victorstoica114/UWB_Module_ESP_IDF/reports/uwb_dynamic_static_comparison_20260812.pdf

# Dynamic and static UWB comparison

## FlexTDOA, Native DS-TWR and Passive DS-TWR

Final field campaign of August 12, 2026

Platform: | 5 ESP32-S3 + DW3000 modules, Raspberry Pi collector
Topology: | M1 tag; M2, M3, M4 and M5 anchors
Radio: | UWB channel 9; configured 40 MHz SPI
Firmware branch: | localization-raw-calibration
UWB evidence: | six complete August 12 JSONL captures; raw and position-only EKF
RTK evidence: | GPS-only reference captures from August 6

Main result. All three protocols produced complete raw dynamic and static datasets. Independent dynamic rates are approximately 25.0 Hz Flex, 25.4 Hz Native and 22.6 Hz Passive. Raw static RMS is 2.3–2.4 cm. The position-only adaptive EKF materially reduces static jitter and dynamic sample-to-sample spikes, while raw UWB remains the permanent audit stream.

Reproducible technical report

## Contents

1 Executive summary | 1
2 Scope and questions | 1
3 System and protocol background | 1
4 Test configuration and captured evidence | 1
5 Methodology | 2
6 Dynamic results | 2
7 Position-only adaptive EKF | 4
8 Static results | 4
9 GPS RTK reference from August 6 | 6
10 Accelerometer scope | 6
11 Protocol interpretation and selection | 6
12 Limitations | 8
13 Recommended next tests | 8
14 Preliminary findings | 8
15 Reproduction and audit files | 8

i

## 1 Executive summary

Evidence boundary. Stream rates, uptime gaps, sample counts, fusion acceptance and reset counts are direct August 12 diagnostics. GPS RTK quality and precision use only the August 6 reference captures. The two sessions are not time-paired, so this report does not calculate or claim August 12 absolute UWB–RTK position error.

Passive DS overlapping raw windows remain visible in the telemetry rate, while all comparative precision and trajectory metrics use independent frames. Interleaved records marked imu fused=true are excluded from raw UWB metrics. Outliers are retained.

The dynamic independent rates were 25.01 positions/s for FlexTDOA, 25.35 positions/s for Native DS-TWR, and 22.63 positions/s for Passive DS-TWR. Passive DS emitted 70.11 dashboard events/s, but those include overlapping windows.

The static raw local RMS values were 2.41 cm (FlexTDOA), 2.45 cm (Native DS-TWR) and 2.26 cm (Passive DS-TWR). These are precision around each capture median, not absolute accuracy.

The UWB and RTK evidence populations are intentionally separated: no August 6 UWB positions enter the protocol results, and no August 12 GPS samples enter the RTK section. The new filter uses positions only: this campaign intentionally does not claim acceleration-derived position improvement.

## 2 Scope and questions

The campaign asks how many independent positions each protocol delivers, where stream gaps occur, how stable the unfiltered stationary position is, and whether the position-only adaptive EKF reduces visible jitter without hiding raw UWB.

The RTK reference was acquired in a separate session. It establishes receiver fix availability and short-term precision, but it cannot be paired sample by sample with the August 12 UWB walks or used as an absolute-error ground truth.

## 3 System and protocol background

### 3.1 FlexTDOA

The tag is UWB receive-only. Anchor transmissions form directed time-difference observations and the tag solves from a recent coherent observation set. Radio airtime is largely independent of the number of passive tags.

### 3.2 Native DS-TWR

The active tag exchanges poll, response and final messages with every anchor, obtains four absolute ranges and solves a coherent frame. Airtime grows with active tag count, but frame semantics are direct.

### 3.3 Passive DS-TWR

The tag listens to anchor-to-anchor DS-TWR exchanges. Rolling windows may produce several publications from shared measurements, so dashboard events and independent frames are intentionally reported separately.

## 4 Test configuration and captured evidence

The three operator-marked dynamic walks lasted 85–114 s and the stationary blocks approximately 30 s. The selector uses the final continuous-capture segments and the final short static capture for each protocol.

Protocol | Mode | Capture ID | duration s | events | independent | indep Hz | coverage pct | complete
FlexTDOA | dynamic | flextdoa final dynamic 20260812 | 84.6 | 2117 | 2117 | 25.01 | 99.7 | yes
Native DS-TWR | dynamic | native ds final dynamic 20260812 | 113.5 | 2876 | 2876 | 25.35 | 98.7 | yes
Passive DS-TWR | dynamic | passive ds final dynamic 20260812 | 106.5 | 7463 | 2409 | 22.63 | 100.0 | yes
FlexTDOA | static | flextdoa static final 01 | 30.3 | 798 | 798 | 26.30 | 98.8 | yes
Native DS-TWR | static | native ds static final 02 rtk fixed | 30.1 | 780 | 780 | 25.89 | 99.6 | yes
Passive DS-TWR | static | passive ds static final 01 | 31.2 | 1906 | 607 | 19.45 | 96.2 | yes
Every selected block has a terminal capture end. All raw data are archived losslessly and identified by SHA-256.

## 5 Methodology

### 5.1 Population and continuity

No error-based trimming or temporal smoothing is applied. Rates use full capture wall time. Gaps are positive differences between unique ESP32 uptime values; P50/P95/P99, maximum and counts above 100 ms are retained together.

### 5.2 Static precision

Radial displacement is computed around each block’s component-wise position median. CEP50, RMS, P95, P99, maximum, 2DRMS and first-to-last-decile drift use all independent samples. They describe repeatability, not offset from truth.

### 5.3 RTK reference

Only quality-4 fixes from the August 6 reference captures enter the RTK section. WGS84 is converted through ECEF to one local ENU frame for that session. No cross-session timestamp association or UWB–RTK rigid fit is performed.

## 6 Dynamic results

### 6.1 Raw trajectories

The walks are separate physical trials, not synchronized repeats. The panels therefore show continuity and gross geometry rather than point-by-point route agreement.

Raw dynamic UWB trajectories - August 12 position captures

A2

A3

A4

A5

FlexTDOA

x [-4.56, 5.78] m | y [-0.47, 9.87] m
n=2117 independent

A2

A3

A4

A5

Native DS-TWR

x [-4.56, 5.78] m | y [-0.47, 9.87] m
n=2876 independent

A2

A3

A4

A5

Passive DS-TWR

x [-4.56, 5.78] m | y [-0.47, 9.87] m
n=2409 independent

Figure 1: August 12 raw independent UWB trajectories in each local frame. Green markers are anchors; no August 6 UWB positions are used.

### 6.2 Update rate and gaps

Protocol | duration s | events | independent | event Hz | indep Hz | gap P95 ms | gap max ms | step P95 m/s
FlexTDOA | 84.6 | 2117 | 2117 | 25.01 | 25.01 | 70 | 830 | 6.04
Native DS-TWR | 113.5 | 2876 | 2876 | 25.35 | 25.35 | 50 | 130 | 7.15
Passive DS-TWR | 106.5 | 7463 | 2409 | 70.11 | 22.63 | 30 | 250 | 4.66

Native DS-TWR delivered the highest independent rate (25.35 Hz) and the best worst-case continuity (130 ms). FlexTDOA was close in rate (25.01 Hz), but its maximum gap was 830 ms. Passive DS delivered 22.63 independent Hz despite overlapping dashboard publications, with a 250 ms maximum gap. Step speed is a sample-to-sample trajectory diagnostic, not measured walking speed.

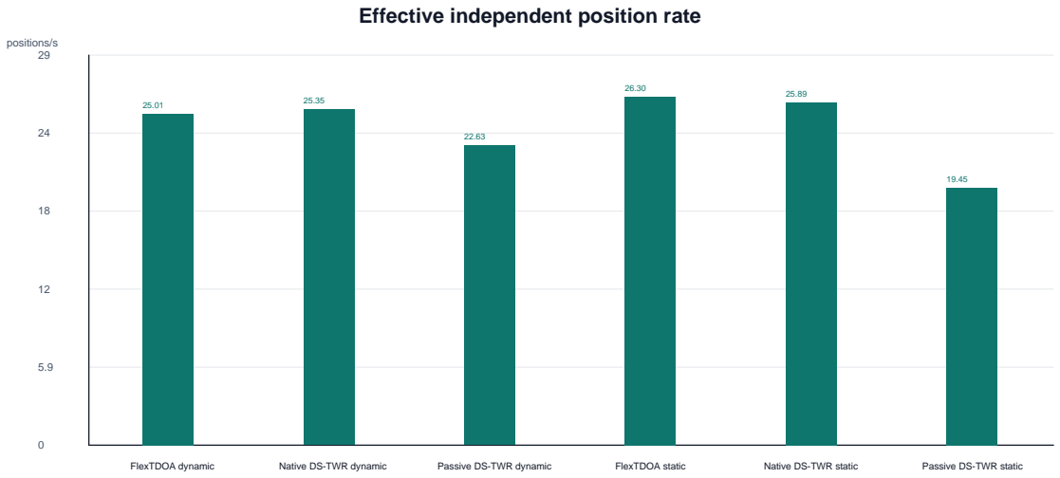
[picture p7: figure]
Effective independent position rate; FlexTDOA dynamic; Native DS-TWR dynamic; Passive DS-TWR dynamic; FlexTDOA static; Native DS-TWR static; Passive DS-TWR static; positions/s

independent Hz

Figure 2: Independent position rate in the selected dynamic and static blocks. Passive DS all-event publications are not substituted for independent frames.

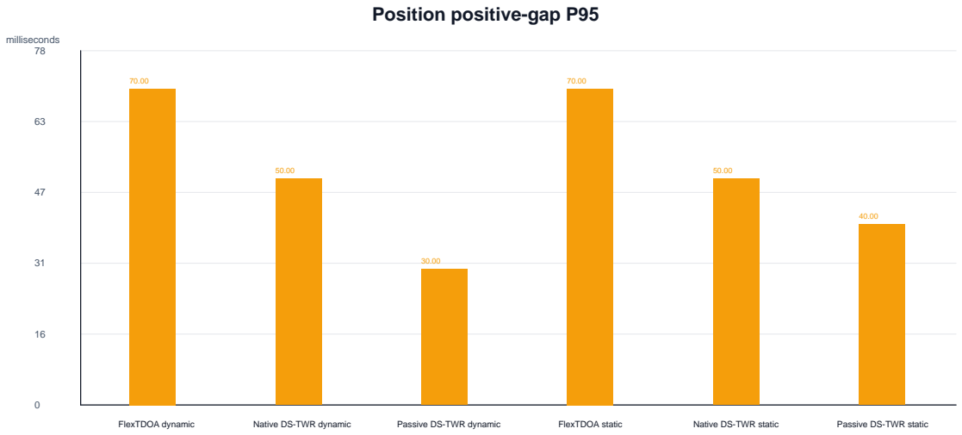
[picture p8: figure]
Position positive-gap P95; FlexTDOA dynamic; Native DS-TWR dynamic; Passive DS-TWR dynamic; FlexTDOA static; Native DS-TWR static; Passive DS-TWR static; milliseconds

gap P95

Figure 3: P95 positive gap between unique position uptimes. Maximum gaps and counts remain in the tables.

### 6.3 Complete continuity audit

Protocol | Mode | event Hz | indep Hz | P50 ms | P95 | P99 | max | ¿100 ms
FlexTDOA | dynamic | 25.01 | 25.01 | 30 | 70 | 130 | 830 | 28
Native DS-TWR | dynamic | 25.35 | 25.35 | 40 | 50 | 70 | 130 | 2
Passive DS-TWR | dynamic | 70.11 | 22.63 | 10 | 30 | 80 | 250 | 28
FlexTDOA | static | 26.30 | 26.30 | 30 | 70 | 100 | 120 | 7
Native DS-TWR | static | 25.89 | 25.89 | 40 | 50 | 60 | 80 | 0
Passive DS-TWR | static | 61.06 | 19.45 | 10 | 40 | 72 | 130 | 6

## 7 Position-only adaptive EKF

The dashboard EKF uses only the raw UWB position stream. IMU acceleration is disabled, raw measurements remain archived separately, and each EKF result in this report comes from the same position event as its raw counterpart. Sample-to-sample step-speed P95 is a jitter/continuity diagnostic; it is not physical walking speed. Static RMS is repeatability about each stream’s own median. No cross-session RTK error is attached to the filter results.

Protocol | Mode | coverage pct | raw step P95 | EKF step P95 | raw static RMS cm | EKF static RMS cm
FlexTDOA | dynamic | 100.0 | 6.04 | 4.31 | n/a | n/a
Native DS-TWR | dynamic | 100.0 | 7.15 | 3.44 | n/a | n/a
Passive DS-TWR | dynamic | 100.0 | 4.66 | 4.50 | n/a | n/a
FlexTDOA | static | 100.0 | 1.97 | 0.36 | 2.41 | 1.07
Native DS-TWR | static | 100.0 | 1.61 | 0.23 | 2.45 | 0.89
Passive DS-TWR | static | 100.0 | 1.62 | 0.00 | 2.26 | 0.00

Dynamic raw versus position-only adaptive EKF

FlexTDOA

raw n=2117; EKF n=2117

Native DS-TWR

raw n=2876; EKF n=2876

Passive DS-TWR

raw n=2409; EKF n=2409

raw independent | position-only adaptive EKF

Figure 4: Raw independent dynamic trajectory (blue) and the position-only adaptive EKF (green). The EKF reduces high-frequency corners without replacing archived raw data.

## 8 Static results

### 8.1 Raw local precision

Protocol | N | CEP50 cm | RMS cm | P95 cm | P99 cm | max cm | 2DRMS cm | drift cm
FlexTDOA | 798 | 1.91 | 2.41 | 4.30 | 5.73 | 7.38 | 4.81 | 0.82
Native DS-TWR | 780 | 1.72 | 2.45 | 3.95 | 8.81 | 12.30 | 4.84 | 0.67
Passive DS-TWR | 607 | 1.88 | 2.26 | 3.94 | 4.93 | 5.52 | 4.53 | 0.38

All raw static RMS values lie in a narrow 2.26–2.45 cm range. Passive DS is best on RMS, while Native and Passive share the best P95 near 3.94 cm. All outliers are retained. One stationary point cannot characterize GDOP or spatial bias across the anchor polygon.

Static raw versus position-only adaptive EKF

FlexTDOA

raw n=798; EKF n=798

Native DS-TWR

raw n=780; EKF n=780

Passive DS-TWR

raw n=607; EKF n=607

raw independent | position-only adaptive EKF

Figure 5: Static raw and EKF clouds, each centered on its own median and plotted at one common scale. Passive DS may collapse to a held point while stationary by design.

Static precision; independent-frame samples

0

0.0096

0.019

0.029

0.039

0.048

0.02

0.04

FlexTDOA

0.02

0.04

Native DS-TWR

0.02

0.04

Passive DS-TWR

CEP50 | P95

radial displacement [m]

Figure 6: Static precision around each block’s own median. All independent raw samples are included.

Static raw UWB position clouds - August 12 captures

FlexTDOA

x [-0.13, 0.13] m | y [-0.13, 0.13] m
n=798 independent

Native DS-TWR

x [-0.13, 0.13] m | y [-0.13, 0.13] m
n=780 independent

Passive DS-TWR

x [-0.13, 0.13] m | y [-0.13, 0.13] m
n=607 independent

Figure 7: Static raw position clouds centered on their own medians and drawn at one common scale. The cross is the median.

## 9 GPS RTK reference from August 6

This section contains GPS data only. It characterizes RTK availability and short-term scatter for the unchanged receiver path; it does not reuse the old UWB trajectories and it is not synchronized with the August 12 walks.

Protocol | Mode | tag total | tag fixed | tag fixed pct | all modules fixed pct | fix-age P95 ms | fixed anchors | tag cloud RMS cm | tag cloud P95 cm
FlexTDOA | dynamic | 24 | 24 | 100.0 | 93.0 | 96 | 4 | 284.65 | 482.34
Native DS-TWR | dynamic | 30 | 28 | 93.3 | 55.9 | 96 | 3 | 334.51 | 487.56
Passive DS-TWR | dynamic | 26 | 25 | 96.2 | 72.2 | 106 | 4 | 367.91 | 625.14
FlexTDOA | static | 119 | 119 | 100.0 | 91.4 | 100 | 4 | 0.52 | 0.85
Native DS-TWR | static | 119 | 119 | 100.0 | 86.3 | 100 | 4 | 0.74 | 1.15
Passive DS-TWR | static | 119 | 102 | 85.7 | 93.0 | 130 | 4 | 1.40 | 2.02
The trajectory panels below are GPS-only and remain in the August 6 ENU frame. They are shown as a qualitative RTK reference, not overlaid on the August 12 UWB paths.

## 10 Accelerometer scope

Acceleration-assisted positioning was disabled for this final campaign because the preceding experiment did not improve raw UWB accuracy. The adaptive EKF assessed above is position-only. Orientation/IMU telemetry is outside the protocol ranking, and raw UWB remains the permanent audit stream.

## 11 Protocol interpretation and selection

### 11.1 FlexTDOA

Near-25 Hz independent dynamic rate with a receive-only scalable tag. Static raw RMS was 2.41 cm. The 830 ms maximum gap is the principal caveat.

### 11.2 Native DS-TWR

Clearest coherent-frame semantics, highest measured independent rate and best maximum gap. Static raw RMS was 2.45 cm. It remains the preferred deterministic baseline for a small number of active tags.

### 11.3 Passive DS-TWR

Successfully follows motion without tag transmissions. Independent-frame accounting yields 22.63 Hz despite overlapping publications; static raw RMS was the best at 2.26 cm and the maximum dynamic gap was 250 ms.

GPS RTK Fixed tag clouds and cross-capture centers - August 6 RTK reference

Top: each block centered on its own median. Bottom: the same fixes in one common ENU frame.

FlexTDOA

E/N +/-4.2 cm; n=119 fixed

Native DS-TWR

E/N +/-4.2 cm; n=119 fixed

Passive DS-TWR

E/N +/-4.2 cm; n=102 fixed

FlexTDOA
center E=0.004, N=0.682 m
Native DS-TWR
center E=-0.002, N=0.681 m
Passive DS-TWR
center E=-0.066, N=2.262 m

Common ENU frame; equal East/North scale

East [-0.92, 0.87] m | North [0.57, 2.36] m

Figure 8: August 6 GPS RTK Fixed tag solutions only. Top: each reference block centered on its own median. Bottom: the same fixes in the August 6 common ENU frame. GPS RTK Fixed dynamic reference trajectories - August 6 RTK reference

FlexTDOA

x [-3.75, 5.86] m | y [-6.22, 3.39] m
n=24 RTK Fixed tag fixes

Native DS-TWR

x [-3.62, 6.95] m | y [-5.09, 5.48] m
n=28 RTK Fixed tag fixes

Passive DS-TWR

x [-5.34, 5.07] m | y [-8.61, 1.80] m
n=25 RTK Fixed tag fixes

Figure 9: August 6 GPS RTK Fixed dynamic reference trajectories. No UWB positions from that session are plotted.

Criterion | FlexTDOA | Native DS-TWR | Passive DS-TWR
Tag radio role | receive-only | active exchanges | receive-only
Dynamic | independent
rate | 25.01 Hz | best: 25.35 Hz | 22.63 Hz
Dynamic worst gap | 830 ms | best: 130 ms | 250 ms
Static raw precision | 2.41 cm RMS | 2.45 cm RMS | best: 2.26 cm RMS
Scaling with tag count | strongest | airtime grows | strong
Recommendation | primary scalable mode | coherent baseline | passive scalable alternative

## 12 Limitations

- RTK is a separate August 6 reference session, not synchronized August 12 truth.
- Cross-session UWB–RTK RMSE/P95 is intentionally not computed.
- GNSS and UWB antenna phase centers have unknown lever arms.
- Dynamic routes are not repeated surveyed paths; static/dynamic blocks are single trials.
- One static point does not cover edge geometry, NLOS, orientation or spatial bias.
- Collector rate is end-to-end telemetry, not direct DW3000 PHY throughput.

## 13 Recommended next tests

1. Repeat every protocol on one marked route with identical orientation and synchronized markers.
2. Interleave static blocks at the center, edges and outside the polygon.
3. Repeat the final UWB campaign with one simultaneous continuous RTK session.
4. Add hardware-correlated timestamps for latency claims.
5. Keep acceleration disabled until body-to-map yaw is independently validated.
6. Capture focused FlexTDOA diagnostics around gaps above 250 ms.

## 14 Preliminary findings

- FlexTDOA remains a strong receive-only scalable mode, with one long-gap caveat.
- Native DS-TWR is the best coherent-frame rate and continuity baseline.
- Passive DS-TWR is a viable receive-only alternative when independent frames are counted correctly.
- The cross-session RTK reference cannot support an August 12 absolute-accuracy ranking; local UWB precision is ranked.
- The position-only EKF improves display stability; acceleration-assisted accuracy is not claimed.

## 15 Reproduction and audit files

The directory contains analysis summary.json, capture/replay/alignment CSV files, SVG/PDF plots and this TeX source. The machine-readable summary records whether optional lossless RAW archive generation was enabled; when it is skipped, immutable source JSONL paths remain recorded for reproduction.

python tools/uwb_dynamic_static_report.py ‘
--input-dir reports/uwb_final_report_input_20260812 ‘
--output-dir reports/uwb_dynamic_static_comparison_20260812 ‘ --rtk-reference-report-dir reports/uwb_dynamic_static_comparison_20260806

No raw capture is modified during report generation.
