victorstoica114/UWB_Module_ESP_IDF/reports/passive_ds_known_geometry_20260727.pdf

## Passive DS-TWR Known-Geometry Calibration

Static receive-only tag validation

UWB Module project

27 July 2026

Abstract

This report validates the project-specic Passive DS-TWR protocol after restoring a surveyed four-anchor geometry. Hardware-bias calibration reduces the live position-bias magnitude from 3.51 cm to 0.96 cm. The embedded solver improves from 4.12 cm to 3.33 cm 2-D RMSE. Re-solving the same calibrated observations with the surveyed geometry reaches 1.89 cm RMSE and 3.11 cm P95 at 49.17 complete frames/s. The nal static position therefore improves. A direct before/after comparison also shows that the range calibration works very well, while the directed-observation calibration still interacts with the range correction and requires a joint ret.

## 1 Experimental setup

Four anchors formed a surveyed 3.000 m square and tag 1 was placed at its center:

Node | Coordinate [m] | Node | Coordinate [m]
A2 | (0.000, 0.000) | A3 | (0.000, 3.000)
A4 | (3.000, 0.000) | A5 | (3.000, 3.000)
Tag 1 | (1.500, 1.500) | Placement tolerance | approximately ±2 mm

Both independent captures lasted 120 s and used Robust Rotating scheduling, 5 ms slots, a 1 ms frame gap, 1000 us RESP and FINAL delays, and UWB channel 5. The rst capture used raw observations and raw piggybacked DS ranges. The second capture used the calibration derived from the rst capture.

2 | Position results
Processing path | Positions | Rate [Hz] | Bias X/Y [cm] | RMSE [cm] | P95 [cm]
Uncalibrated, autonomous geometry | 3,362 | 28.00 | +3.24/ − 1.35 | 4.12 | 6.09
Calibrated, autonomous geometry | 3,512 | 29.26 | −0.66/ − 0.70 | 3.33 | 5.66
Calibrated, surveyed geometry | 5,901 | 49.17 | −0.30/ − 0.27 | 1.89 | 3.11

Calibration improves the live embedded RMSE by 19.2% and reduces the systematic position-bias magnitude by 72.7%. The HTTP snapshot collector keeps only the newest embedded position, so its 2829 samples/s is a capture limit. Oine reconstruction of one solution per complete three-slot star shows the actual 49.2 frames/s position cadence.

Calibration eect | Before [cm] | After [cm] | Change
Live position RMSE | 4.12 | 3.33 | 19.2% better
Position-bias magnitude | 3.51 | 0.96 | 72.7% better
Mean absolute eective-range bias | 5.63 | 0.17 | 96.9% better
Mean absolute directed-path bias | 4.65 | 5.33 | 14.7% worse

The current calibration therefore helps the nal position and nearly removes pair-range bias, but it does not yet independently calibrate every directed observation.

1.55

1.60

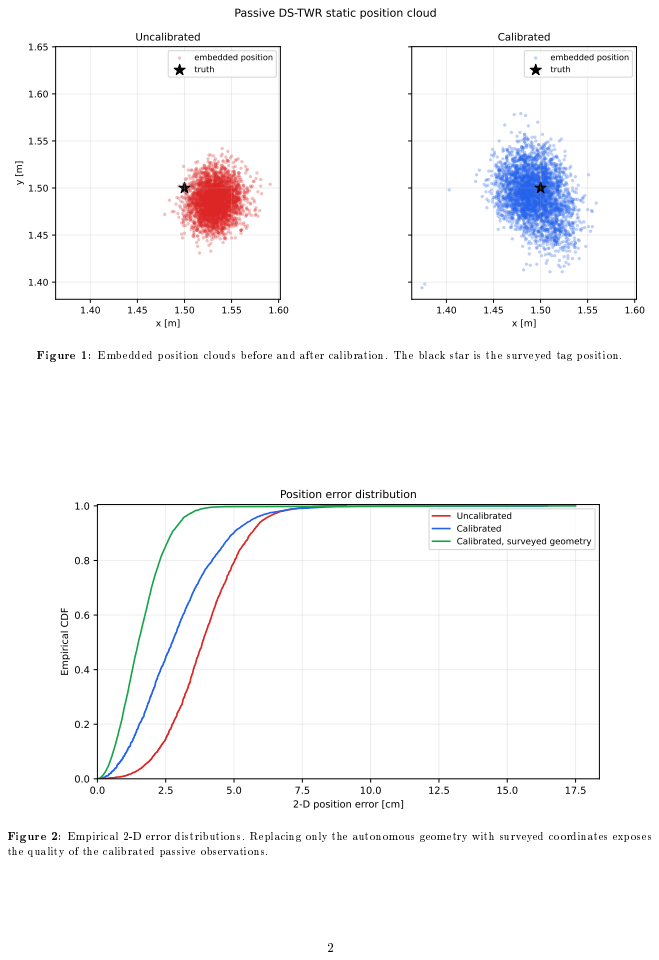
[picture p32: page 2]
Uncalibrated; embedded position truth; Calibrated; Empirical CDF

Passive DS-TWR static position cloud

Figure 1: Embedded position clouds before and after calibration. The black star is the surveyed tag position.

Position error distribution

Uncalibrated
Calibrated
Calibrated, surveyed geometry

2-D position error [cm]

Figure 2: Empirical 2-D error distributions. Replacing only the autonomous geometry with surveyed coordinates exposes
the quality of the calibrated passive observations.

## 3 Calibration model

The scalable directed-observation model is
eI→R = bR − bI ,

where bI and bR are per-anchor biases. A2 xes the arbitrary common oset. The rst half of the uncalibrated observation capture produced:

Anchor | Observation bias | Anchor | Observation bias
A2 | | 0 mm | A3 | | +34 mm
A4 | | −16 mm | A5 | | −55 mm

This uses only N − 1 independent values for N anchors and ts the antisymmetric component of all 12 directed paths. The piggybacked DS ranges use one additional correction per unordered anchor pair:

Pair | Bias | Pair | Bias | Pair | Bias
A2A3 | +71 mm | A2A4 | +56 mm | A2A5 | −49 mm
A3A4 | +67 mm | A3A5 | +66 mm | A4A5 | −29 mm

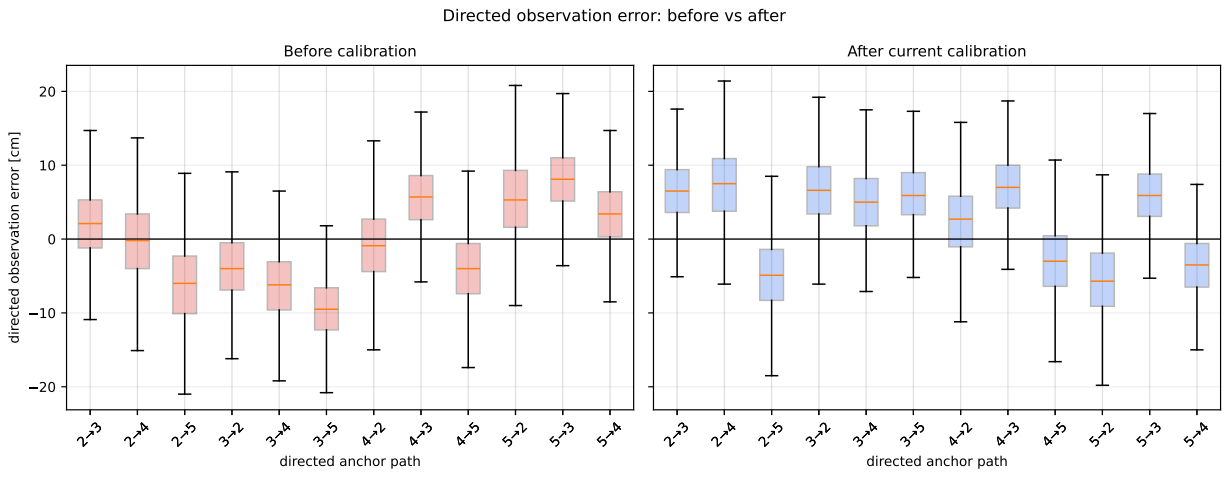
[picture p33: figure]
directed anchor path; directed observation error [cm]; Before calibration; After current calibration

Directed observation error: before vs after

Figure 3: Direct before/after comparison on the same scale. The current combined calibration does not move every directed-path median toward zero.

## 4 Protocol health and interpretation

During the calibrated capture, anchor radio success ranged from 97.37% to 98.49%. The embedded calibrated distribution contains ve estimates above 10 cm (0.142%), including two above 15 cm. They are short transients and remain included in every reported statistic and plot.

The uncorrected pair distances still t a planar geometry with 1.99 cm range-residual RMS, but the resulting anchor coordinates are displaced by several centimeters. The direct comparison supports the following conclusions:

| CFO correction of the responder reply interval is working;
| piggybacked DS ranges clearly benet from per-pair corrections;
| nal static position RMSE and bias improve;
| the independent per-anchor observation t is incomplete once the range correction is active;
| autonomous geometry and the observation/range interaction remain accuracy penalties.

The next implementation step is a joint observation t performed after range correction, with an antisymmetric per-anchor term and, if needed, a symmetric per-pair observation term. Pair ranges should then be robustly ltered before they update geometry: a rolling median or Huber estimate, a physical-change gate, and a slower geometry-update cadence. Validation should cover several static tag locations and a dynamic trajectory. A single center position identies the current bias, but cannot establish workspace-wide accuracy.

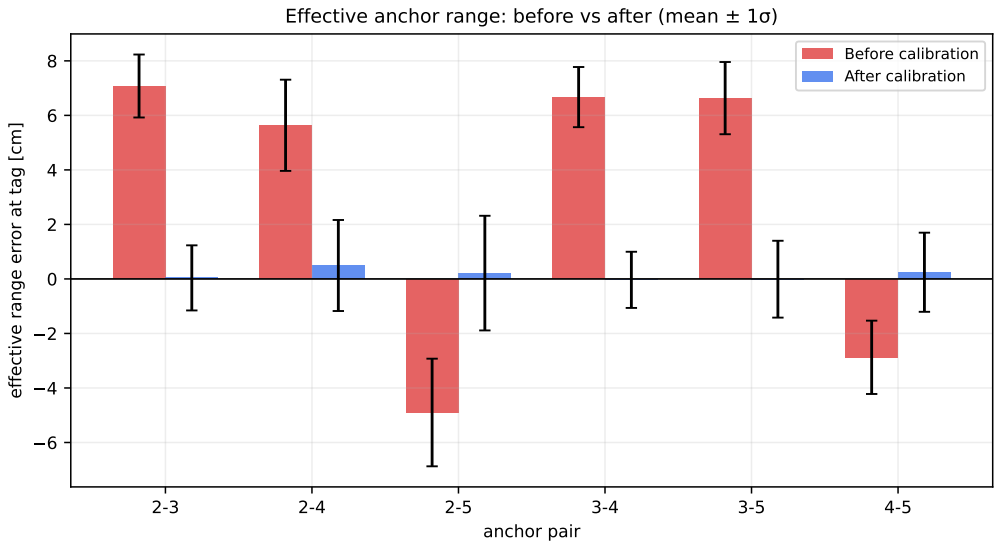
[picture p34: figure]
anchor pair; effective range error at tag [cm]; Before; calibration; After calibration

Effective anchor range: before vs after (mean ± 1 )

Figure 4: The eective anchor range used by the tag before and after calibration. Pair-range bias is almost completely removed.

## 5 Reproducibility

The repository preserves both compressed JSONL captures, metadata, wireless logs, SHA-256 manifests, CSV metrics, gures, and the deterministic analyzer:

python3 tools/uwb_passive_ds_known_geometry_analyze.py

The complete machine-readable result is in analysis_summary.json; detailed methodology is in README.md.

Branch: experiment/passive-ds-twr Calibration rmware: 8db125e
