victorstoica114/UWB_Module_ESP_IDF/reports/uwb_dynamic_static_comparison_20260813.pdf

# Dynamic and static UWB comparison

## FlexTDOA, Native DS-TWR and Passive DS-TWR

Field campaign of August 13, 2026

Platform: | 5 ESP32-S3 + DW3000 modules, Raspberry Pi collector
Topology: | M1 tag; M2, M3, M4 and M5 anchors
Radio: | UWB channel 9
Position streams: | raw independent UWB and position-only adaptive EKF
Reference: | embedded GPS RTK telemetry, quality audited per capture

Main result. All six protocol/motion cells are populated. Dynamic continuity is directly measur-able, and static local precision is consistently at centimetre scale. RTK anchor registration passes for some, but not all, captures, so no complete three-protocol absolute-accuracy ranking is claimed; raw UWB remains the audit stream.

Reproducible technical report

## Contents

1 Executive summary | 1
2 Scope and protocol background | 1
3 Captured evidence | 1
4 Dynamic results | 1
5 Position-only adaptive EKF | 3
6 Static results | 3
7 RTK association audit | 6
8 Interpretation | 8
9 Limitations | 8
10 Reproduction and audit files | 8

i

## 1 Executive summary

Evidence boundary. Rates, gaps, sample counts, local static precision and raw-versus-EKF comparisons are direct capture diagnostics. RTK is an in-system reference, not independently surveyed truth. Every RTK residual must be read with its per-row anchor-fit grade; a failed fit invalidates that row and prevents
a complete cross-protocol absolute-accuracy ranking.

The dynamic independent rates were 17.68 positions/s for FlexTDOA, 21.32 positions/s for Native DS-TWR and 23.83 positions/s for Passive DS-TWR. Maximum observed gaps were 1740, 600 and 700 ms respectively.

Static raw local RMS was 2.33 cm for FlexTDOA, 2.45 cm for Native DS-TWR and 2.45 cm for Passive DS-TWR. These values measure repeatability around each capture median, not absolute position error.

## 2 Scope and protocol background

The campaign compares the published position streams of three independent UWB protocols. FlexTDOA and Passive DS-TWR keep the tag radio receive-only. Native DS-TWR performs active tag-to-anchor exchanges and provides the coherent-frame baseline. Passive rolling windows may publish multiple events from shared radio measurements, so all-event and independent-frame rates are reported separately.

## 3 Captured evidence

Protocol | Mode | Capture ID | duration s | events | independent | indep Hz | coverage pct | epochs
FlexTDOA | dynamic | flextdoa final dynamic 20260813 | 466.7 | 8252 | 8252 | 17.68 | 99.7 | 1
Native DS-TWR | dynamic | native ds final dynamic 20260813 | 74.0 | 1578 | 1578 | 21.32 | 99.9 | 1
Passive DS-TWR | dynamic | passive ds final dynamic 20260813 | 148.7 | 10821 | 3542 | 23.83 | 100.0 | 1
FlexTDOA | static | static flextdoa 20260813 | 31.6 | 454 | 454 | 14.39 | 77.7 | 1
Native DS-TWR | static | native ds static final 02 rtk fixed | 30.1 | 780 | 780 | 25.89 | 99.6 | 1
Passive DS-TWR | static | static passive ds 20260813 | 7.6 | 568 | 182 | 23.99 | 98.1 | 1

### 3.1 Capture-quality notices

These notices do not invalidate the retained samples, but they limit how far the affected block can be generalized.

Protocol | Mode | envelope s | active span s | notice
FlexTDOA | static | 31.56 | 24.52 | position coverage below 80%; first position at +6.52 s
Passive DS-TWR | static | 7.59 | 7.44 | short capture; interpret static precision as indicative

All selected blocks have terminal capture envelopes. Derived blocks are lossless time slices of source JSONL captures. The raw records are not smoothed, trimmed by error or rewritten by the report generator.

## 4 Dynamic results

### 4.1 Raw trajectories

The routes are separate physical trials. Their panels support continuity and gross-shape inspection; they are not synchronized point-by-point repeats.

### 4.2 Update rate and gaps

Protocol | duration s | events | independent | event Hz | indep Hz | gap P95 ms | gap max ms | step P95 m/s
FlexTDOA | 466.7 | 8252 | 8252 | 17.68 | 17.68 | 100 | 1740 | 1.72
Native DS-TWR | 74.0 | 1578 | 1578 | 21.32 | 21.32 | 80 | 600 | 5.70
Passive DS-TWR | 148.7 | 10821 | 3542 | 72.79 | 23.83 | 30 | 700 | 3.64

### 4.3 Complete continuity audit

Uptime epochs are separated at multi-second backsteps, so a protocol restart is never turned into a synthetic gap or step-speed measurement.

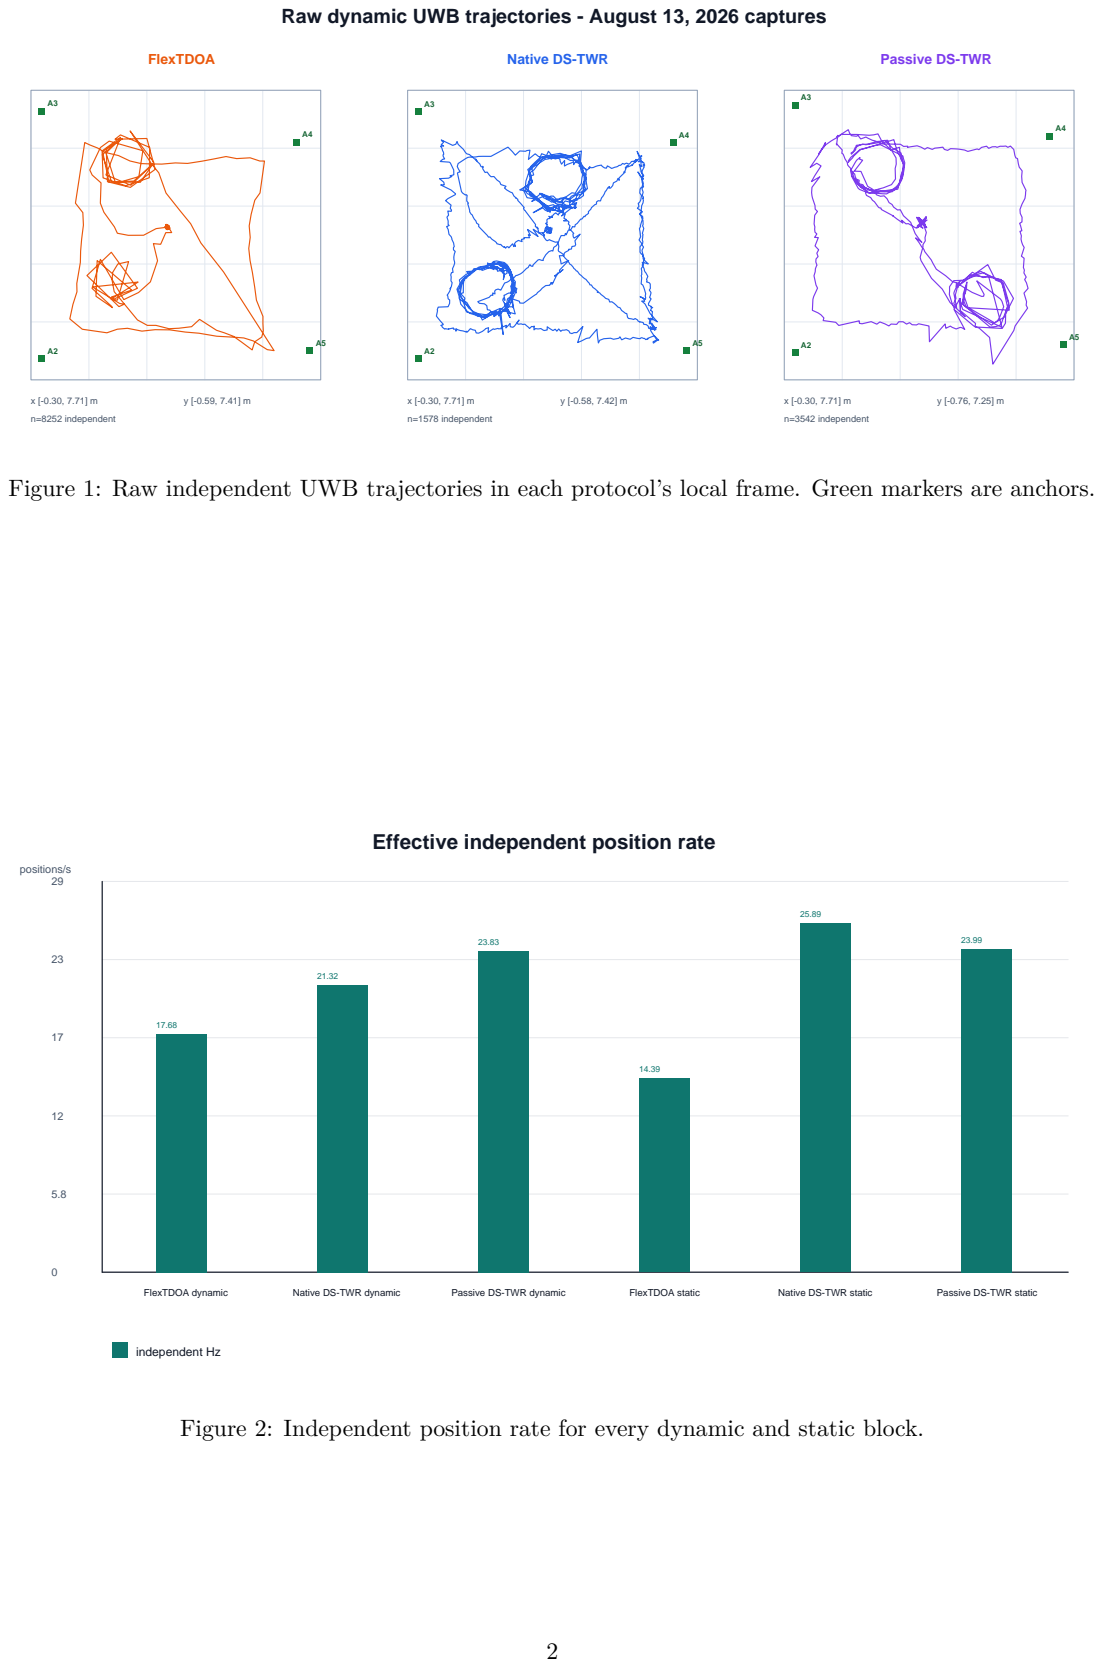
[picture p47: page 4]
FlexTDOA; n=8252 independent; n=1578 independent; n=3542 independent; FlexTDOA dynamic; FlexTDOA static; independent Hz; positions/s

Raw dynamic UWB trajectories - August 13, 2026 captures

Native DS-TWR

Passive DS-TWR

Figure 1: Raw independent UWB trajectories in each protocol’s local frame. Green markers are anchors.

Effective independent position rate

Native DS-TWR dynamic

Passive DS-TWR dynamic

Native DS-TWR static

Passive DS-TWR static

Figure 2: Independent position rate for every dynamic and static block.

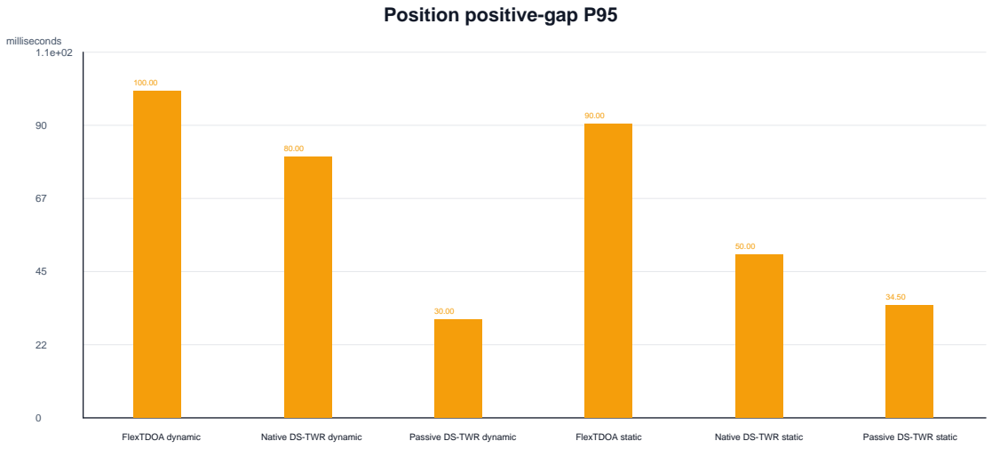
[picture p48: figure]
Position positive-gap P95; FlexTDOA dynamic; Native DS-TWR dynamic; Passive DS-TWR dynamic; FlexTDOA static; Native DS-TWR static; Passive DS-TWR static; milliseconds

gap P95

Figure 3: P95 positive position gap. Maximum gaps and counts remain in the tables.

Protocol | Mode | event Hz | indep Hz | P50 ms | P95 | P99 | max | gaps over 100 ms
FlexTDOA | dynamic | 17.68 | 17.68 | 50 | 100 | 150 | 1740 | 205
Native DS-TWR | dynamic | 21.32 | 21.32 | 40 | 80 | 130 | 600 | 25
Passive DS-TWR | dynamic | 72.79 | 23.83 | 10 | 30 | 90 | 700 | 78
FlexTDOA | static | 14.39 | 14.39 | 50 | 90 | 110 | 150 | 9
Native DS-TWR | static | 25.89 | 25.89 | 40 | 50 | 60 | 80 | 0
Passive DS-TWR | static | 74.86 | 23.99 | 10 | 34 | 87 | 150 | 3

## 5 Position-only adaptive EKF

The dashboard EKF consumes UWB positions only; acceleration is disabled. Raw measurements remain archived, and each valid EKF point is tied to its raw event. Step-speed P95 is a jitter diagnostic rather than physical walking speed.

Protocol | Mode | coverage pct | raw step P95 | EKF step P95 | raw static RMS cm | EKF static RMS cm
FlexTDOA | dynamic | 100.0 | 1.72 | 1.26 | n/a | n/a
Native DS-TWR | dynamic | 100.0 | 5.70 | 4.34 | n/a | n/a
Passive DS-TWR | dynamic | 100.0 | 3.64 | 3.47 | n/a | n/a
FlexTDOA | static | 100.0 | 1.10 | 0.15 | | 2.33 | 1.05
Native DS-TWR | static | 100.0 | 1.61 | 0.23 | | 2.45 | 0.89
Passive DS-TWR | static | 100.0 | 1.64 | 1.23 | | 2.45 | 1.96

## 6 Static results

Static precision is radial displacement around each block’s own component-wise median. All independent samples and outliers are retained.

Protocol | N | CEP50 cm | RMS cm | P95 cm | P99 cm | max cm | drift cm
FlexTDOA | 454 | 1.92 | 2.33 | 4.12 | 5.14 | 5.70 | 1.20
Native DS-TWR | 780 | 1.72 | 2.45 | 3.95 | 8.81 | 12.30 | 0.67
Passive DS-TWR | 182 | 1.79 | 2.45 | 4.41 | 6.76 | 10.40 | 0.43

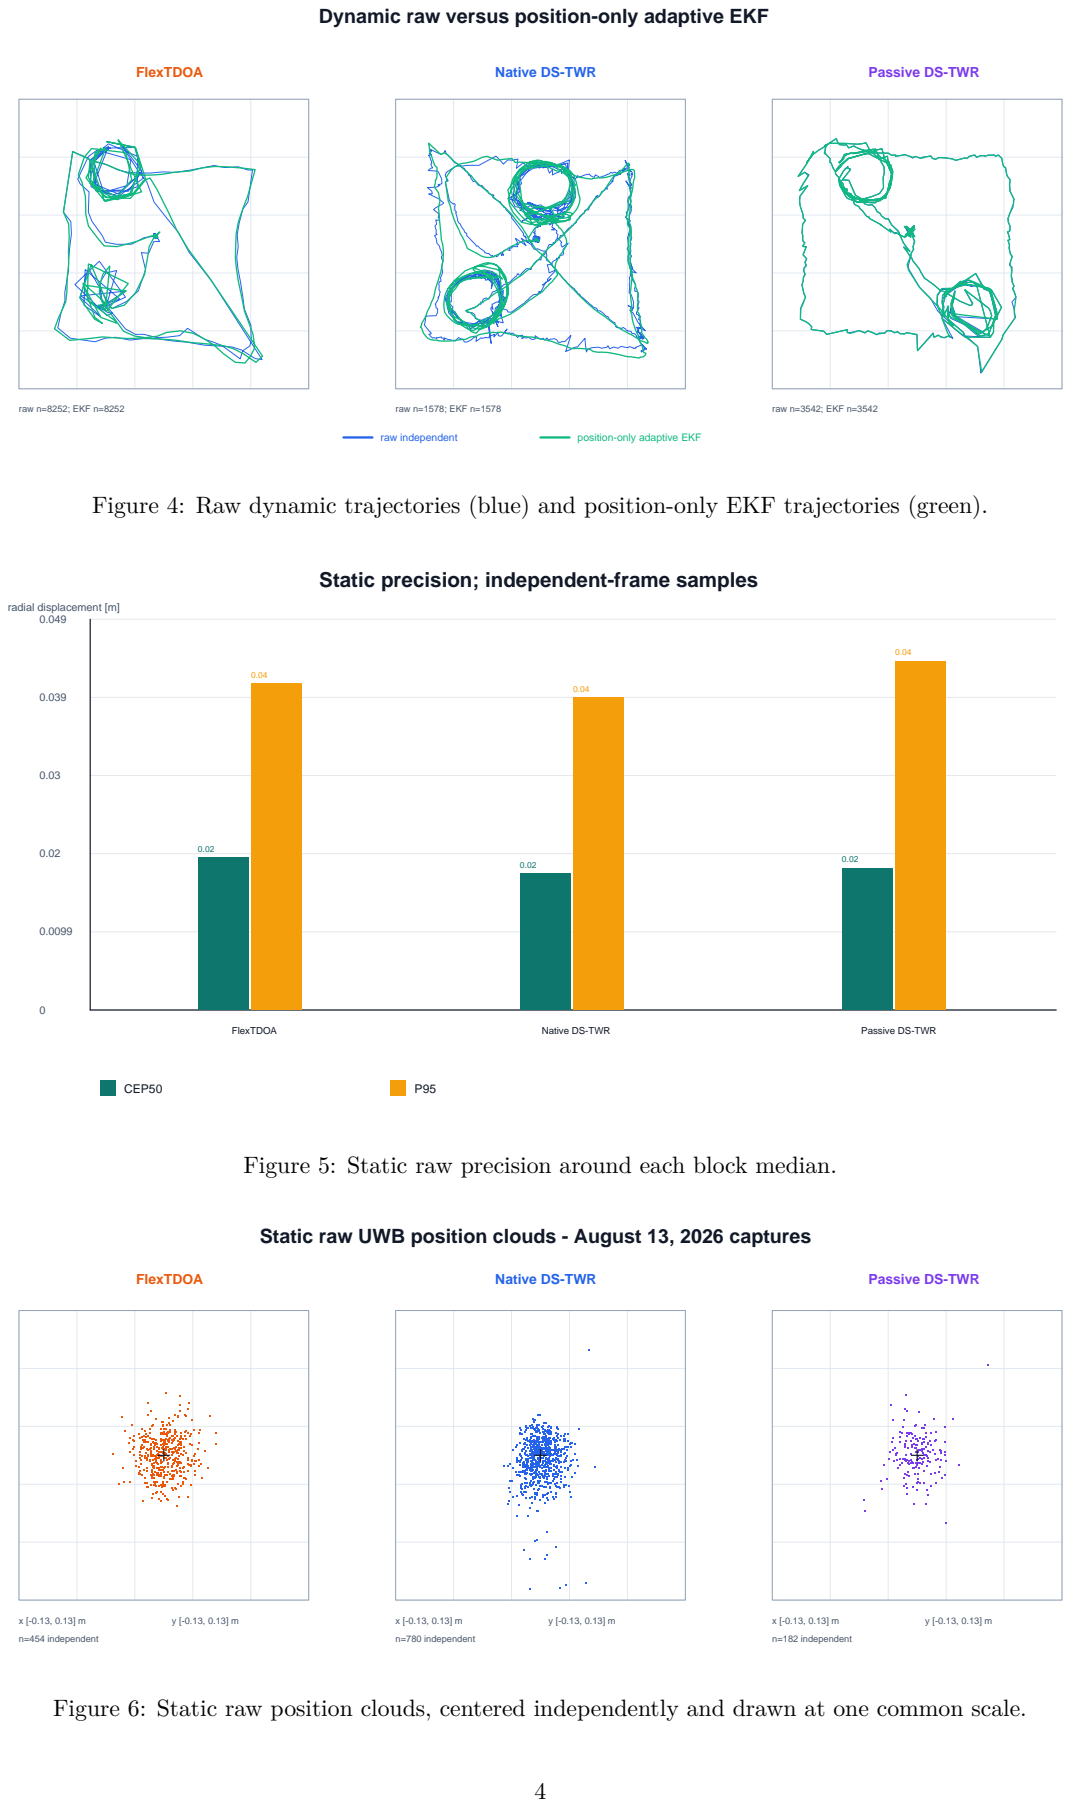
[picture p49: page 6]
FlexTDOA; raw n=8252; EKF n=8252; raw n=1578; EKF n=1578; raw n=3542; EKF n=3542; raw independent; position-only adaptive EKF; CEP50; radial displacement [m]; n=454 independent; n=780 independent; n=182 independent

Dynamic raw versus position-only adaptive EKF

Native DS-TWR

Passive DS-TWR

Figure 4: Raw dynamic trajectories (blue) and position-only EKF trajectories (green).

Static precision; independent-frame samples

Figure 5: Static raw precision around each block median.

Static raw UWB position clouds - August 13, 2026 captures

Figure 6: Static raw position clouds, centered independently and drawn at one common scale.

Static raw versus position-only adaptive EKF

FlexTDOA

raw n=454; EKF n=454

Native DS-TWR

raw n=780; EKF n=780

Passive DS-TWR

raw n=182; EKF n=182

raw independent | position-only adaptive EKF

Figure 7: Static raw and position-only EKF clouds, each centered on its own median.

## 7 RTK association audit

Each quality-4 tag solution contributes at most one pair. The nearest independent UWB position must lie within 100 ms. The UWB frame is registered to robust RTK anchor centers using the better ID-keyed direct or reflected rigid transform. Scale is fixed at one and is never fitted. The reported anchor-fit value is the P95, across captured geometry snapshots, of the four-anchor RMSE. A row is graded usable only when the worst snapshot RMSE is at most 0.5 m, anchor RTK spread is at most 0.5 m and reflection choice is consistent.

The stationary-tag cross-capture separation is 2.384 m, against a 0.250 m consistency gate. The gate fails. Absolute static ranking is therefore invalid.

Protocol | Mode | pairs | time P95 ms | RMSE m | P95 m | debiased RMSE m | fit RMSE P95 m | grade
FlexTDOA | dynamic | 3635 | 38.8 | 0.218 | 0.263 | 0.087 | 0.411 | usable with limits
Native DS-TWR | dynamic | 549 | 34.6 | 0.473 | 0.731 | 0.306 | 1.056 | poor; no accuracy claim
Passive DS-TWR | dynamic | 1171 | 52.4 | 0.224 | 0.346 | 0.163 | 0.410 | usable with limits
FlexTDOA | static | 97 | 30.8 | 0.237 | 0.260 | 0.022 | 0.390 | usable with limits
Native DS-TWR | static | 0 | n/a | n/a | n/a | n/a | n/a | unavailable
Passive DS-TWR | static | 59 | 64.8 | 0.219 | 0.256 | 0.031 | 0.391 | usable with limits

### Dynamic paired residual CDF (see anchor-fit grade)

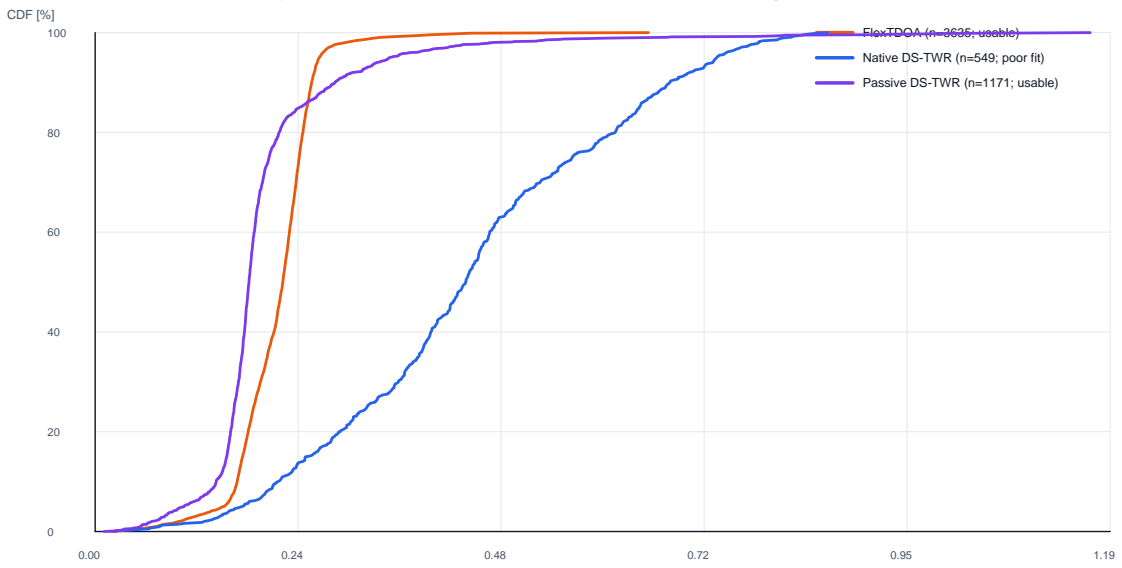
[picture p50: figure]
FlexTDOA (n=3635; usable); Native DS-TWR (n=549; poor fit); Passive DS-TWR (n=1171; usable); CDF [%]

aligned UWB - RTK disagreement [m]

Figure 8: Dynamic UWB–RTK residual CDF. Each legend entry includes its anchor-fit grade; RTK is not surveyed truth.

Anchor-registration RMSE (P95 across snapshots)

0

0.24

0.47

0.71

0.95

1.2

0.41

0.22

FlexTDOA dynamic

1.06

0.47

Native DS-TWR dynamic

0.41

0.22

Passive DS-TWR dynamic

0.39

0.24

FlexTDOA static

0.39

0.22

Passive DS-TWR static

anchor-fit RMSE P95 | paired tag RMSE

metres

Figure 9: Best direct/reflected fixed-scale anchor-registration residual. The per-row grade controls interpretation.

GPS RTK Fixed tag clouds and cross-capture centers

Top: each block centered on its own median. Bottom: the same fixes in one common ENU frame.

FlexTDOA

E/N +/-1.0 cm; n=98 fixed

Native DS-TWR

E/N +/-1.0 cm; n=240 fixed

Passive DS-TWR

E/N +/-1.0 cm; n=59 fixed

FlexTDOA
center E=-0.008, N=-0.013 m
Native DS-TWR
center E=1.340, N=-1.979 m
Passive DS-TWR
center E=-0.007, N=-0.011 m

Common ENU frame; equal East/North scale

East [-0.42, 1.75] m | North [-2.08, 0.09] m

Figure 10: RTK Fixed stationary tag clouds and cross-capture centers.

## 8 Interpretation

- Passive DS-TWR has the highest independent dynamic rate in this dataset; its all-event rate is higher because rolling windows overlap.
- Native DS-TWR provides the best maximum dynamic gap among the three selected walks and remains the coherent active-ranging baseline.
- FlexTDOA preserves a receive-only tag but shows the longest gaps in this campaign.
- Static local precision is similar across all protocols. The EKF reduces visible stationary jitter but is not a replacement for raw UWB.
- FlexTDOA and Passive DS-TWR pass the configured dynamic anchor-fit gate; Native DS-TWR does not, so a complete absolute RTK ranking is not made.

## 9 Limitations

- RTK is an in-system comparison reference, not independently surveyed truth.
- GPS and UWB measurement times are associated in software, not by one hardware clock.
- GNSS and UWB antenna phase centers have unknown lever arms.
- Routes are single trials rather than randomized synchronized repeats.
- One static position does not characterize edge GDOP, NLOS or spatial bias.
- Collector rate measures the complete telemetry path, not DW3000 PHY throughput.

## 10 Reproduction and audit files

The directory contains machine-readable JSON/CSV results, SVG/PDF figures, losslessly compressed raw captures, SHA-256 checksums and this TeX source.

$reportArgs = @(
"--input-dir", "reports/uwb_final_report_input_20260813" "--output-dir", "reports/uwb_dynamic_static_comparison_20260813" "--replay-dynamic-dir", "reports/uwb_final_report_input_20260813" "--replay-static-dir", "reports/uwb_final_report_input_20260813" )
python tools/uwb_dynamic_static_report.py @reportArgs

No raw capture is modified during report generation.
