victorstoica114/UWB_Module_ESP_IDF/reports/bundles/passive_ds_speed_limit_20260727/analysis/metrics.csv

anchor_fail | anchor_ok | anchor_range_count | anchor_range_rate_hz | anchor_success_pct | block | configured_frame_ms | duration_sec | effective_frame_ms | filtered_bias_2d_cm | filtered_bias_x_cm | filtered_bias_y_cm | filtered_max_error_cm | filtered_mean_x_m | filtered_mean_y_m | filtered_n | filtered_p95_error_cm | filtered_rmse_2d_cm | filtered_std_x_cm | filtered_std_y_cm | filtered_two_drms_cm | final_delay_us | gap_ms | independent_frame_accept | internal_rms_mean_cm | internal_rms_p95_cm | label | late_slot_delta | nominal_position_rate_hz | nominal_rate_achieved_pct | observation_accept | observation_count | observation_rate_hz | observation_reject | observed_slot_period_ms | observed_slot_rate_hz | position_count | position_rate_hz | range_accept | range_reject | raw_bias_2d_cm | raw_bias_x_cm | raw_bias_y_cm | raw_max_error_cm | raw_mean_x_m | raw_mean_y_m | raw_n | raw_p95_error_cm | raw_rmse_2d_cm | raw_std_x_cm | raw_std_y_cm | raw_two_drms_cm | relocation_count_last | resp_delay_us | rolling_accept | schedule | schedule_id | slot_ms | solver_accept | solver_accept_pct
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
