victorstoica114/UWB_Module_ESP_IDF/reports/bundles/ds_twr_speed_limit_20260726/figures/01_rate_completeness.png

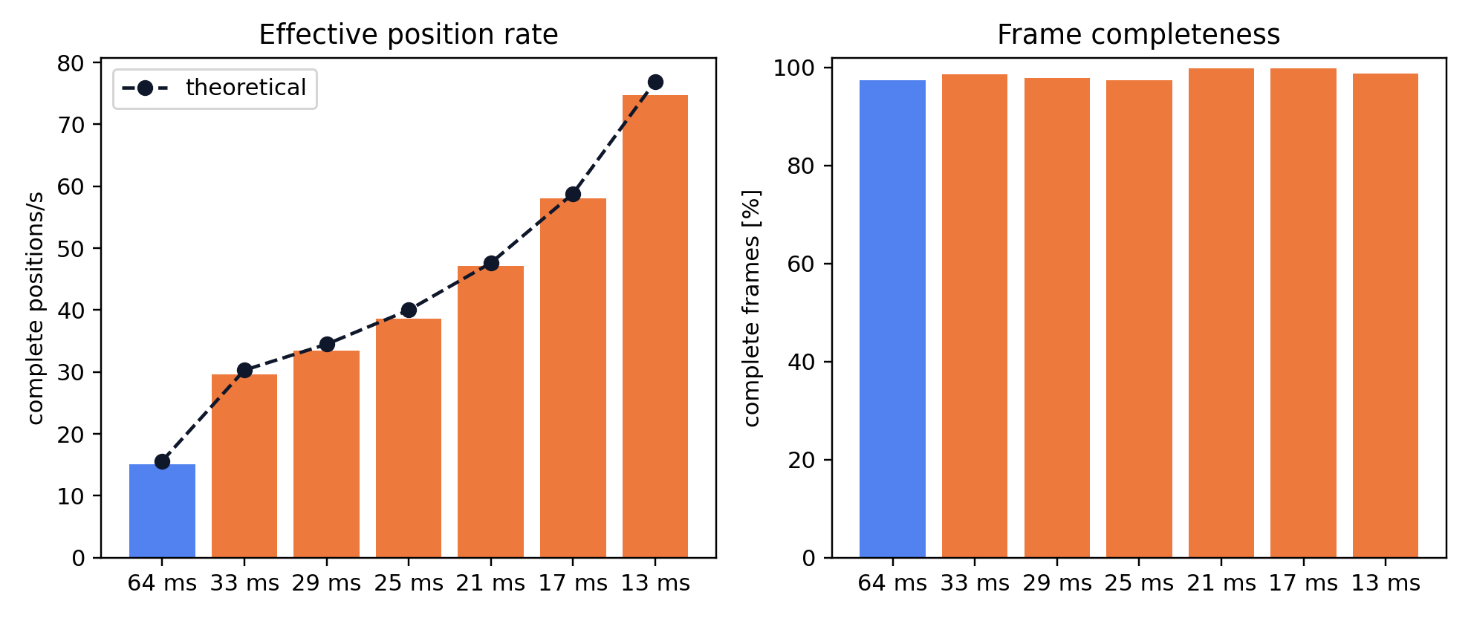
reports/bundles/ds_twr_speed_limit_20260726/figures/01_rate_completeness.png
