victorstoica114/UWB_Module_ESP_IDF/reports/bundles/ds_twr_speed_limit_20260726/figures/02_accuracy.png

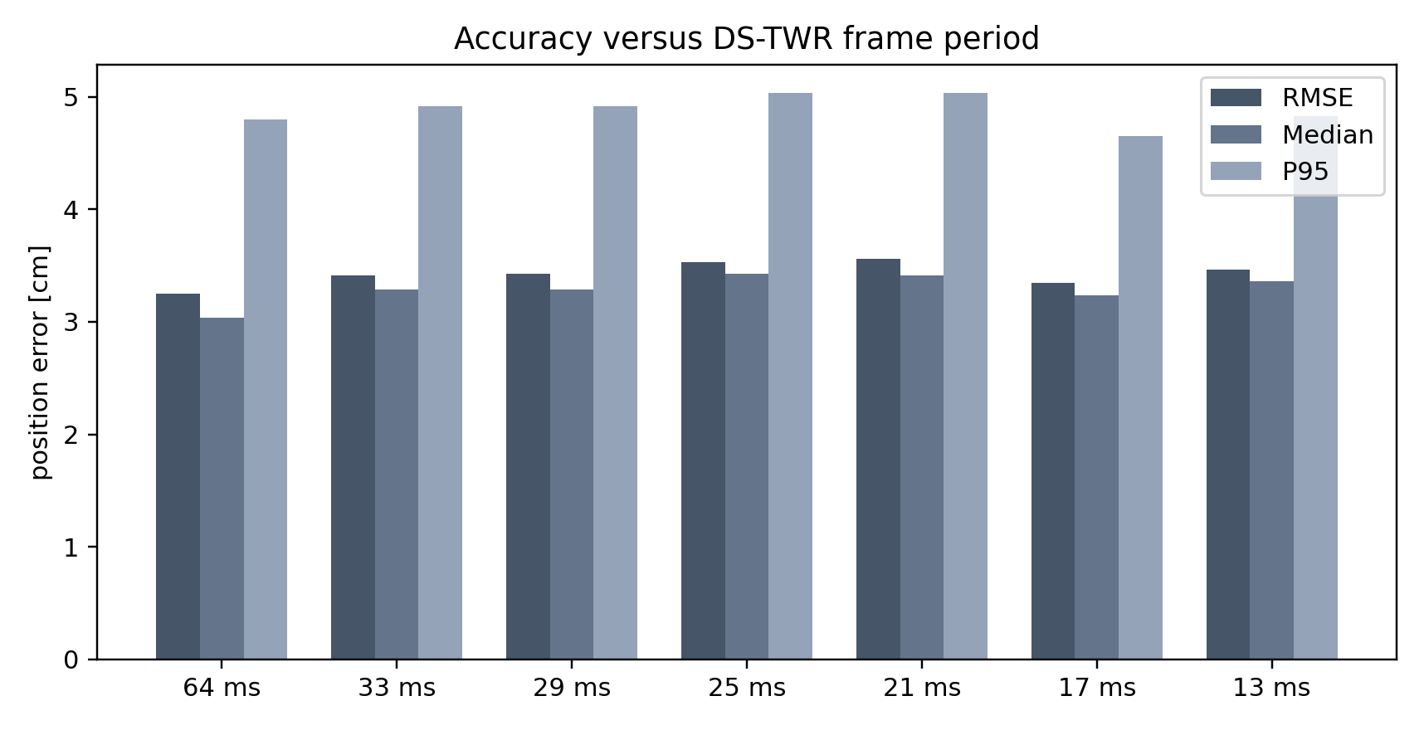
reports/bundles/ds_twr_speed_limit_20260726/figures/02_accuracy.png
