victorstoica114/UWB_Module_ESP_IDF/reports/bundles/native_ds_round_boundary_20260731/figures/01_valid_throughput.png

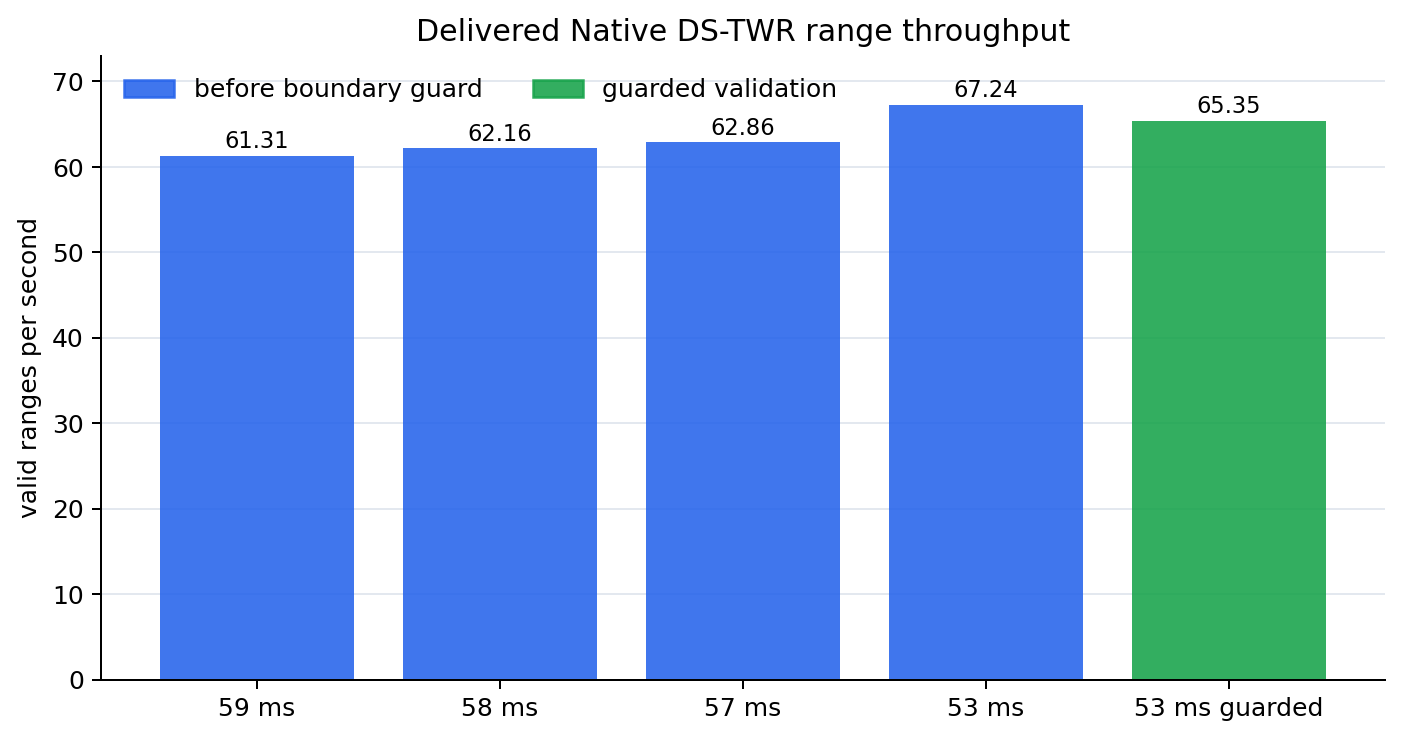
reports/bundles/native_ds_round_boundary_20260731/figures/01_valid_throughput.png
