victorstoica114/UWB_Module_ESP_IDF/reports/bundles/native_ds_round_boundary_20260731/figures/06_schedule_guard.png

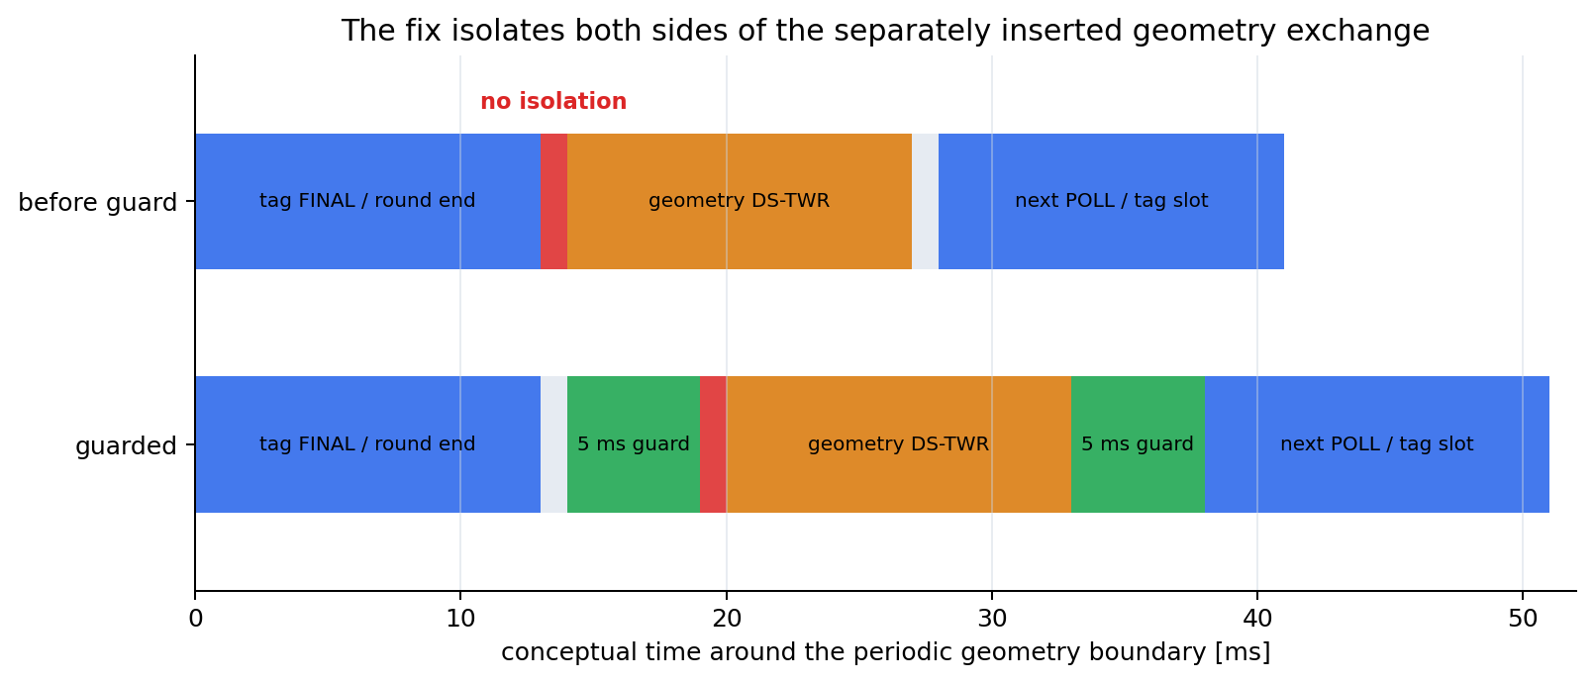
reports/bundles/native_ds_round_boundary_20260731/figures/06_schedule_guard.png
