victorstoica114/UWB_Module_ESP_IDF/reports/bundles/passive_ds_known_geometry_20260727/figures/position_error_cdf.png

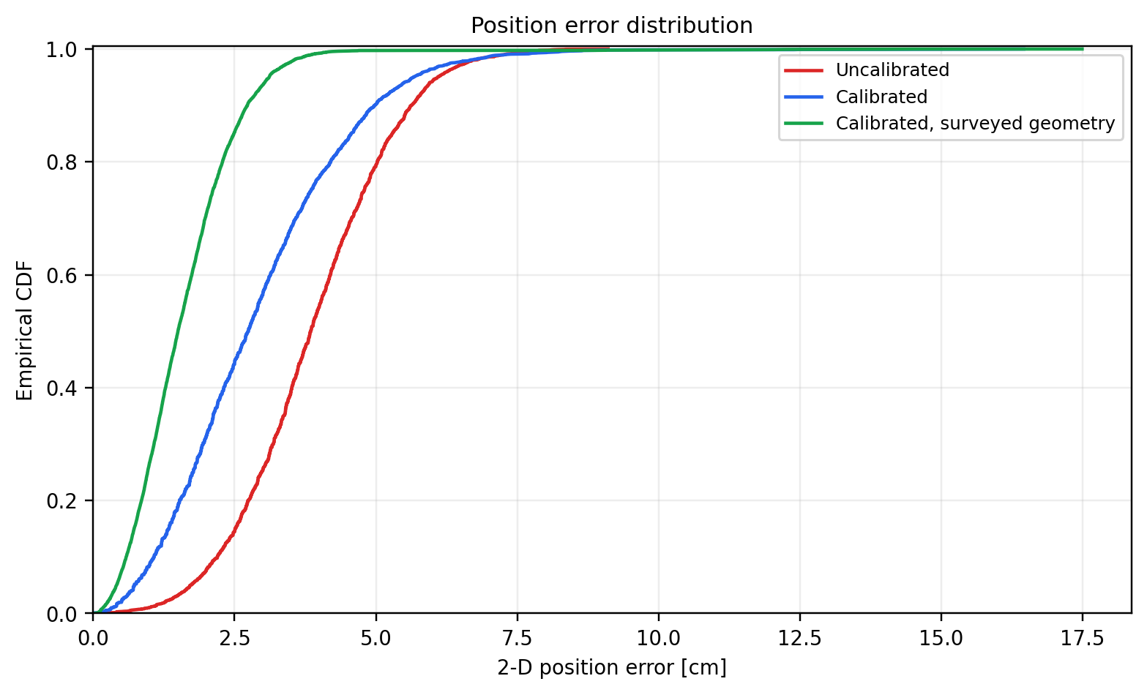
reports/bundles/passive_ds_known_geometry_20260727/figures/position_error_cdf.png
