victorstoica114/UWB_Module_ESP_IDF/reports/bundles/uwb_gps_rtk_comparison_20260803/figures/02_position_clouds.png

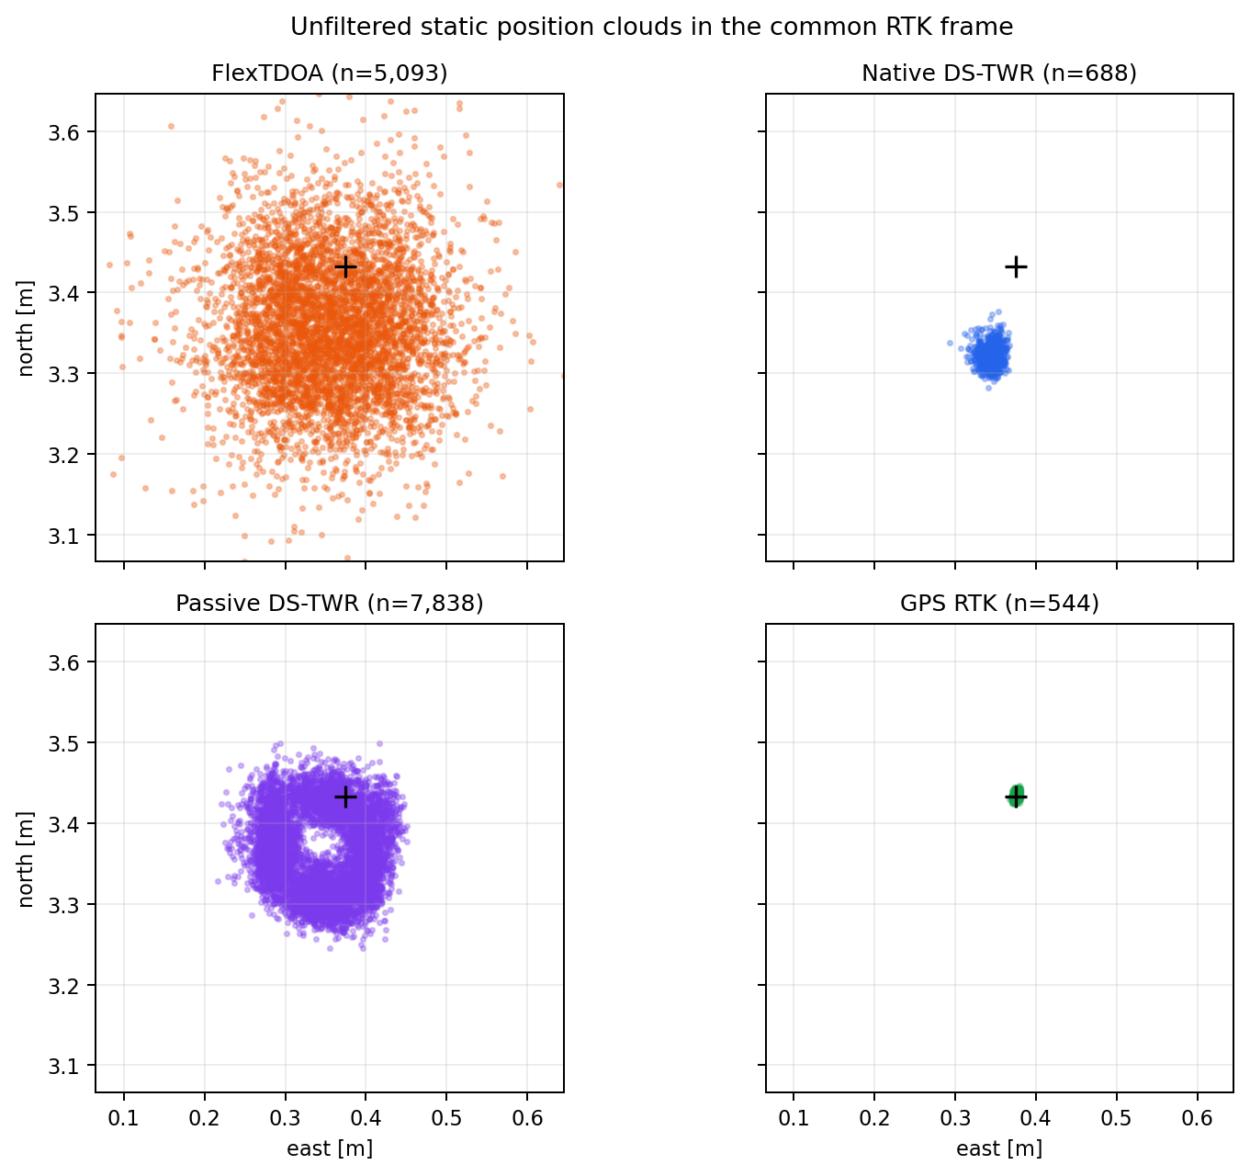
reports/bundles/uwb_gps_rtk_comparison_20260803/figures/02_position_clouds.png
