victorstoica114/UWB_Module_ESP_IDF/reports/bundles/uwb_protocol_comparison_20260726/figures/01_geometry.png

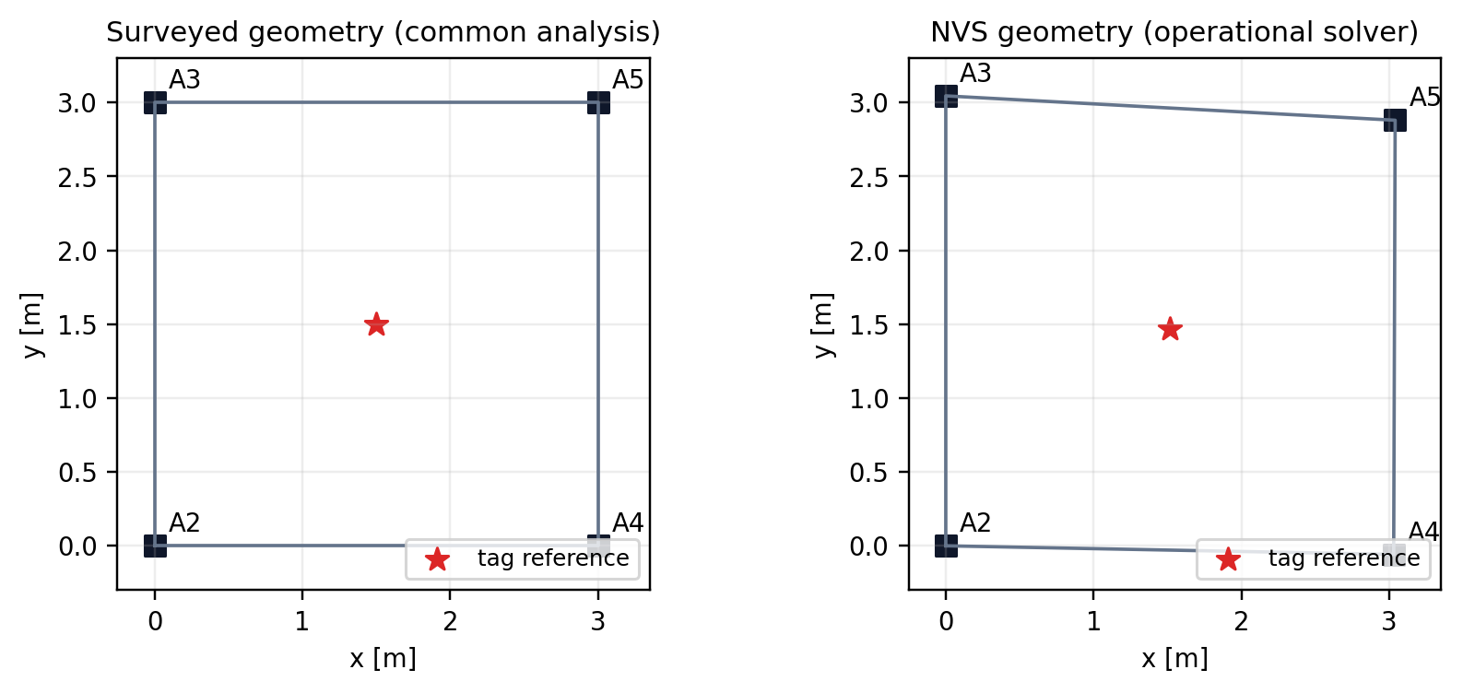
reports/bundles/uwb_protocol_comparison_20260726/figures/01_geometry.png
