victorstoica114/UWB_Module_ESP_IDF/reports/bundles/uwb_protocol_comparison_20260726/figures/08_block_repeatability.png

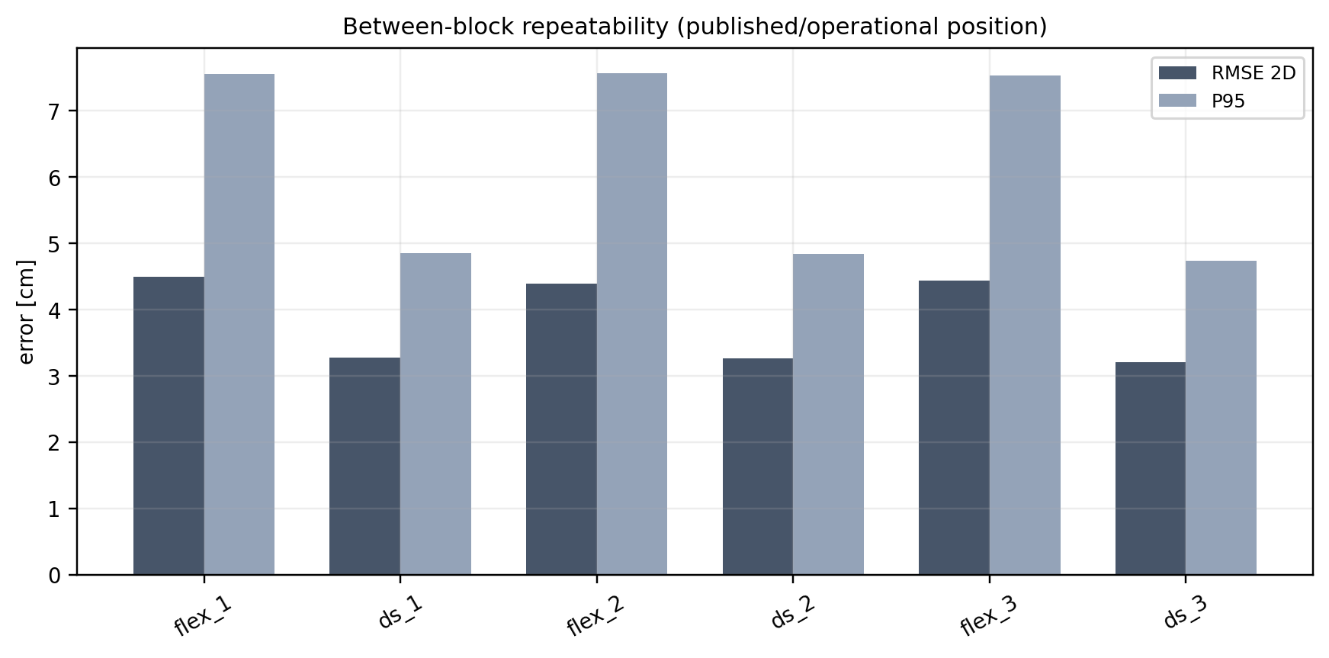
reports/bundles/uwb_protocol_comparison_20260726/figures/08_block_repeatability.png
