victorstoica114/UWB_Module_ESP_IDF/reports/bundles/uwb_protocol_comparison_20260726/figures/09_protocol_timing.png

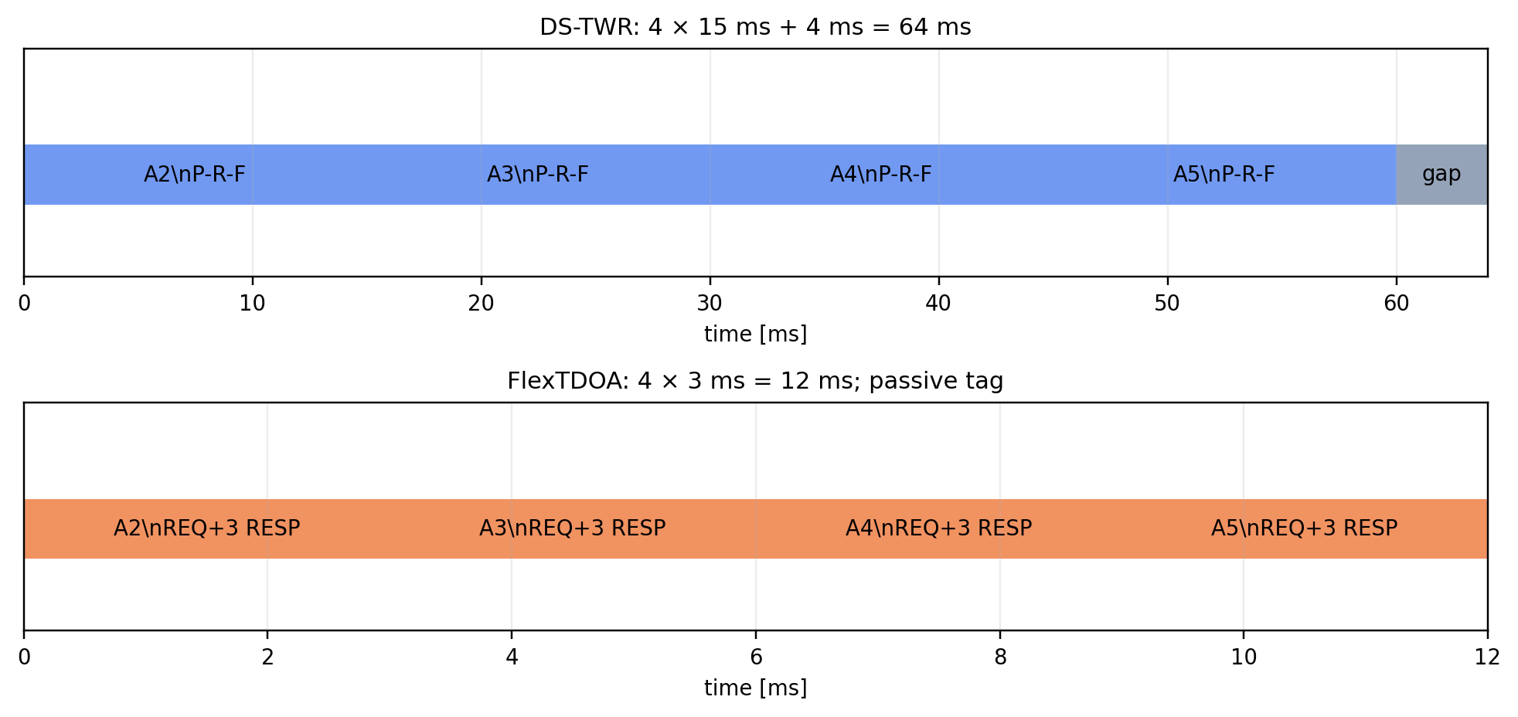
reports/bundles/uwb_protocol_comparison_20260726/figures/09_protocol_timing.png
