victorstoica114/UWB_Module_ESP_IDF/reports/bundles/imu_fusion_validation_20260811/analysis/replay_metrics.csv

summary_path | protocol | motion | input_files | position_samples | position_accepted | position_outliers | position_accept_pct | position_outlier_pct | position_corrections | ordering_rejects | reset_count | velocity_clamps | yaw_alignment_valid | yaw_alignment_updates | imu_samples | imu_invalid_samples | position_rate_hz | position_gap_p95_ms | position_gap_max_ms | position_gap_gt_threshold_count | imu_rate_hz | imu_gap_p95_ms | imu_gap_max_ms | imu_gap_gt_threshold_count | rtk_fixed_fixes | rtk_matches | anchor_fit_rms_m | anchor_count | all_anchor_geometry_rtk_fixed | maximum_anchor_time_delta_ms | rtk_interpretation_grade | raw_vs_rtk_count | raw_vs_rtk_rmse_m | raw_vs_rtk_p95_m | raw_vs_rtk_max_m | fused_vs_rtk_count | fused_vs_rtk_rmse_m | fused_vs_rtk_p95_m | fused_vs_rtk_max_m | fused_minus_raw_rmse_m | limitations
D:\Documente\UWB_ESP_IDF\.cache\imu_validation_inputs_20260811\replay_dynamic\flextdoa.summary.json | flextdoa | dynamic | ['D:\\Documente\\UWB_ESP_IDF\\reports\\imu_fusion_dynamic_20260810\\flextdoa_walk_imu_clean.flextdoa.jsonl'] | 4149 | 4141 | 14 | 99.80718245360328 | 0.3374307061942637 | 4134 | 0 | 0 | 0 | True | 4 | 14979 | 0 | 27.64043446391684 | 70.0 | 2030.0 | 57 | 99.81939407388559 | 11.953300000009767 | 30.398999999975786 | 0 | 100 | 98 | 0.008949049220098131 | 4 | True | 80.9971 | indicative_in_system_reference | 1425 | 0.43505772904096984 | 0.8816823500153933 | 2.0971705637129534 | 1425 | 0.43469582873023854 | 0.8816823500153933 | 2.0971705637129534 | -0.00036190031073130013 | ['RTK association compares dashboard telemetry receive time with GPS measurement time estimated from the reported fix age.', 'RTK-to-UWB alignment uses anchor geometry, never the tag trajectory.', 'Only RTK-fixed quality 4 fixes enter accuracy metrics.', 'RMSE/P95/P99 compare raw and fused states at identical UWB correction timestamps; fused_stream timing separately measures IMU dead-zone coverage.', 'RTK course initializes IMU-to-UWB yaw while moving; UWB straight-line motion can refine it and assumes body +X follows travel.']
D:\Documente\UWB_ESP_IDF\.cache\imu_validation_inputs_20260811\replay_dynamic\native_ds.summary.json | native_ds | dynamic | ['D:\\Documente\\UWB_ESP_IDF\\reports\\imu_fusion_dynamic_20260810\\native_ds_walk_imu_clean_take2.native_ds.jsonl'] | 3359 | 3237 | 165 | 96.36796665674308 | 4.912176242929443 | 3193 | 0 | 0 | 0 | True | 1 | 14937 | 0 | 22.389651953593813 | 60.0 | 410.0 | 2 | 99.58072687036771 | 11.805000000051223 | 26.79800000000978 | 0 | 92 | 92 | 0.0203359225166938 | 4 | True | 235.3696 | indicative_in_system_reference | 1024 | 0.47844595331882733 | 1.2038730063144507 | 2.1487993251671287 | 1024 | 0.4783776370092452 | 1.2038730063144507 | 2.1487993251671287 | -6.83163095821504e-05 | ['RTK association compares dashboard telemetry receive time with GPS measurement time estimated from the reported fix age.', 'RTK-to-UWB alignment uses anchor geometry, never the tag trajectory.', 'Only RTK-fixed quality 4 fixes enter accuracy metrics.', 'RMSE/P95/P99 compare raw and fused states at identical UWB correction timestamps; fused_stream timing separately measures IMU dead-zone coverage.', 'RTK course initializes IMU-to-UWB yaw while moving; UWB straight-line motion can refine it and assumes body +X follows travel.']
D:\Documente\UWB_ESP_IDF\.cache\imu_validation_inputs_20260811\replay_dynamic\passive_ds.summary.json | passive_ds | dynamic | ['D:\\Documente\\UWB_ESP_IDF\\reports\\imu_fusion_dynamic_20260810\\passive_ds_walk_imu_clean.passive_ds.jsonl'] | 3576 | 3494 | 129 | 97.7069351230425 | 3.6073825503355703 | 3446 | 0 | 0 | 0 | True | 3 | 14993 | 0 | 23.844460748349228 | 120.0 | 610.0 | 206 | 99.94759951092877 | 11.986000000004424 | 30.62000000000262 | 0 | 95 | 92 | 0.0017489316195153043 | 4 | True | 449.8713 | indicative_in_system_reference | 1142 | 0.4399504979055489 | 1.0515114570103958 | 2.598522650908144 | 1142 | 0.43965975341336216 | 1.0515114570103958 | 2.598522650908144 | -0.00029074449218674525 | ['RTK association compares dashboard telemetry receive time with GPS measurement time estimated from the reported fix age.', 'RTK-to-UWB alignment uses anchor geometry, never the tag trajectory.', 'Only RTK-fixed quality 4 fixes enter accuracy metrics.', 'RMSE/P95/P99 compare raw and fused states at identical UWB correction timestamps; fused_stream timing separately measures IMU dead-zone coverage.', 'RTK course initializes IMU-to-UWB yaw while moving; UWB straight-line motion can refine it and assumes body +X follows travel.']
D:\Documente\UWB_ESP_IDF\.cache\imu_validation_inputs_20260811\replay_static\flextdoa.summary.json | flextdoa | static | ['D:\\Documente\\UWB_ESP_IDF\\reports\\imu_fusion_static_20260811\\flextdoa_static_final.flextdoa.jsonl'] | 929 | 929 | 0 | 100.0 | 0.0 | 928 | 0 | 0 | 0 | False | 0 | 13198 | 0 | 30.820325473264695 | 60.0 | 140.0 | 1 | 448.6611559458737 | 6.861999999999523 | 24.550999999999476 | 0 | 164 | 0 |  | 0 | False |  | audit_only_invalid_for_cross_protocol_ranking | 0 |  |  |  | 0 |  |  |  |  | ['RTK association compares dashboard telemetry receive time with GPS measurement time estimated from the reported fix age.', 'RTK-to-UWB alignment uses anchor geometry, never the tag trajectory.', 'Only RTK-fixed quality 4 fixes enter accuracy metrics.', 'RMSE/P95/P99 compare raw and fused states at identical UWB correction timestamps; fused_stream timing separately measures IMU dead-zone coverage.', 'RTK course initializes IMU-to-UWB yaw while moving; UWB straight-line motion can refine it and assumes body +X follows travel.']
D:\Documente\UWB_ESP_IDF\.cache\imu_validation_inputs_20260811\replay_static\native_ds.summary.json | native_ds | static | ['D:\\Documente\\UWB_ESP_IDF\\reports\\imu_fusion_static_20260811\\native_ds_static_final.native_ds.jsonl'] | 686 | 684 | 2 | 99.70845481049562 | 0.2915451895043732 | 683 | 0 | 0 | 0 | False | 0 | 13476 | 0 | 22.562582345191043 | 50.0 | 70.0 | 0 | 452.03717808704914 | 5.942000000002736 | 25.133999999998196 | 0 | 129 | 129 | 1.0641885425260198 | 3 | True | 406.32906 | audit_only_invalid_for_cross_protocol_ranking | 369 | 2.9715567632579907 | 2.997700180977475 | 3.019792709170403 | 369 | 2.9740979253985227 | 2.985215110843289 | 3.0029863328854858 | 0.002541162140532016 | ['RTK association compares dashboard telemetry receive time with GPS measurement time estimated from the reported fix age.', 'RTK-to-UWB alignment uses anchor geometry, never the tag trajectory.', 'Only RTK-fixed quality 4 fixes enter accuracy metrics.', 'RMSE/P95/P99 compare raw and fused states at identical UWB correction timestamps; fused_stream timing separately measures IMU dead-zone coverage.', 'RTK course initializes IMU-to-UWB yaw while moving; UWB straight-line motion can refine it and assumes body +X follows travel.']
D:\Documente\UWB_ESP_IDF\.cache\imu_validation_inputs_20260811\replay_static\passive_ds.summary.json | passive_ds | static | ['D:\\Documente\\UWB_ESP_IDF\\reports\\imu_fusion_static_20260811\\passive_ds_static_final.passive_ds.jsonl'] | 772 | 772 | 0 | 100.0 | 0.0 | 771 | 2 | 0 | 0 | False | 0 | 13533 | 0 | 25.00810898475511 | 105.0 | 200.0 | 39 | 452.7281336443272 | 5.596799999964423 | 46.462999999988824 | 0 | 246 | 244 | 0.7153984694160029 | 3 | True | 84.5874 | audit_only_invalid_for_cross_protocol_ranking | 768 | 2.3691034140065863 | 2.395282772810467 | 2.429876155234365 | 768 | 2.3691034140065863 | 2.395282772810467 | 2.429876155234365 | 0.0 | ['RTK association compares dashboard telemetry receive time with GPS measurement time estimated from the reported fix age.', 'RTK-to-UWB alignment uses anchor geometry, never the tag trajectory.', 'Only RTK-fixed quality 4 fixes enter accuracy metrics.', 'RMSE/P95/P99 compare raw and fused states at identical UWB correction timestamps; fused_stream timing separately measures IMU dead-zone coverage.', 'RTK course initializes IMU-to-UWB yaw while moving; UWB straight-line motion can refine it and assumes body +X follows travel.']
