victorstoica114/UWB_Module_ESP_IDF/reports/bundles/imu_fusion_validation_20260811/analysis/rtk_alignment_metrics.csv

capture_id | protocol | motion | alignment_available | alignment_transformed_positions | alignment_transform_coverage_pct | alignment_exact_geometry_version_pct | alignment_geometry_match_age_p95_s | alignment_geometry_match_age_max_s | rtk_tag_total | rtk_tag_valid | rtk_tag_fixed | rtk_tag_fixed_pct | rtk_tag_fix_age_p95_ms | rtk_all_modules_fixed_pct | rtk_fixed_anchor_count | rtk_anchor_spread_p95_m_max | rtk_tag_center_east_m | rtk_tag_center_north_m | rtk_tag_center_up_m | error_pairs | error_fixed_tag_solutions | error_pair_coverage_pct | static_rtk_reference_consistent | static_rtk_max_cross_capture_center_distance_m | error_interpretation_grade | alignment_snapshot_count | alignment_dynamic_snapshot_count | alignment_rtk_derived_dynamic_geometry | alignment_anchor_count_min | alignment_fit_rmse_m_median | alignment_fit_rmse_m_p95 | alignment_fit_rmse_m_max | alignment_fit_residual_m_max | alignment_yaw_deg_median | alignment_yaw_deg_span | alignment_anchor_spread_p95_m_max | alignment_quality_flag | error_association_abs_p50_ms | error_association_abs_p95_ms | error_association_abs_max_ms | error_bias_east_mean_m | error_bias_north_mean_m | error_bias_east_median_m | error_bias_north_median_m | error_error_median_m | error_error_rmse_m | error_error_p95_m | error_error_max_m | error_error_gt_0_5m | error_error_gt_1m | error_error_gt_2m | error_debiased_error_rmse_m | error_debiased_error_p95_m | error_debiased_error_max_m
flextdoa_static_final | flextdoa | static | False | 0 | 0.0 |  |  |  | 242 | 242 | 164 | 67.76859504132231 |  | 31.117021276595743 | 2 | 0.011469567549409096 | 0.24117278193556002 | -0.21935120768730368 | 1.0799999911832667 | 0 | 164 | 0.0 | False | 2.0324787288378476 | audit_only_invalid_for_cross_protocol_ranking
flextdoa_walk_imu_clean | flextdoa | dynamic | True | 4149 | 100.0 | 6.049650518197156 | 0.29666810035705554 | 0.84765625 | 100 | 100 | 100 | 100.0 | 100.0 | 100.0 | 4 | 0.012269802740247998 | -0.7757563297931991 | 0.0433369023732785 | -0.050000048127168184 | 98 | 100 | 98.0 |  |  |  | 253 | 252 | True | 4 | 0.009404653677116206 | 0.01283057336260731 | 0.017109111220276904 | 0.024993643199216337 | 0.11211851478123336 | 0.14832025026015108 | 0.012269802740247998 | usable_with_limitations | 9.724617004394531 | 36.09894514083864 | 87.75711059570312 | 0.03101204833771322 | 0.06619403438453764 | 0.11196327479869761 | 0.1457024581739731 | 0.23479362581676236 | 0.4365680672133572 | 0.8299267462339225 | 1.5862319774307174 | 21 | 2 | 0 | 0.445110065600883 | 0.8569042910191328 | 1.5392214060585503
native_ds_static_final | native_ds | static | True | 686 | 100.0 | 100.0 | 0.6689092516899109 | 0.7488119602203369 | 244 | 244 | 129 | 52.868852459016395 |  | 50.205086136177194 | 3 | 0.04200416297916751 | -0.7444935354206262 | 1.5581278200392705 | 4.311999763004749 | 129 | 129 | 100.0 | False | 2.0324787288378476 | audit_only_invalid_for_cross_protocol_ranking | 23 | 0 | False | 3 | 1.0733018427114682 | 1.0733018427114682 | 1.0733018427114682 | 1.325510118906103 | 3.664472996016604 | 0.0 | 0.04200416297916751 | poor_alignment_do_not_claim_accuracy | 7.836818695068359 | 23.04120063781738 | 38.546085357666016 | 0.6380421861259048 | -2.9096357285111365 | 0.6364061446513715 | -2.9136174694510157 | 2.9824509784009043 | 2.9788735172971452 | 3.0015971443834237 | 3.0220173809490007 | 129 | 129 | 129 | 0.02506110616131944 | 0.05225638491004643 | 0.0855920005946951
native_ds_walk_imu_clean_take2 | native_ds | dynamic | True | 3359 | 100.0 | 8.96100029770765 | 0.2586191654205322 | 0.38896894454956055 | 100 | 100 | 92 | 92.0 | 100.0 | 98.40319361277444 | 4 | 0.015767504312999062 | -0.7853266782070796 | -0.004444760482977067 | -0.07500004873741768 | 91 | 92 | 98.91304347826087 |  |  |  | 277 | 276 | True | 4 | 0.010162818615737512 | 0.015055635292829992 | 0.024316435798290816 | 0.038904091434435066 | 0.04785657902368603 | 0.20416845882384566 | 0.015767504312999062 | usable_with_limitations | 11.458396911621094 | 28.42104434967041 | 34.081220626831055 | 0.08471578514756567 | -0.012855861808243033 | 0.11644572953447074 | -0.02913428579379685 | 0.12845362910750732 | 0.47068845669880405 | 1.1802623176044258 | 1.5896266480328127 | 17 | 9 | 0 | 0.4641953923637656 | 1.1365968675558331 | 1.651817706338804
passive_ds_static_final | passive_ds | static | True | 772 | 100.0 | 100.0 | 29.46137387752533 | 30.85590672492981 | 248 | 248 | 246 | 99.19354838709677 |  | 50.88566827697262 | 3 | 0.01525142033528854 | -0.5039585519412342 | 0.3672521691006713 | 1.0254999677765442 | 244 | 246 | 99.1869918699187 | False | 2.0324787288378476 | audit_only_invalid_for_cross_protocol_ranking | 1 | 0 | False | 3 | 0.7405768799447429 | 0.7405768799447429 | 0.7405768799447429 | 0.94923777292422 | 5.674012569276456 | 0.0 | 0.01525142033528854 | poor_alignment_do_not_claim_accuracy | 3.849625587463379 | 42.93302297592163 | 85.68930625915527 | 1.2301871725650544 | -1.459765509955376 | 1.2292434028552879 | -1.4573876319461172 | 1.9093253402468813 | 1.9091028764114384 | 1.9326328618751376 | 1.9715508134547213 | 244 | 244 | 0 | 0.02011253660376842 | 0.03359989827670736 | 0.06862484467152541
passive_ds_walk_imu_clean | passive_ds | dynamic | True | 3576 | 100.0 | 17.729306487695748 | 0.28890514373779297 | 0.6377954483032227 | 101 | 99 | 95 | 94.05940594059406 | 120.0 | 89.38775510204081 | 4 | 0.011766361059716197 | -0.7853266806060174 | 0.026669197231125978 | -0.060000047584451766 | 90 | 95 | 94.73684210526316 |  |  |  | 257 | 256 | True | 4 | 0.009160252814101606 | 0.013373086208988912 | 0.016838215907459094 | 0.02349661558263597 | 0.08484784900195312 | 0.1502654922823942 | 0.011766361059716197 | usable_with_limitations | 11.851668357849121 | 47.68184423446654 | 95.41535377502441 | 0.04181927406105343 | 0.08047337277989175 | 0.034179434996679636 | 0.06624250241265783 | 0.1572644651714493 | 0.46366251611413895 | 0.9915247882489907 | 2.0058510154862907 | 16 | 4 | 1 | 0.45499340462480087 | 0.9649165059413619 | 2.0454190770169767
