victorstoica114/UWB_Module_ESP_IDF/reports/bundles/imu_fusion_validation_20260811/analysis/capture_metrics.csv

capture_id | protocol | motion | duration_s | imu_fused_position_records_excluded | position_events | position_event_rate_hz | position_active_event_rate_hz | position_unique_uptime_events | position_unique_uptime_rate_hz | position_active_unique_uptime_rate_hz | position_uptime_span_s | position_wall_span_s | position_wall_coverage_pct | position_first_event_after_capture_start_s | position_last_event_before_capture_end_s | position_duplicate_uptime_pct | position_gap_p50_ms | position_gap_p95_ms | position_gap_p99_ms | position_gap_max_ms | position_gaps_gt_30ms | position_gaps_gt_50ms | position_gaps_gt_100ms | position_independent_events | position_independent_rate_hz | position_independent_pct | position_sigma_median_m | position_sigma_p95_m | position_rms_median_m | position_rms_p95_m | position_batch_age_p95_ms | imu_events | imu_event_rate_hz | imu_active_event_rate_hz | imu_unique_uptime_events | imu_unique_uptime_rate_hz | imu_active_unique_uptime_rate_hz | imu_uptime_span_s | imu_wall_span_s | imu_wall_coverage_pct | imu_first_event_after_capture_start_s | imu_last_event_before_capture_end_s | imu_duplicate_uptime_pct | imu_gap_p50_ms | imu_gap_p95_ms | imu_gap_p99_ms |
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
