victorstoica114/UWB_Module_ESP_IDF/reports/bundles/imu_fusion_validation_20260811/analysis/raw_data_manifest.csv

capture_id | protocol | motion | source_file | source_bytes | source_sha256 | archive_file | archive_bytes | archive_sha256 | compression | roundtrip_sha256_matches
flextdoa_walk_imu_clean | flextdoa | dynamic | .cache/imu_validation_inputs_20260811/flextdoa_walk_imu_clean.flextdoa.jsonl | 106865199 | e51ff16c30082f5acb937f259880117c947b283b5cb66db03e485282389b711c | data/flextdoa_walk_imu_clean.flextdoa.jsonl.xz | 5049412 | fa81c8e42580de9be7c8ef558c8bcf400c7eb7745946ef874c114c64acf7dd2d | XZ/LZMA2 preset 3 (lossless) | True
native_ds_walk_imu_clean_take2 | native_ds | dynamic | .cache/imu_validation_inputs_20260811/native_ds_walk_imu_clean_take2.native_ds.jsonl | 94719741 | 24d0265973cb76905daaf64fa970f6dd18c93ceefef1e6c17079e7f596a06d4f | data/native_ds_walk_imu_clean_take2.native_ds.jsonl.xz | 3839300 | 1487dde576598767f944d47cba45b082748ec1d3e5a9331abfbd511709545815 | XZ/LZMA2 preset 3 (lossless) | True
passive_ds_walk_imu_clean | passive_ds | dynamic | .cache/imu_validation_inputs_20260811/passive_ds_walk_imu_clean.passive_ds.jsonl | 130840197 | 46d1a98449dbc967d210584cb544369f24ffca7f93169cb7344da4df373010d9 | data/passive_ds_walk_imu_clean.passive_ds.jsonl.xz | 5647604 | de6b50ac8663682756e254ae2e16f6f9cd7aca5774b004b9472d69aad20449dd | XZ/LZMA2 preset 3 (lossless) | True
flextdoa_static_final | flextdoa | static | .cache/imu_validation_inputs_20260811/flextdoa_static_final.flextdoa.jsonl | 113112326 | 7e814842dffac507f9777541fd547ab440ad899efbe820cdeed1ceca9ee914c9 | data/flextdoa_static_final.flextdoa.jsonl.xz | 3932000 | f70fa6edb8b646e3deb9ca57a5e56c70a31936803c249fa81c29c1bff900542c | XZ/LZMA2 preset 3 (lossless) | True
native_ds_static_final | native_ds | static | .cache/imu_validation_inputs_20260811/native_ds_static_final.native_ds.jsonl | 112312663 | 968d87a3cae8c59ba20977b49928fd2613db4d1e0f083e1544666dae50f92871 | data/native_ds_static_final.native_ds.jsonl.xz | 3526696 | 180ded147bc64f3c8a33eb690e1dee116d05015b65b4b4e5242799ce9f227866 | XZ/LZMA2 preset 3 (lossless) | True
passive_ds_static_final | passive_ds | static | .cache/imu_validation_inputs_20260811/passive_ds_static_final.passive_ds.jsonl | 122477187 | 709db38970fddd078cc0980e8cb2300378431d82e443de938c766655a52c7f2a | data/passive_ds_static_final.passive_ds.jsonl.xz | 3952532 | bc95077aa777431e9368c75f2210cfffedb4538f540b251b64cff1c0b995892f | XZ/LZMA2 preset 3 (lossless) | True
