victorstoica114/UWB_Module_ESP_IDF/reports/bundles/native_ds_speed_revalidation_20260731/README.md

# `native_ds_speed_revalidation_20260731` bundle

Final report: [`../../native_ds_speed_revalidation_20260731.pdf`](../../native_ds_speed_revalidation_20260731.pdf)

- `source/`: report sources and decision notes;
- `analysis/`: profile/candidate results, metrics and historical metadata;
- `figures/`: retained PNG figures;
- `raw/`: decisive retained validation captures and metadata.

RAW integrity is covered by [`../RAW_SHA256SUMS`](../RAW_SHA256SUMS).
