victorstoica114/UWB_Module_ESP_IDF/reports/bundles/native_ds_speed_revalidation_20260731/analysis/candidate_58ms_validation/range_metrics.csv

anchor_id | samples | rate_hz | mean_m | median_m | std_cm | robust_sigma_cm | min_m | max_m | peak_to_peak_cm | reference_distance_m | reference_bias_cm | reference_rmse_cm | reference_p95_abs_cm
2 | 2785 | 15.46992694094947 | 2.224940754039497 | 2.23 | 21.12997894332066 | 1.0378200000000175 | -5.875 | 2.267 | 814.1999999999999 | 2.145821360808024 | 7.9119393231473225 | 22.559132949927534 | 10.3178639191976
3 | 2883 | 16.01391943452448 | 2.206976066597295 | 2.208 | 1.0255570896779982 | 1.0378200000000175 | 2.17 | 2.24 | 7.000000000000028 | 2.2036431908319463 | 0.33328757653482516 | 1.078185112067699 | 2.0356809168053935
4 | 2883 | 16.01412129063755 | 2.203392646548734 | 2.203 | 1.4536268314043346 | 1.4826000000000343 | 2.155 | 2.243 | 8.800000000000008 | 2.118321933158414 | 8.507071339031999 | 8.63032796621991 | 10.867806684158587
5 | 2882 | 16.01381176651259 | 2.2154854267869535 | 2.215 | 1.674808643221492 | 1.630860000000018 | 2.161 | 2.291 | 12.99999999999999 | 2.2206722658915705 | -0.5186839104616985 | 1.753009901139519 | 3.4672265891570575
