victorstoica114/UWB_Module_ESP_IDF/reports/bundles/native_ds_speed_revalidation_20260731/analysis/candidate_59ms_validation/range_metrics.csv

anchor_id | samples | rate_hz | mean_m | median_m | std_cm | robust_sigma_cm | min_m | max_m | peak_to_peak_cm | reference_distance_m | reference_bias_cm | reference_rmse_cm | reference_p95_abs_cm
2 | 2795 | 15.52645191834347 | 2.2272805008944543 | 2.23 | 14.285541655255244 | 1.0378200000000175 | -5.301 | 2.276 | 757.7 | 2.145821360808024 | 8.145914008643032 | 16.44261537896581 | 10.217863919197612
3 | 2836 | 15.76133059607453 | 2.2075909732016927 | 2.207 | 1.2110914938180606 | 1.186080000000001 | 2.173 | 2.247 | 7.399999999999984 | 2.2036431908319463 | 0.3947782369746285 | 1.2736071904989004 | 2.435680916805394
4 | 2837 | 15.759669961062482 | 2.195998237574903 | 2.196 | 1.215927721045265 | 1.186080000000001 | 2.159 | 2.241 | 8.20000000000003 | 2.118321933158414 | 7.767630441648908 | 7.86219064629618 | 9.76780668415862
5 | 2836 | 15.754108027988284 | 2.2187066290550073 | 2.219 | 1.7609660601962764 | 1.630859999999952 | 2.136 | 2.288 | 15.199999999999969 | 2.2206722658915705 | -0.1965636836563442 | 1.7715940011504505 | 3.5672265891570465
