victorstoica114/UWB_Module_ESP_IDF/reports/bundles/native_ds_speed_revalidation_20260731/analysis/candidate_60ms_validation/range_metrics.csv

anchor_id | samples | rate_hz | mean_m | median_m | std_cm | robust_sigma_cm | min_m | max_m | peak_to_peak_cm | reference_distance_m | reference_bias_cm | reference_rmse_cm | reference_p95_abs_cm
2 | 2777 | 15.422624630574804 | 2.227094346416997 | 2.227 | 1.1895033249562361 | 1.186080000000001 | 2.162 | 2.28 | 11.799999999999988 | 2.145821360808024 | 8.127298560897268 | 8.213853574592346 | 10.117863919197578
3 | 2794 | 15.517650199429179 | 2.2038593414459555 | 2.204 | 1.1240363198601286 | 1.186080000000001 | 2.166 | 2.235 | 6.899999999999995 | 2.2036431908319463 | 0.02161506140093738 | 1.1240429953348456 | 2.1643190831946324
4 | 2794 | 15.517464141211464 | 2.1956338582677164 | 2.196 | 1.2269535844882775 | 1.186080000000001 | 2.155 | 2.236 | 8.10000000000004 | 2.118321933158414 | 7.7311925109302555 | 7.827912489081988 | 9.667806684158586
5 | 2793 | 15.512111213173446 | 2.215784819190834 | 2.215 | 1.7852865664661064 | 1.7791200000000014 | 2.152 | 2.28 | 12.799999999999967 | 2.2206722658915705 | -0.48874467007362626 | 1.850669695309962 | 3.5672265891570465
