victorstoica114/UWB_Module_ESP_IDF/reports/bundles/native_ds_speed_revalidation_20260731/analysis/profile_29ms_validation/range_metrics.csv

anchor_id | samples | rate_hz | mean_m | median_m | std_cm | robust_sigma_cm | min_m | max_m | peak_to_peak_cm | reference_distance_m | reference_bias_cm | reference_rmse_cm | reference_p95_abs_cm
2 | 4852 | 26.949086665801193 | 2.2008021434460017 | 2.228 | 65.68375584900643 | 1.3343399999999845 | -22.831 | 2.28 | 2511.1 | 2.145821360808024 | 5.498078263797757 | 65.9067178352119 | 10.917863919197579
3 | 5296 | 29.425471994419752 | 2.211384063444109 | 2.21 | 1.1002539109085945 | 1.0378200000000175 | 2.176 | 2.253 | 7.699999999999996 | 2.2036431908319463 | 0.7740872612162527 | 1.3451918735399553 | 2.735680916805361
4 | 5626 | 31.250426919730227 | 2.2010636331318874 | 2.2 | 1.3146133994203846 | 1.3343399999999845 | 2.161 | 2.249 | 8.800000000000008 | 2.118321933158414 | 8.27416999734737 | 8.377934730737767 | 10.467806684158587
5 | 5674 | 31.514758943476913 | 2.2196986253084243 | 2.219 | 1.7815735509455917 | 1.7791200000000014 | 2.152 | 2.277 | 12.5 | 2.2206722658915705 | -0.0973640583146095 | 1.784075301884339 | 3.3672265891570685
