victorstoica114/UWB_Module_ESP_IDF/reports/bundles/imu_fusion_validation_20260811/analysis/alignment_snapshots.csv

capture_id | protocol | motion | alignment_index | geometry_time | snapshot_time | geometry_version | dynamic | all_rtk_fixed | source_geometry_fit_rms_m | anchor_ids | yaw_deg | translation_east_m | translation_north_m | fit_rmse_m | fit_p95_m | fit_max_m
flextdoa_walk_imu_clean | flextdoa | dynamic | 0 | 1786384960.3145268 | 1786384960.3145268 | 99 | False | False |  | 2,3,4,5 | 0.09666214828079452 | -1.660340639407516 | -4.587846636217322 | 0.017109111220276904 | 0.02420178544504748 | 0.024993643199216337
flextdoa_walk_imu_clean | flextdoa | dynamic | 1 | 1786384960.4984183 | 1786384960.5740058 | 2147498187 | True | True | 0.023 | 2,3,4,5 | 0.11211851478123336 | -1.655079646572862 | -4.582536937651067 | 0.0068015710622510925 | 0.009824130367102172 | 0.010419094227280688
flextdoa_walk_imu_clean | flextdoa | dynamic | 2 | 1786384961.0366905 | 1786384961.1097999 | 2147498255 | True | True | 0.023 | 2,3,4,5 | 0.1274692319096952 | -1.6498118911705573 | -4.585473387692267 | 0.009495596247416242 | 0.010457950433687966 | 0.01048386171709977
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
