victorstoica114/UWB_Module_ESP_IDF/reports/bundles/imu_fusion_validation_20260811/analysis/rtk_pairs.csv

capture_id | protocol | motion | gps_time | uwb_time | delta_ms | uwb_east_m | uwb_north_m | rtk_east_m | rtk_north_m | error_east_m | error_north_m | error_m | gps_fix_age_ms | gps_speed_mps | position_sigma_m | position_rms_m | geometry_version | alignment_version | alignment_exact_version | alignment_age_s | debiased_error_m
flextdoa_walk_imu_clean | flextdoa | dynamic | 1786384960.552998 | 1786384960.549349 | -3.648996353149414 | -1.2623675598362516 | 0.16424062369841952 | -1.3172784150378392 | 0.09111865173874316 | 0.05491085520158756 | 0.07312197195967636 | 0.09144410753154854 | 20.0 | 0.05 | 0.137 | 0.137 | 2147498195 | 2147498187 | False | 0.05093073844909668 | 0.09231958384323678
flextdoa_walk_imu_clean | flextdoa | dynamic | 1786384961.6425967 | 1786384961.6280859 | -14.510869979858398 | -1.2922932052756388 | 0.1264403031929362 | -1.3116957157299107 | 0.08889624857885838 | 0.019402510454271882 | 0.037544054614077824 | 0.04226125233346721 | 20.0 | 0.0 | 0.202 | 0.202 | 2147498331 | 2147498327 | False | 0.02813243865966797 | 0.1423577723787833
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
