victorstoica114/UWB_Module_ESP_IDF/reports/bundles/native_ds_speed_revalidation_20260731/figures/01_rate_delivery.png

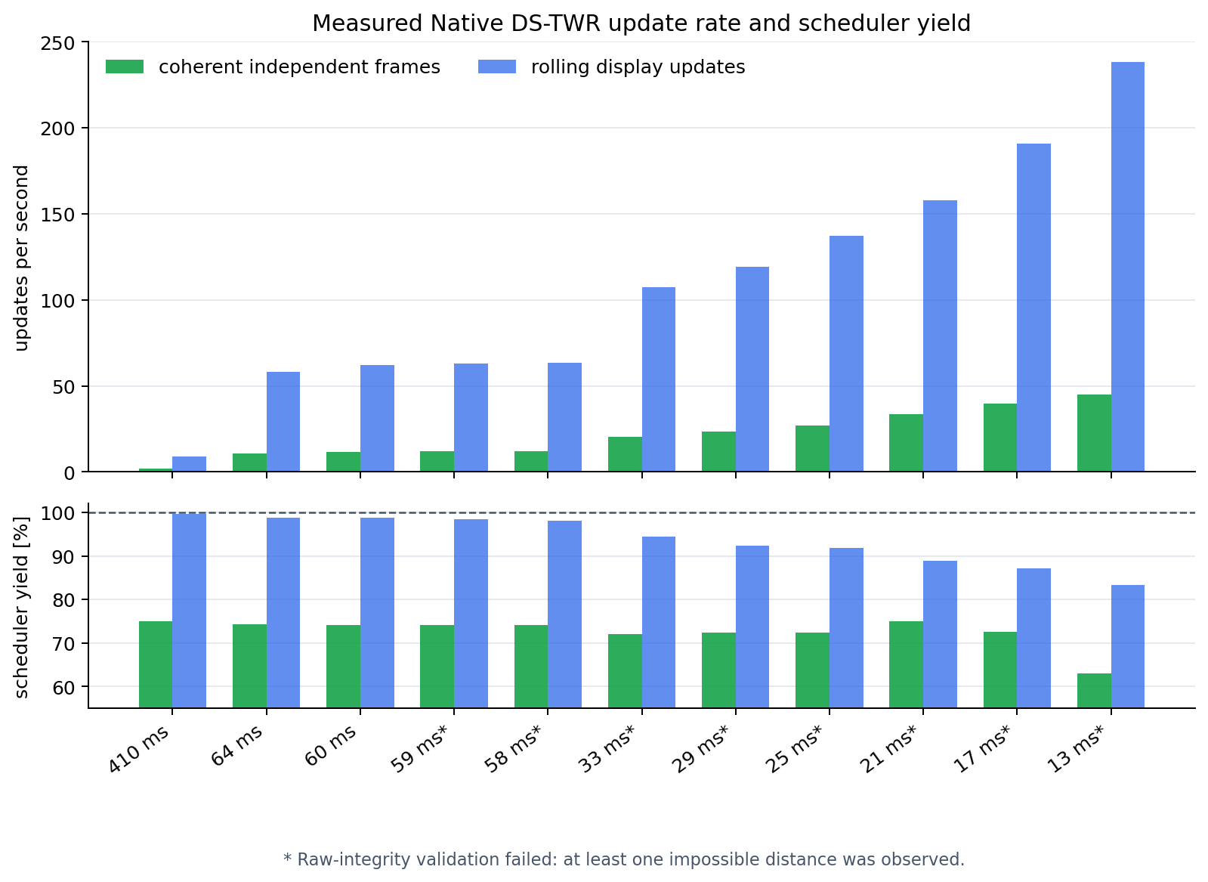
reports/bundles/native_ds_speed_revalidation_20260731/figures/01_rate_delivery.png
