victorstoica114/UWB_Module_ESP_IDF/reports/bundles/native_ds_speed_revalidation_20260731/figures/02_central_precision.png

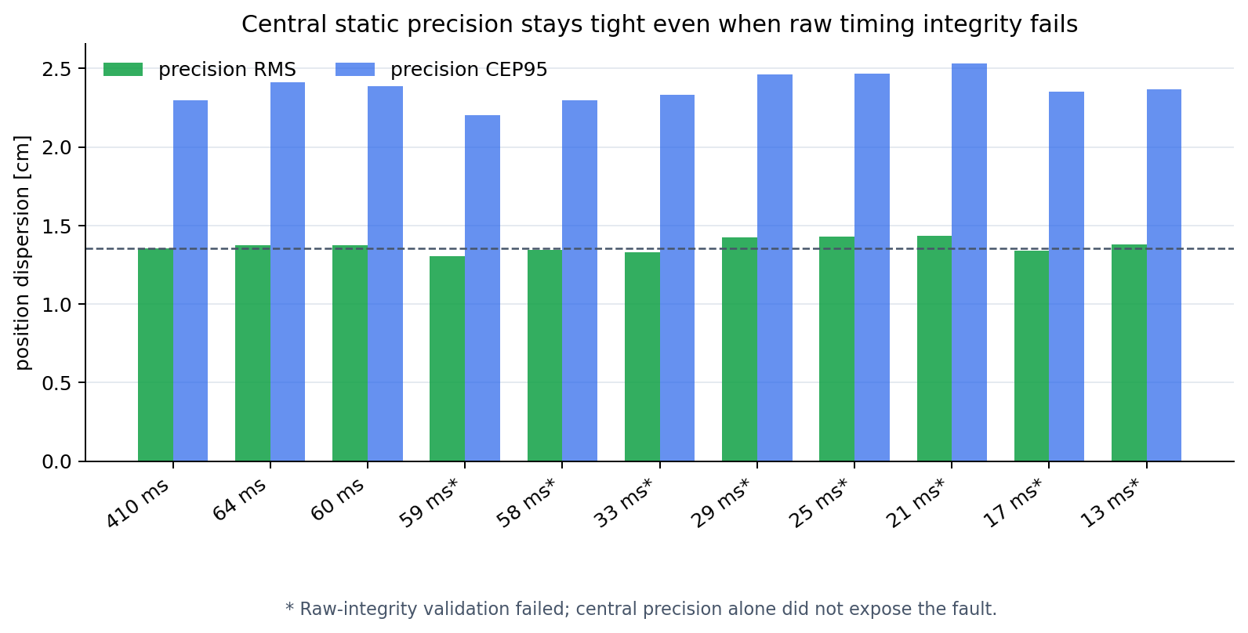
reports/bundles/native_ds_speed_revalidation_20260731/figures/02_central_precision.png
