victorstoica114/UWB_Module_ESP_IDF/reports/bundles/native_ds_speed_revalidation_20260731/figures/05_precision_cdf.png

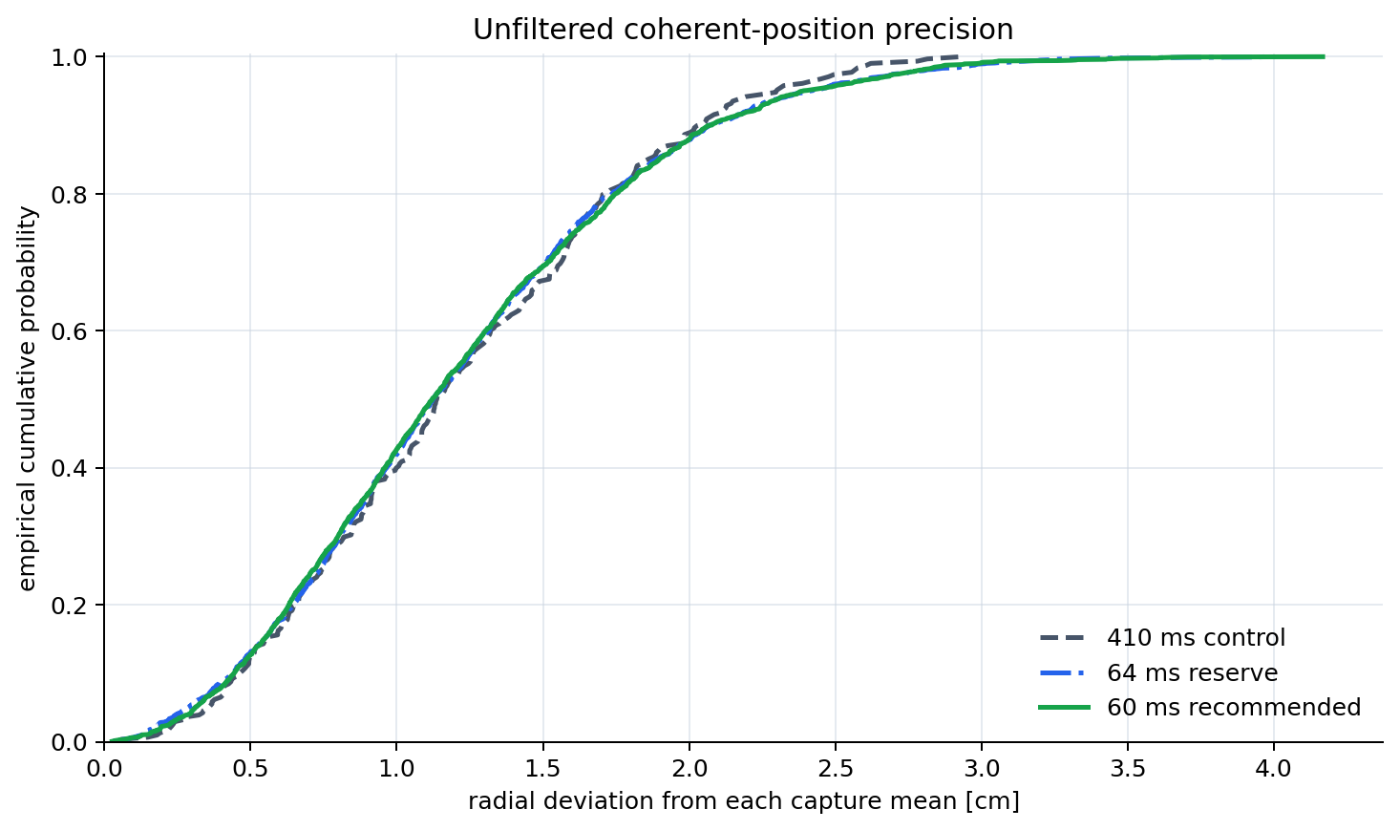
reports/bundles/native_ds_speed_revalidation_20260731/figures/05_precision_cdf.png
