victorstoica114/UWB_Module_ESP_IDF/Schematic/UWB_V1.0_Rev.B.pdf

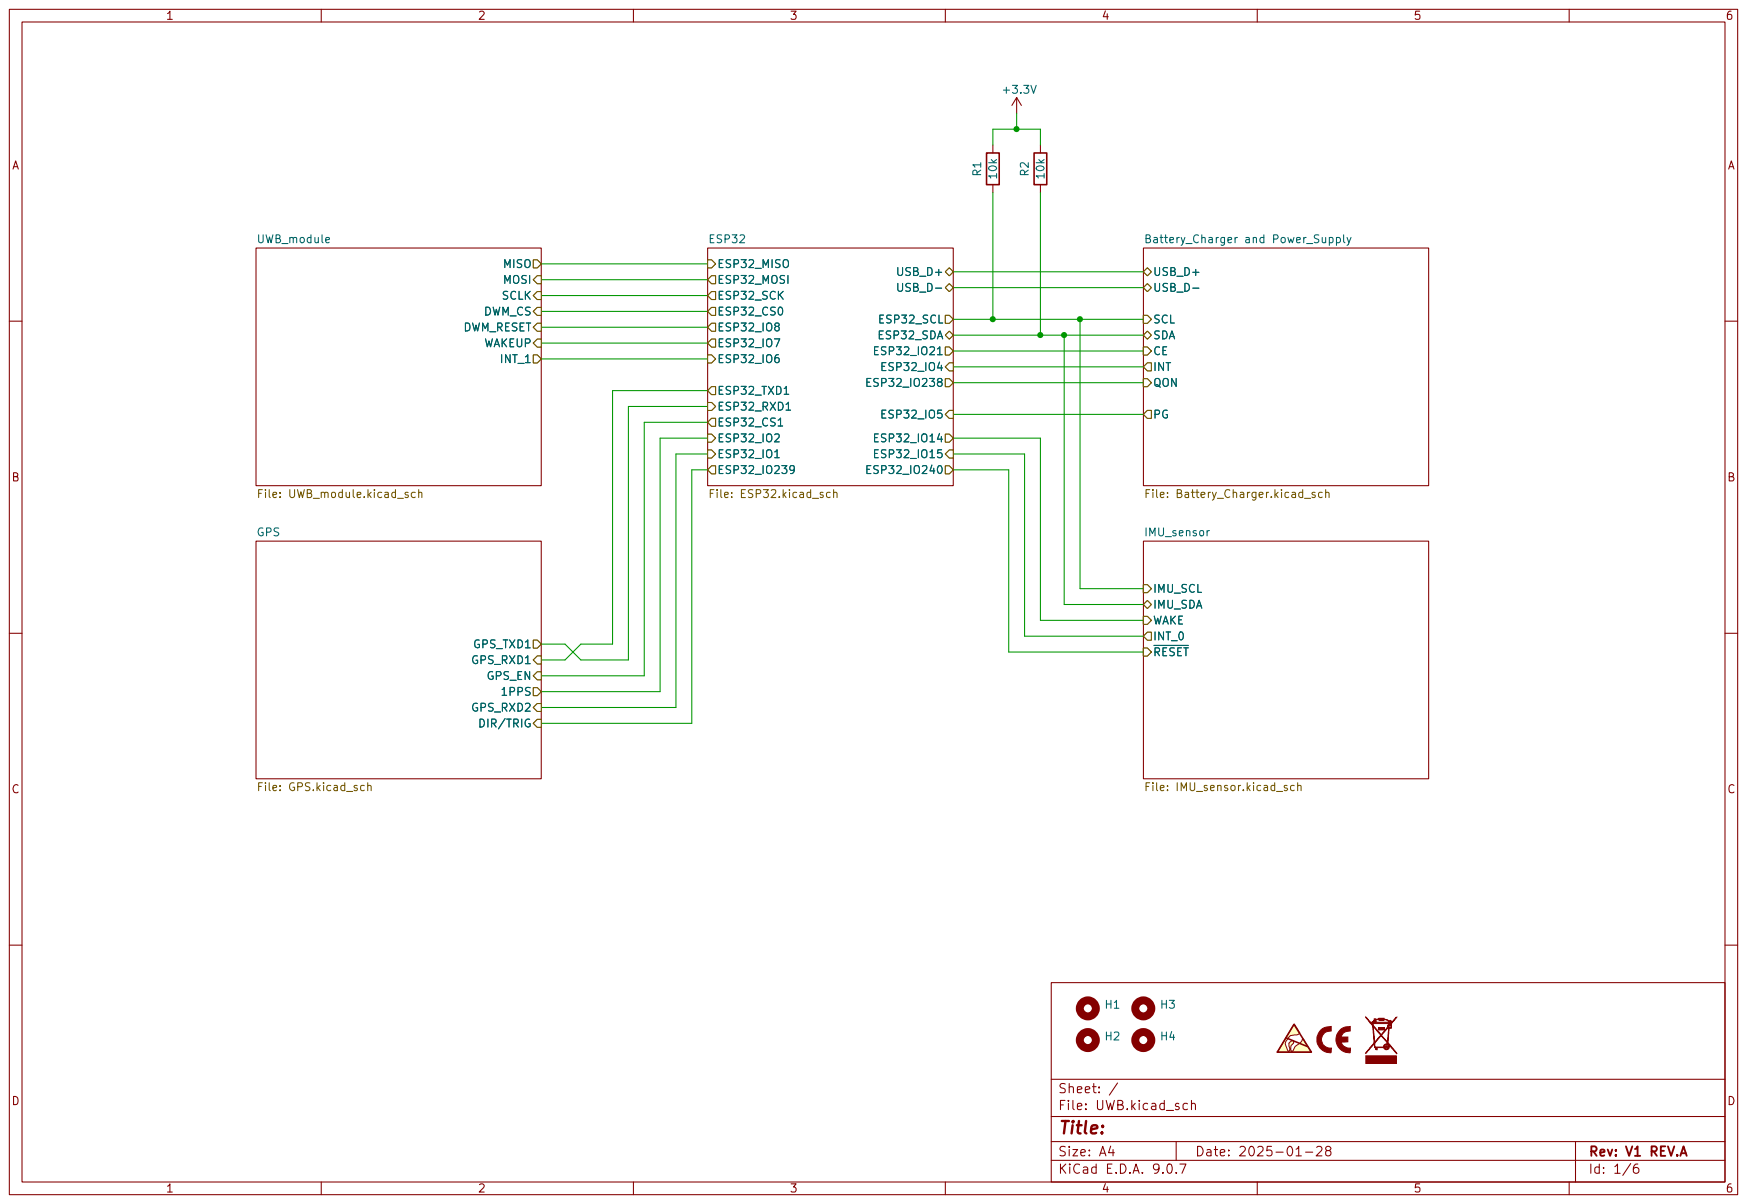
[picture p89: page 1]

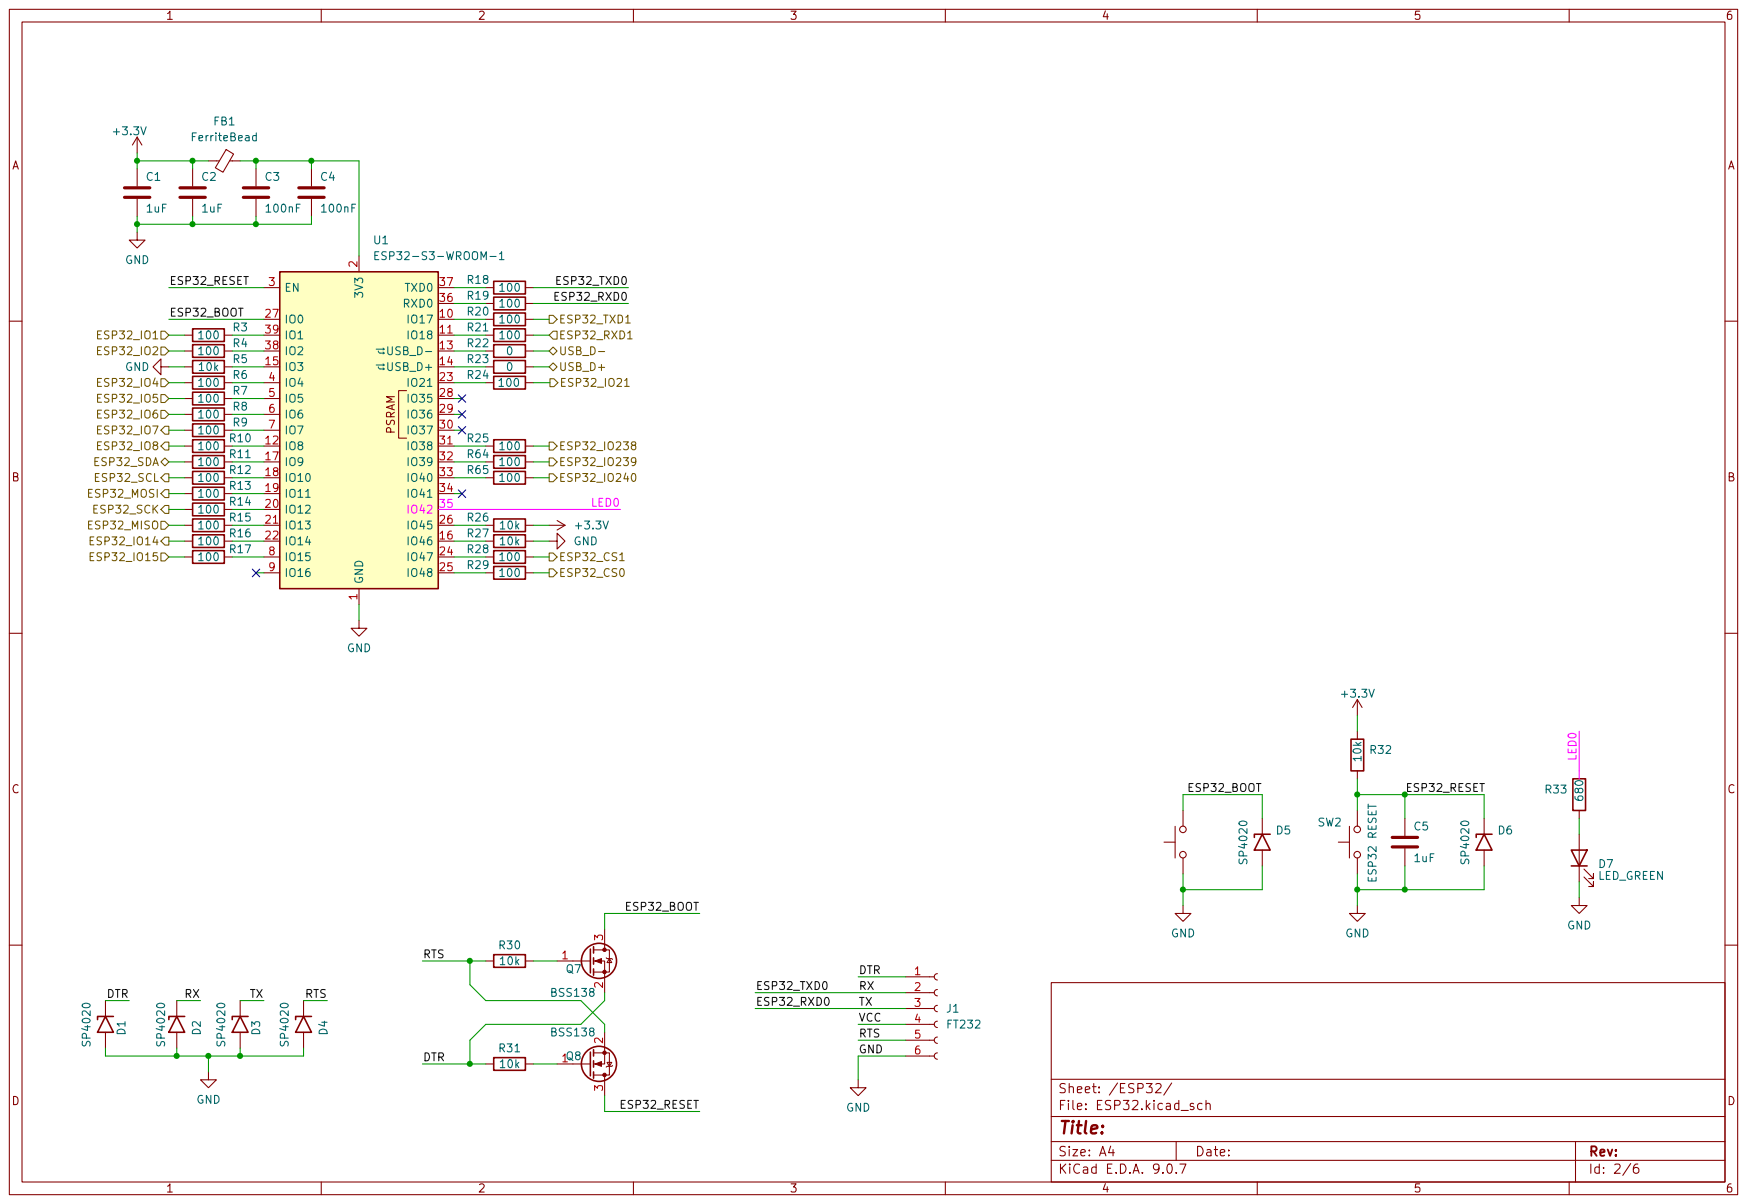
[picture p90: page 2]

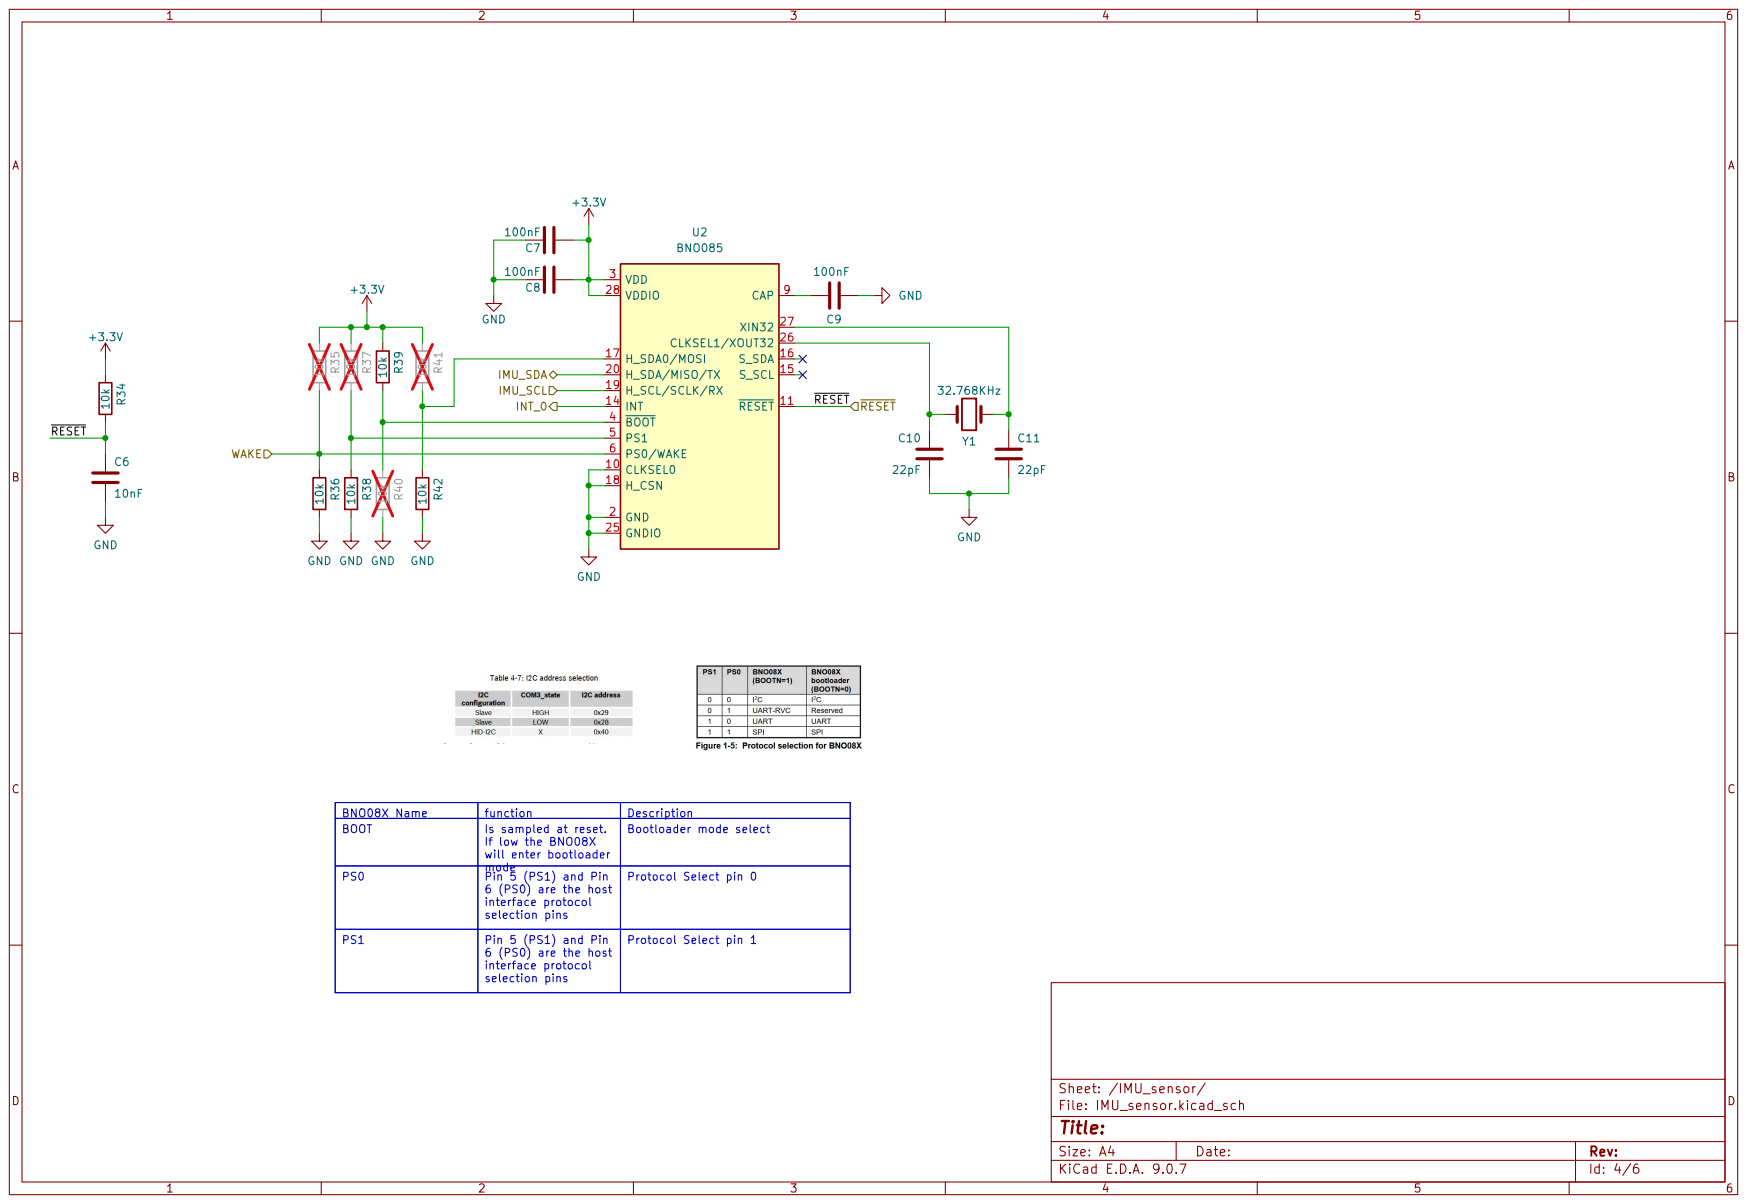
[picture p91: page 3]

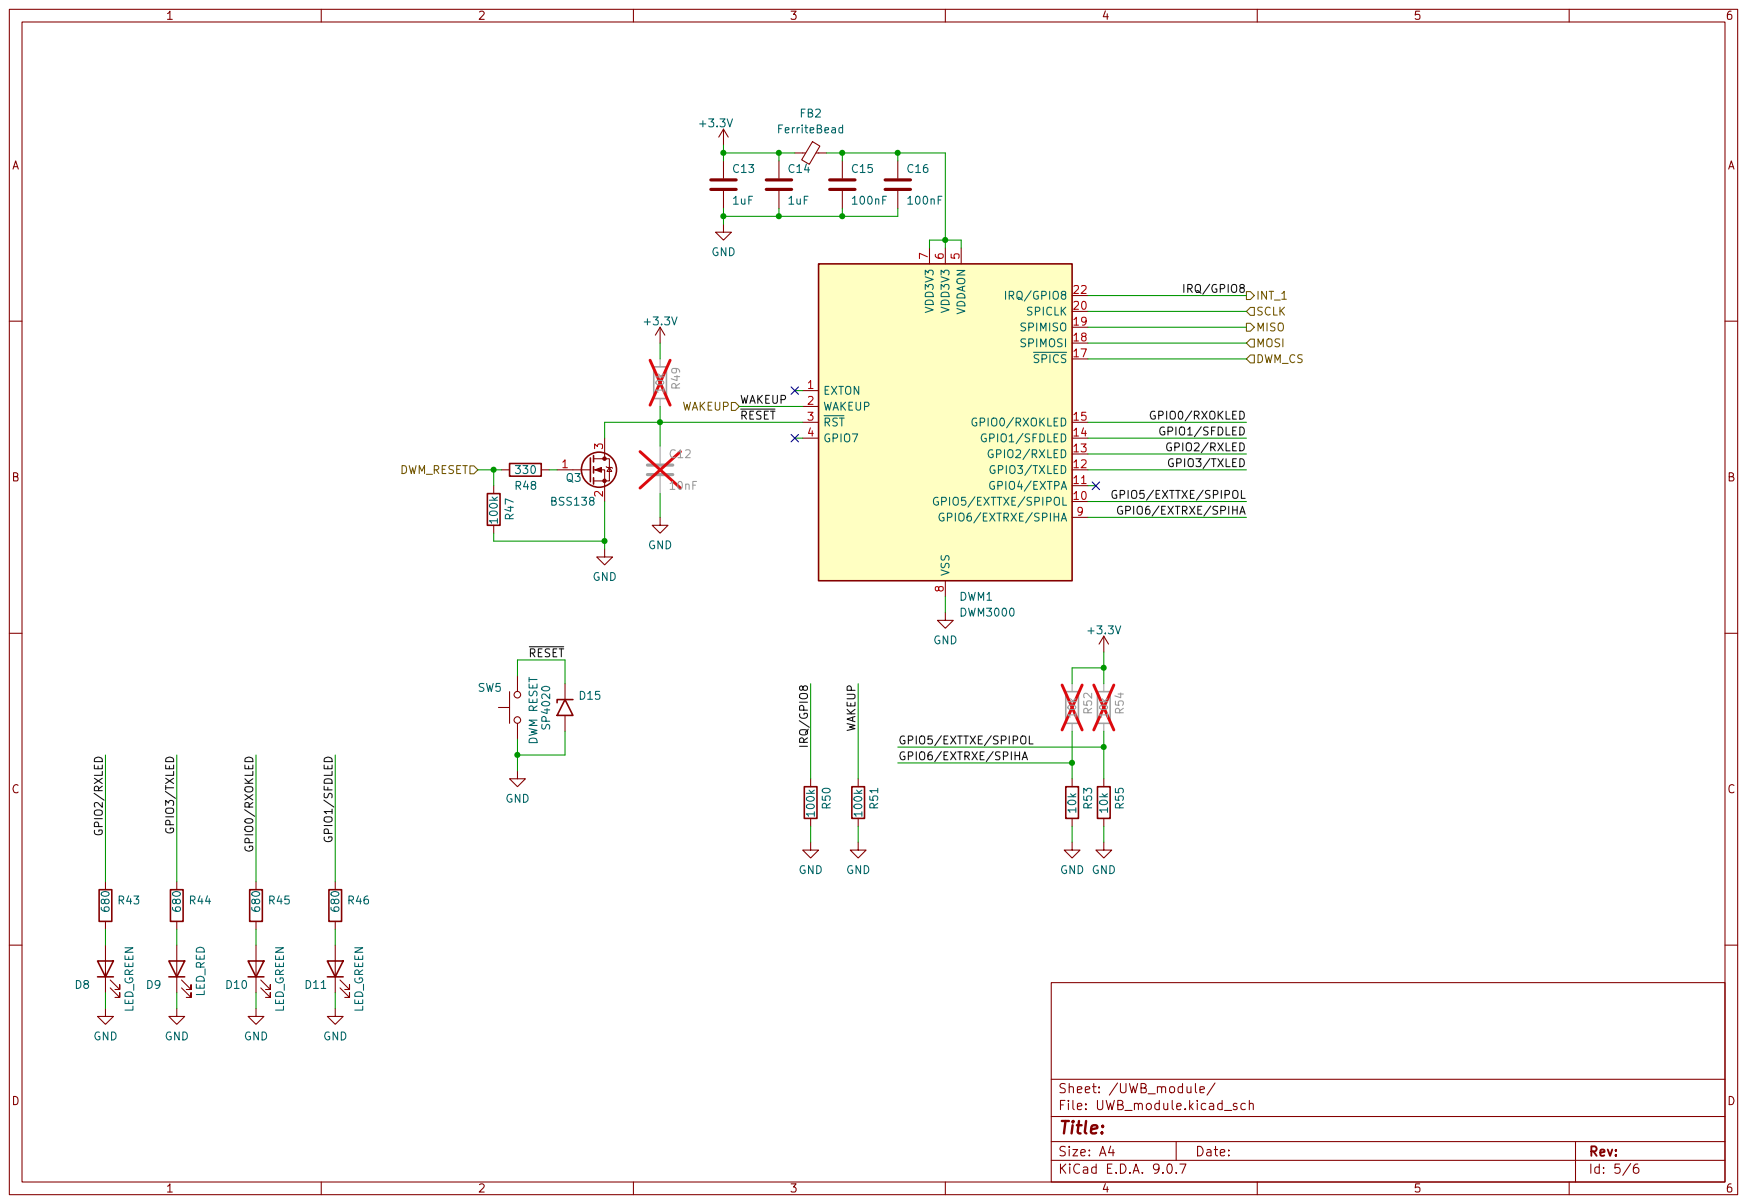
[picture p92: page 4]

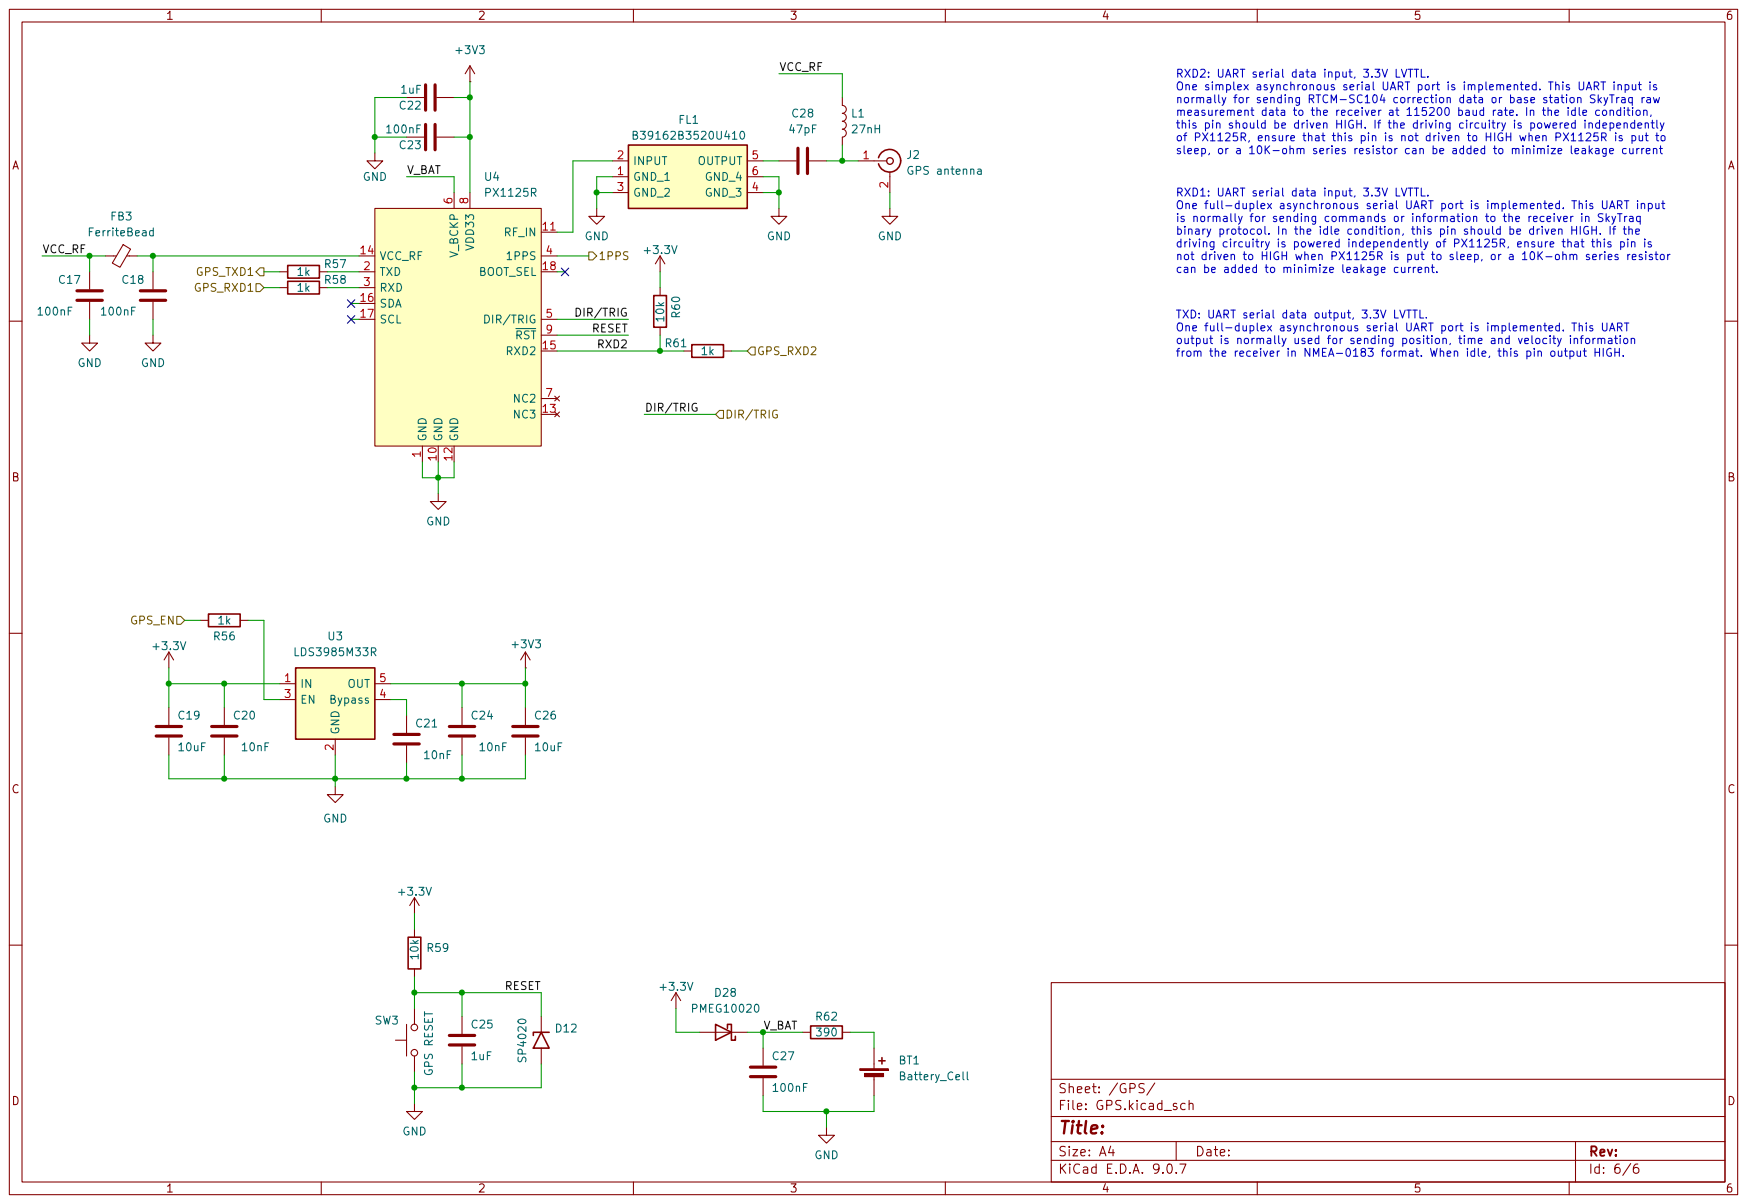
[picture p93: page 5]

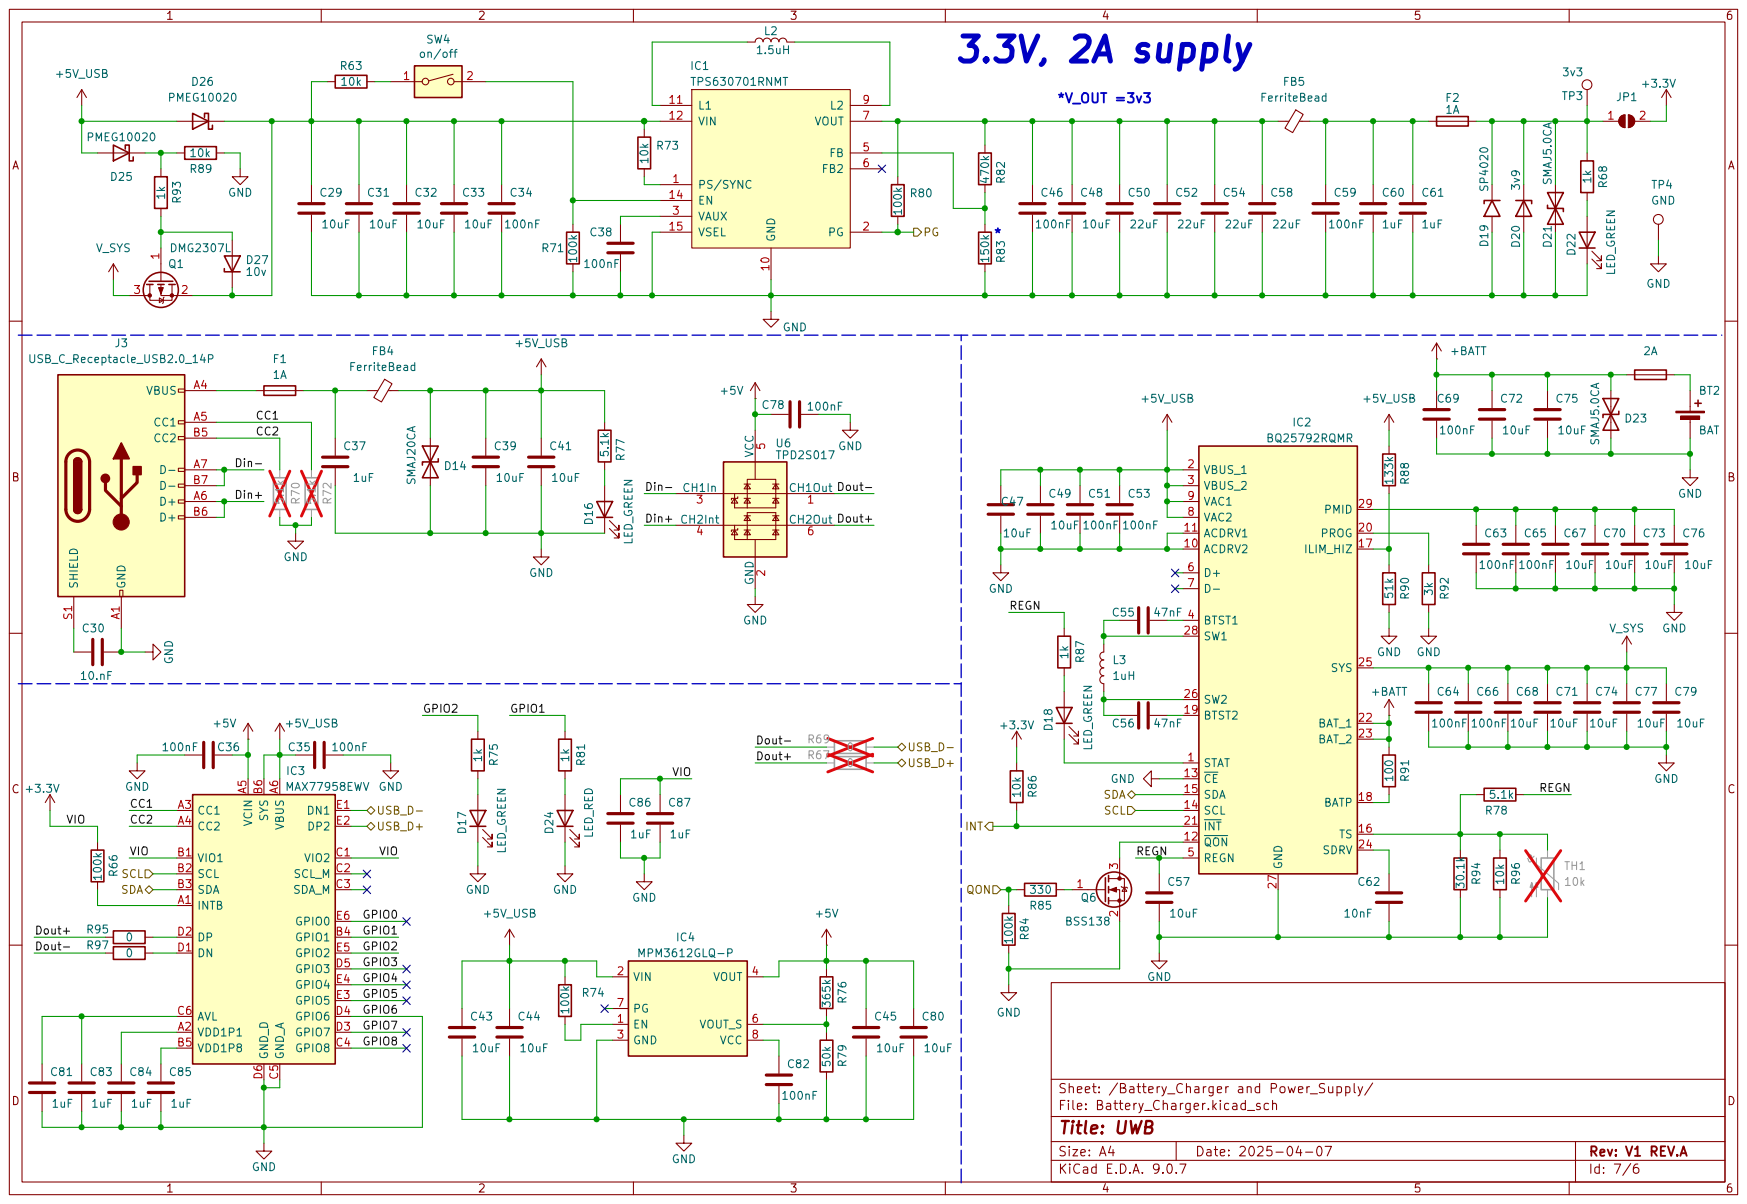
[picture p94: page 6]
