victorstoica114/UWB_Module_ESP_IDF/components/uwb_dw3000/uwb_dw3000.c

#include "uwb_dw3000.h"

#include <stdbool.h>
#include <math.h>
#include <stddef.h>
#include <stdint.h>
#include <string.h>

#include "board_config.h"
#include "driver/gpio.h"
#include "driver/gptimer.h"
#include "driver/spi_master.h"
#include "esp_check.h"
#include "esp_log.h"
#include "esp_mac.h"
#include "esp_random.h"
#include "esp_system.h"
#include "esp_timer.h"
#include "esp_rom_sys.h"
#include "freertos/FreeRTOS.h"
#include "freertos/task.h"
#include "sdkconfig.h"

#include "app_config.h"
#include "app_identity.h"
#include "app_runtime_config.h"
#include "flextdoa_cfo_estimator.h"
#include "flextdoa_collector.h"
#include "flextdoa_protocol.h"
#include "gps_service.h"
#include "uwb_config.h"
#include "uwb_anchor_range_cache.h"
#include "uwb_flex_tdoa_runtime.h"
#include "uwb_native_ds_runtime.h"
#include "uwb_native_ds_twr.h"
#include "uwb_mobile_geometry.h"
#include "uwb_passive_ds_observation.h"
#include "uwb_passive_ds_protocol.h"
#include "uwb_passive_ds_runtime.h"
#include "wireless_log_service.h"
#include "wireless_telemetry_service.h"

static const char *TAG = "uwb_dw3000";

static void uwb_capture_mobile_position(struct uwb_mobile_position *position);

enum {
    /* ESP-IDF expresses the task stack depth in bytes. The multipoint
     * receive-only path keeps several complete radio frames on this task's
     * stack, so the historical 8 KiB allocation is not sufficient. */
    UWB_DW3000_TASK_STACK_BYTES = 32768,
    // FlexTDOA delayed-TX deadlines are sub-millisecond. Keep this below the
    // ESP-IDF timer/Wi-Fi critical tasks, but above ordinary TCP/application
    // work; the task sleeps on the DW3000 interrupt between radio events.
    UWB_DW3000_TASK_PRIORITY = 20,
    UWB_DW3000_SPI_BOOT_CLOCK_HZ = 4 * 1000 * 1000,
    // Project default: ESP32-S3 GPSPI generates 40 MHz exactly from the
    // 80 MHz APB source. This intentionally exceeds the DW3000 datasheet
    // limit of 38 MHz; all field modules have passed repeated DEV_ID reads,
    // OTA boots and sustained FlexTDOA traffic at this clock. Keep the opt-in
    // and the explicit datasheet limit so the exception cannot be accidental.
    UWB_DW3000_SPI_ALLOW_OVERCLOCK = 1,
    UWB_DW3000_SPI_OPERATION_REQUEST_HZ = 40 * 1000 * 1000,
    UWB_DW3000_SPI_DATASHEET_MAX_HZ = 38 * 1000 * 1000,
    UWB_DW3000_SPI_VALIDATED_MAX_HZ = 40 * 1000 * 1000,
    UWB_DW3000_SPI_VERIFY_READS = 8,
    UWB_DW3000_SPI_MAX_TRANSFER_BYTES = 96,
    /* ESP-IDF limits polling transactions to 64 bytes when the SPI bus is
     * initialized without DMA. PDS3 frames are larger, so register windows
     * are transferred in explicitly addressed chunks below. */
    UWB_DW3000_SPI_POLLING_TRANSFER_BYTES = 64,
    UWB_DW3000_RESET_SETTLE_MS = 5,
    UWB_DW3000_RESET_PULSE_MS = 20,
    UWB_DW3000_WAKE_AFTER_RESET_MS = 300,
    UWB_DW3000_PROBE_ATTEMPTS = 16,
    UWB_DW3000_PROBE_INTERVAL_MS = 40,
    UWB_DW3000_IDLE_TIMEOUT_MS = 1000,
    UWB_DW3000_POLL_INTERVAL_MS = 5,
    UWB_DW3000_TX_TIMEOUT_MS = 120,
    UWB_FLEX_TDOA_TX_TIMEOUT_MS = 10,
    UWB_DW3000_TX_POLL_MS = 2,
    /* PDS3 adds a 15-byte RTK position sample to POLL and RESPONSE. */
    UWB_DW3000_PAYLOAD_LEN = 80,
};

_Static_assert(UWB_DW3000_SPI_ALLOW_OVERCLOCK ||
                   UWB_DW3000_SPI_OPERATION_REQUEST_HZ <=
                       UWB_DW3000_SPI_DATASHEET_MAX_HZ,
               "DW3000 operational SPI request exceeds datasheet maximum");
_Static_assert(UWB_DW3000_SPI_ALLOW_OVERCLOCK ||
                   UWB_DW3000_SPI_VALIDATED_MAX_HZ <=
                       UWB_DW3000_SPI_DATASHEET_MAX_HZ,
               "DW3000 validated SPI maximum exceeds datasheet maximum");
_Static_assert(UWB_DW3000_SPI_OPERATION_REQUEST_HZ <=
                   UWB_DW3000_SPI_VALIDATED_MAX_HZ,
               "DW3000 operational SPI request exceeds validated maximum");

#if CONFIG_FREERTOS_NUMBER_OF_CORES > 1
#define UWB_DW3000_TASK_CORE 1
#else
#define UWB_DW3000_TASK_CORE 0
#endif

#define UWB_DW3000_SPI_HOST SPI2_HOST

#define DW3000_REG_GEN_CFG_AES_LOW 0x00
#define DW3000_REG_GEN_CFG_AES_HIGH 0x01
#define DW3000_REG_STS_CFG 0x02
#define DW3000_REG_RX_TUNE 0x03
#define DW3000_REG_EXT_SYNC 0x04
#define DW3000_REG_GPIO_CTRL 0x05
#define DW3000_REG_DRX 0x06
#define DW3000_REG_RF_CONF 0x07
#define DW3000_REG_FS_CTRL 0x09
#define DW3000_REG_AON 0x0A
#define DW3000_REG_OTP_IF 0x0B
#define DW3000_REG_CIA_1 0x0C
#define DW3000_REG_CIA_3 0x0E
#define DW3000_REG_DIG_DIAG 0x0F
/* Qorvo ID 0x10024 encodes register file 0x01, offset 0x24. */
#define DW3000_REG_RDB_STATUS DW3000_REG_GEN_CFG_AES_HIGH
#define DW3000_REG_PMSC 0x11
#define DW3000_REG_RX_BUFFER_0 0x12
#define DW3000_REG_RX_BUFFER_1 0x13
#define DW3000_REG_TX_BUFFER 0x14
#define DW3000_REG_DOUBLE_BUFFER_DIAG 0x18
#define DW3000_REG_INDIRECT_POINTER_B 0x1E
#define DW3000_REG_INDIRECT_CTRL 0x1F

#define DW3000_OTP_CFG_DGC_KICK (1UL << 6U)
#define DW3000_OTP_CFG_DGC_SEL (1UL << 13U)

#define DW3000_SUB_NONE 0x00
#define DW3000_DEV_ID_DW3000 0xDECA0302UL
#define DW3000_DEV_ID_DW3120 0xDECA0312UL

#define DW3000_CMD_TXRXOFF 0x00
#define DW3000_CMD_TX 0x01
#define DW3000_CMD_RX 0x02
#define DW3000_CMD_DTX 0x03
#define DW3000_CMD_TX_W4R 0x0C
#define DW3000_CMD_DTX_W4R 0x0D
#define DW3000_CMD_DB_TOGGLE 0x13

#define DW3000_SYS_CFG_SUB 0x10
#define DW3000_SYS_TIME_SUB 0x1C
#define DW3000_TX_FCTRL_SUB 0x24
#define DW3000_DX_TIME_SUB 0x2C
#define DW3000_RX_FWTO_SUB 0x34
#define DW3000_SYS_ENABLE_LO_SUB 0x3C
#define DW3000_SYS_ENABLE_HI_SUB 0x40
#define DW3000_SYS_STATUS_SUB 0x44
#define DW3000_SYS_STATE_SUB 0x30
#define DW3000_RX_FINFO_SUB 0x4C
#define DW3000_RDB_STATUS_SUB 0x24
#define DW3000_INDIRECT_ADDR_B_SUB 0x0C
#define DW3000_ADDR_OFFSET_B_SUB 0x10
#define DW3000_RX_TIME_SUB 0x00
#define DW3000_ACK_RESP_SUB 0x08
#define DW3000_CHAN_CTRL_SUB 0x14
#define DW3000_DRX_CAR_INT_SUB 0x29
#define DW3000_TX_TIME_SUB 0x74
#define DW3000_STS_CONFIG_HI_SUB 0x16

#define DW3000_CIA_DIAG_0_SUB 0x20
#define DW3000_IP_DIAG_0_SUB 0x28
#define DW3000_IP_DIAG_1_SUB 0x2C
#define DW3000_IP_DIAG_2_SUB 0x30
#define DW3000_IP_DIAG_3_SUB 0x34
#define DW3000_IP_DIAG_4_SUB 0x38
#define DW3000_IP_DIAG_8_SUB 0x48
#define DW3000_IP_DIAG_12_SUB 0x58
#define DW3000_RDB_DIAG_MODE_SUB 0x28

#define DW3000_EVC_CTRL_SUB 0x00
#define DW3000_EVC_COUNT0_SUB 0x04
#define DW3000_EVC_COUNT1_SUB 0x08
#define DW3000_EVC_COUNT2_SUB 0x0C
#define DW3000_EVC_COUNT3_SUB 0x10
#define DW3000_EVC_COUNT4_SUB 0x14
#define DW3000_EVC_COUNT5_SUB 0x18
#define DW3000_EVC_COUNT6_SUB 0x1C
#define DW3000_EVC_COUNT7_SUB 0x28

#define DW3000_GPIO_MODE_SUB 0x00
#define DW3000_GPIO_DIR_SUB 0x08
#define DW3000_PMSC_CLK_CTRL_SUB 0x04
#define DW3000_PMSC_LED_CTRL_SUB 0x16

#define DW3000_GPIO_MODE_MSGP0_MODE_BIT_MASK 0x7UL
#define DW3000_GPIO_MODE_MSGP1_MODE_BIT_MASK 0x38UL
#define DW3000_GPIO_MODE_MSGP2_MODE_BIT_MASK 0x1C0UL
#define DW3000_GPIO_MODE_MSGP3_MODE_BIT_MASK 0xE00UL
#define DW3000_GPIO_PIN0_RXOKLED 0x1UL
#define DW3000_GPIO_PIN1_SFDLED (1UL << (1U * 3U))
#define DW3000_GPIO_PIN2_RXLED (1UL << (2U * 3U))
#define DW3000_GPIO_PIN3_TXLED (1UL << (3U * 3U))

#define DW3000_CLK_CTRL_GPIO_DCLK_EN_BIT_MASK 0x40000UL
#define DW3000_CLK_CTRL_LP_CLK_EN_BIT_MASK 0x800000UL

#define DW3000_LED_CTRL_BLINK_EN_BIT_MASK 0x100UL
#define DW3000_LED_CTRL_FORCE_TRIGGER_BIT_MASK 0xF0000UL
#define DW3000_LED_CTRL_BLINK_TIME_MASK 0xFFUL

#define DW3000_STATUS_TXFRS 0x00000080UL
#define DW3000_STATUS_RX_GOOD_CLEAR_MASK 0x00006F00UL
#define DW3000_STATUS_CIADONE 0x00000400UL
#define DW3000_STATUS_RXFCG 0x00004000UL
#define DW3000_STATUS_RXPHE 0x00001000UL
#define DW3000_STATUS_RXFCE 0x00008000UL
#define DW3000_STATUS_RXFSL 0x00010000UL
#define DW3000_STATUS_RXFTO 0x00020000UL
#define DW3000_STATUS_CIAERR 0x00040000UL
#define DW3000_STATUS_RXOVRR 0x00100000UL
#define DW3000_STATUS_RXPTO 0x00200000UL
#define DW3000_STATUS_RXSTO 0x04000000UL
#define DW3000_STATUS_HPDWARN 0x08000000UL
#define DW3000_SYS_STATE_DELAYED_TX_ERROR 0x000D0000UL
#define DW3000_STATUS_CPERR 0x10000000UL
#define DW3000_STATUS_ARFE 0x20000000UL
#define DW3000_STATUS_SPIRDY 0x00000080UL
#define DW3000_STATUS_RCINIT 0x00000100UL
#define DW3000_STATUS_CLEAR_MASK 0x3F7FFFFFUL

#define DW3000_RX_GOOD_MASK DW3000_STATUS_RXFCG
#define DW3000_RX_ERROR_MASK                                             \
    (DW3000_STATUS_RXPHE | DW3000_STATUS_RXFCE | DW3000_STATUS_RXFSL |   \
     DW3000_STATUS_RXOVRR | DW3000_STATUS_CIAERR | DW3000_STATUS_ARFE)
#define DW3000_RX_TIMEOUT_MASK \
    (DW3000_STATUS_RXFTO | DW3000_STATUS_RXPTO | DW3000_STATUS_RXSTO | DW3000_STATUS_CPERR)
#define DW3000_IRQ_STATUS_MASK \
    (DW3000_STATUS_TXFRS | DW3000_RX_GOOD_MASK | DW3000_RX_ERROR_MASK | \
     DW3000_RX_TIMEOUT_MASK | DW3000_STATUS_HPDWARN)
#define DW3000_RX_FINFO_RXFLEN_MASK 0x000003FFUL
#define DW3000_RX_FINFO_RXPACC_MASK 0xFFF00000UL
#define DW3000_RX_FINFO_RXPACC_SHIFT 20U
#define DW3000_TX_FCTRL_TXB_OFFSET_MASK 0x03FF0000UL
#define DW3000_TX_FCTRL_TR_MASK 0x00000800UL
#define DW3000_TX_FCTRL_TXFLEN_MASK 0x000003FFUL
#define DW3000_TX_FCTRL_TXPSR_MASK 0x0000F000UL
#define DW3000_TX_FCTRL_TXPSR_SHIFT 12U
#define DW3000_TX_FCTRL_TXBR_MASK 0x00000400UL
#define DW3000_TX_FCTRL_TXBR_SHIFT 10U
#define DW3000_CHAN_CTRL_RX_PCODE_MASK 0x00001F00UL
#define DW3000_CHAN_CTRL_RX_PCODE_SHIFT 8U
#define DW3000_CHAN_CTRL_TX_PCODE_MASK 0x000000F8UL
#define DW3000_CHAN_CTRL_TX_PCODE_SHIFT 3U
#define DW3000_CHAN_CTRL_SFD_TYPE_MASK 0x00000006UL
#define DW3000_CHAN_CTRL_SFD_TYPE_SHIFT 1U
#define DW3000_CHAN_CTRL_RF_CHAN_MASK 0x00000001UL
#define DW3000_SYS_CFG_RXWTOE_BIT_MASK 0x00000200UL
#define DW3000_SYS_CFG_RXAUTR_BIT_MASK 0x00000400UL
#define DW3000_SYS_CFG_DIS_DRXB_BIT_MASK 0x00000008UL
#define DW3000_SYS_CFG_CP_SPC_BIT_MASK 0x00003000UL
#define DW3000_SYS_CFG_CP_SDC_BIT_MASK 0x00008000UL
#define DW3000_SYS_CFG_STS_MODE_MASK \
    (DW3000_SYS_CFG_CP_SPC_BIT_MASK | DW3000_SYS_CFG_CP_SDC_BIT_MASK)
#define DW3000_SYS_CFG_STS_MODE_SHIFT 12U
#define DW3000_ACK_RESP_W4R_TIM_BIT_MASK 0x000FFFFFUL

#define DW3000_STS_CONFIG_HI_RES 0x94UL
#define DW3000_STS_CONFIG_HI_CHECK_MASK \
    (0x80000000UL | 0x40000000UL | 0x000000F0UL)

#define DW3000_EVC_CTRL_CLR_BIT_MASK 0x02U
#define DW3000_EVC_CTRL_EN_BIT_MASK 0x01U
#define DW3000_EVC_12BIT_LOW_MASK 0x00000FFFUL
#define DW3000_EVC_12BIT_HIGH_MASK 0x0FFF0000UL
#define DW3000_EVC_8BIT_LOW_MASK 0x000000FFUL
#define DW3000_EVC_8BIT_HIGH_MASK 0x00FF0000UL
#define DW3000_EVC_HIGH_SHIFT 16U

#define DW3000_CIA_CONF_DIAGNOSTIC_OFF_MASK 0x00100000UL
#define DW3000_CIA_DIAG_LOG_ALL 0x01U
#define DW3000_CIA_DIAG_LOG_MIN 0x02U
#define DW3000_CLOCK_OFFSET_RAW_MASK 0x001FFFFFUL
#define DW3000_CLOCK_OFFSET_RAW_BITS 21U
#define DW3000_CLOCK_OFFSET_CH5_FACTOR (-0.5731e-9)
#define DW3000_CLOCK_OFFSET_CH9_FACTOR (-0.1252e-9)
#define DW3000_DOUBLE_BUFFER_0_RX_FINFO_SUB 0x00U
#define DW3000_DOUBLE_BUFFER_0_RX_TIME_SUB 0x04U
#define DW3000_DOUBLE_BUFFER_0_CIA_DIAG_0_SUB 0x0CU
#define DW3000_DOUBLE_BUFFER_1_RX_FINFO_OFFSET 0x00U
#define DW3000_DOUBLE_BUFFER_1_RX_TIME_OFFSET 0x04U
#define DW3000_DOUBLE_BUFFER_1_CIA_DIAG_0_OFFSET 0x0CU
#define DW3000_DOUBLE_BUFFER_RX_META_LEN 8U
#define DW3000_DOUBLE_BUFFER_FLEX_META_LEN 14U
#define DW3000_DOUBLE_BUFFER_1_DIAG_BASE 0x18U
#define DW3000_DOUBLE_BUFFER_1_DIAG_OFFSET 0x00E8U
#define DW3000_RDB_BUFFER_0_GOOD_MASK 0x01U
#define DW3000_RDB_BUFFER_1_GOOD_MASK 0x10U
#define DW3000_RDB_BUFFER_0_CIA_DONE_MASK 0x04U
#define DW3000_RDB_BUFFER_1_CIA_DONE_MASK 0x40U
#define DW3000_RDB_BUFFER_0_CLEAR_MASK 0x0FU
#define DW3000_RDB_BUFFER_1_CLEAR_MASK 0xF0U
#define DW3000_IPATOV_PEAK_MASK 0x7FFFFFFFUL
#define DW3000_IPATOV_PEAK_AMP_MASK 0x001FFFFFUL
#define DW3000_IPATOV_PEAK_INDEX_SHIFT 21U
#define DW3000_IPATOV_POWER_MASK 0x0001FFFFUL
#define DW3000_IPATOV_F_MASK 0x003FFFFFUL
#define DW3000_IPATOV_FP_INDEX_MASK 0x0000FFFFUL
#define DW3000_IPATOV_ACCUM_COUNT_MASK 0x00000FFFUL
#define DW3000_CIA_XTAL_OFFSET_MASK 0x00001FFFUL

#define UWB_DW3000_TIMESTAMP_MASK ((1ULL << 40U) - 1ULL)
#define UWB_DW3000_DELAYED_TIME_MASK 0xFFFFFFFEUL
#define UWB_DW3000_TIME_UNIT_SECONDS 15.650040064102564e-12
#define UWB_DW3000_SPEED_OF_LIGHT_MPS 299702547.0

#define UWB_DISTANCE_FRAME_MAGIC_0 'U'
#define UWB_DISTANCE_FRAME_MAGIC_1 'W'
#define UWB_DISTANCE_FRAME_MAGIC_2 'B'
#define UWB_DISTANCE_FRAME_MAGIC_3 'R'
#define UWB_DISTANCE_FRAME_VERSION 1U
#define UWB_DISTANCE_FRAME_HEADER_LEN 10U
#define UWB_DISTANCE_FRAME_POLL_TX_TS_OFFSET 10U
#define UWB_DISTANCE_FRAME_POLL_RX_TS_OFFSET 15U
#define UWB_DISTANCE_FRAME_RESP_TX_TS_OFFSET 20U
#define UWB_DISTANCE_FRAME_RESP_RX_TS_OFFSET 25U
#define UWB_DISTANCE_FRAME_FINAL_TX_TS_OFFSET 30U
#define UWB_DISTANCE_FRAME_FINAL_RX_TS_OFFSET 35U
#define UWB_DISTANCE_FRAME_DISTANCE_MM_OFFSET 40U
#define UWB_DISTANCE_FRAME_RAW_DISTANCE_MM_OFFSET 44U
#define UWB_DISTANCE_FRAME_FINAL_TIMESTAMPS_LEN \
    (UWB_DISTANCE_FRAME_FINAL_TX_TS_OFFSET + 5U)
#define UWB_DISTANCE_FRAME_POLL_LEN UWB_DISTANCE_FRAME_HEADER_LEN
#define UWB_DISTANCE_FRAME_RESP_LEN UWB_DISTANCE_FRAME_HEADER_LEN
#define UWB_DISTANCE_FRAME_FINAL_LEN UWB_DISTANCE_FRAME_HEADER_LEN
#define UWB_DISTANCE_FRAME_REPORT_LEN UWB_DISTANCE_FRAME_FINAL_TIMESTAMPS_LEN
#define UWB_DISTANCE_FRAME_REPORT2_LEN \
    (UWB_DISTANCE_FRAME_RAW_DISTANCE_MM_OFFSET + sizeof(int32_t))
#define UWB_DISTANCE_FRAME_BROADCAST_ID 255U

/*
 * Passive DS-TWR keeps the native three-message exchange, but makes the
 * responder turnaround explicit so any receive-only tag can form a TDOA
 * observation from POLL_RX -> RESP_RX. FINAL still completes a genuine
 * anchor-to-anchor DS-TWR measurement.
 */
#define UWB_PASSIVE_DS_SLOT_ID_OFFSET UWB_DISTANCE_FRAME_HEADER_LEN
#define UWB_PASSIVE_DS_REPLY_DTU_OFFSET \
    (UWB_PASSIVE_DS_SLOT_ID_OFFSET + 4U)
#define UWB_PASSIVE_DS_POLL_PIGGYBACK_OFFSET \
    (UWB_PASSIVE_DS_SLOT_ID_OFFSET + 4U)
#define UWB_PASSIVE_DS_RESP_PIGGYBACK_OFFSET \
    (UWB_PASSIVE_DS_REPLY_DTU_OFFSET + 4U)
#define UWB_PASSIVE_DS_PIGGYBACK_PEER_OFFSET 0U
#define UWB_PASSIVE_DS_PIGGYBACK_DISTANCE_MM_OFFSET 1U
#define UWB_PASSIVE_DS_PIGGYBACK_RAW_DISTANCE_MM_OFFSET 3U
#define UWB_PASSIVE_DS_PIGGYBACK_SLOT_ID_OFFSET 5U
#define UWB_PASSIVE_DS_PIGGYBACK_SEQUENCE_OFFSET 9U
#define UWB_PASSIVE_DS_PIGGYBACK_EXCHANGE_DTU_OFFSET 11U
#define UWB_PASSIVE_DS_PIGGYBACK_LEN 15U
#define UWB_PASSIVE_DS_POLL_LEN \
    (UWB_PASSIVE_DS_POLL_PIGGYBACK_OFFSET + \
     UWB_PASSIVE_DS_PIGGYBACK_LEN)
#define UWB_PASSIVE_DS_RESP_LEN \
    (UWB_PASSIVE_DS_RESP_PIGGYBACK_OFFSET + \
     UWB_PASSIVE_DS_PIGGYBACK_LEN)
#define UWB_PASSIVE_DS_FINAL_SLOT_ID_OFFSET \
    UWB_DISTANCE_FRAME_FINAL_TIMESTAMPS_LEN
#define UWB_PASSIVE_DS_FINAL_LEN \
    (UWB_PASSIVE_DS_FINAL_SLOT_ID_OFFSET + 4U)
#define UWB_PASSIVE_DS_MULTI_APPLICATION_OFFSET \
    UWB_DISTANCE_FRAME_HEADER_LEN
#define UWB_PASSIVE_DS_MULTI_POLL_PIGGYBACK_OFFSET \
    (UWB_PASSIVE_DS_MULTI_APPLICATION_OFFSET + 4U)
#define UWB_PASSIVE_DS_MULTI_RESP_PIGGYBACK_OFFSET \
    (UWB_PASSIVE_DS_MULTI_APPLICATION_OFFSET + 9U)
#define UWB_PASSIVE_DS_MULTI_POLL_LEN \
    (UWB_PASSIVE_DS_MULTI_POLL_PIGGYBACK_OFFSET + \
     UWB_PASSIVE_DS_PIGGYBACK_LEN)
#define UWB_PASSIVE_DS_MULTI_RESP_LEN \
    (UWB_PASSIVE_DS_MULTI_RESP_PIGGYBACK_OFFSET + \
     UWB_PASSIVE_DS_PIGGYBACK_LEN)
#define UWB_PASSIVE_DS_BOOTSTRAP_LISTEN_US 2000000LL
#define UWB_PASSIVE_DS_FAST_GEOMETRY_FRAME_INTERVAL 4U
#define UWB_PASSIVE_DS_POLL_TX_LEAD_US 750LL
#define UWB_PASSIVE_DS_MULTI_POLL_TX_LEAD_US 2000LL
#define UWB_PASSIVE_DS_POLL_LATE_US 250LL
#define UWB_PASSIVE_DS_MULTI_RESPONSE_COLLECTION_SLACK_US 500LL
#define UWB_PASSIVE_DS_MULTI_RECOVERY_FRAMES 8LL
#define UWB_PASSIVE_DS_MULTI_RECOVERY_MIN_US 50000LL
#define UWB_ANCHOR_SURVEY_MAX_ANCHORS APP_RUNTIME_CONFIG_MAX_ANCHORS
#define UWB_ANCHOR_SURVEY_MAX_PAIRS \
    ((UWB_ANCHOR_SURVEY_MAX_ANCHORS * (UWB_ANCHOR_SURVEY_MAX_ANCHORS - 1U)) / 2U)
#define UWB_FLEX_TDOA_MAX_OBSERVATIONS \
    (UWB_ANCHOR_SURVEY_MAX_ANCHORS * (UWB_ANCHOR_SURVEY_MAX_ANCHORS - 1U))
#define UWB_ANCHOR_SURVEY_CMD_INITIATOR_OFFSET 10U
#define UWB_ANCHOR_SURVEY_CMD_RESPONDER_OFFSET 11U
#define UWB_ANCHOR_SURVEY_CMD_SLOT_OFFSET 12U
#define UWB_ANCHOR_SURVEY_CMD_LEN \
    (UWB_ANCHOR_SURVEY_CMD_SLOT_OFFSET + 1U)
#define UWB_FLEX_TDOA_CONFIG_GENERATION_OFFSET 10U
#define UWB_FLEX_TDOA_CONFIG_N_OFFSET 14U
#define UWB_FLEX_TDOA_CONFIG_K_OFFSET 15U
#define UWB_FLEX_TDOA_CONFIG_M_OFFSET 16U
#define UWB_FLEX_TDOA_CONFIG_ANCHORS_OFFSET 17U
#define UWB_FLEX_TDOA_CONFIG_SLOTS_OFFSET \
    (UWB_FLEX_TDOA_CONFIG_ANCHORS_OFFSET + APP_RUNTIME_CONFIG_MAX_ANCHORS)
#define UWB_FLEX_TDOA_CONFIG_MASKS_OFFSET \
    (UWB_FLEX_TDOA_CONFIG_SLOTS_OFFSET + \
     ((APP_RUNTIME_CONFIG_FLEX_MAX_SLOTS + 1U) / 2U))
#define UWB_FLEX_TDOA_CONFIG_LEN \
    (UWB_FLEX_TDOA_CONFIG_MASKS_OFFSET + \
     ((APP_RUNTIME_CONFIG_MAX_ANCHORS * \
       APP_RUNTIME_CONFIG_FLEX_MAX_SLOTS + 7U) / 8U) + 10U)
#define UWB_FLEX_TDOA_CONFIG_GUARD_US_OFFSET \
    (UWB_FLEX_TDOA_CONFIG_LEN - 10U)
#define UWB_FLEX_TDOA_CONFIG_REQ_US_OFFSET \
    (UWB_FLEX_TDOA_CONFIG_LEN - 8U)
#define UWB_FLEX_TDOA_CONFIG_REQ_PROCESS_US_OFFSET \
    (UWB_FLEX_TDOA_CONFIG_LEN - 6U)
#define UWB_FLEX_TDOA_CONFIG_RESP_US_OFFSET \
    (UWB_FLEX_TDOA_CONFIG_LEN - 4U)
#define UWB_FLEX_TDOA_CONFIG_RESP_PROCESS_US_OFFSET \
    (UWB_FLEX_TDOA_CONFIG_LEN - 2U)
#define UWB_FLEX_TDOA_GEOMETRY_GENERATION_OFFSET 10U
#define UWB_FLEX_TDOA_GEOMETRY_FIXED_OFFSET 14U
#define UWB_FLEX_TDOA_GEOMETRY_COUNT_OFFSET 15U
#define UWB_FLEX_TDOA_GEOMETRY_INDEX_OFFSET 16U
#define UWB_FLEX_TDOA_GEOMETRY_ANCHOR_ID_OFFSET 17U
#define UWB_FLEX_TDOA_GEOMETRY_X_MM_OFFSET 18U
#define UWB_FLEX_TDOA_GEOMETRY_Y_MM_OFFSET 22U
#define UWB_FLEX_TDOA_GEOMETRY_LEN 26U
#define UWB_FLEX_TDOA_CONFIG_PHASE_US 3000000LL
#define UWB_FLEX_TDOA_CONFIG_TX_SPACING_US 30000LL
#define UWB_FLEX_TDOA_CONFIG_FRAME_GAP_MS 10U
#define UWB_FLEX_TDOA_BOOTSTRAP_LISTEN_US 2000000LL
#define UWB_HOT_SWITCH_BOOTSTRAP_GUARD_US 150000LL
#define UWB_FLEX_TDOA_EPOCH_BACKJUMP_FRAMES 8U
// Host-only preparation lead. It must be shorter than one 4.80 ms slot so an
// initiator keeps receiving the preceding slot while still programming its
// own DW3000 delayed TX with comfortable margin.
#define UWB_FLEX_TDOA_REQUEST_TX_LEAD_US 1750LL
#define UWB_FLEX_TDOA_REQUEST_LATE_US 500LL
#define UWB_FLEX_TDOA_RX_EPOCH_MAX_GAP_US 30000LL

enum uwb_distance_frame_type {
    UWB_DISTANCE_FRAME_POLL = 1,
    UWB_DISTANCE_FRAME_RESP = 2,
    UWB_DISTANCE_FRAME_FINAL = 3,
    UWB_DISTANCE_FRAME_REPORT = 4,
    UWB_DISTANCE_FRAME_SURVEY_CMD = 5,
    UWB_DISTANCE_FRAME_REPORT2 = 6,
    UWB_DISTANCE_FRAME_CAL_CMD = 7,
    UWB_DISTANCE_FRAME_CAL_SYNC = 8,
    UWB_DISTANCE_FRAME_FLEX_TDOA_REQ = 11,
    UWB_DISTANCE_FRAME_FLEX_TDOA_RESP = 12,
    UWB_DISTANCE_FRAME_FLEX_TDOA_CONFIG = 13,
    UWB_DISTANCE_FRAME_FLEX_TDOA_GEOMETRY = 14,
    UWB_DISTANCE_FRAME_PASSIVE_DS_POLL = 15,
    UWB_DISTANCE_FRAME_PASSIVE_DS_RESP = 16,
    UWB_DISTANCE_FRAME_PASSIVE_DS_FINAL = 17,
    UWB_DISTANCE_FRAME_PASSIVE_DS_MULTI_POLL = 18,
    UWB_DISTANCE_FRAME_PASSIVE_DS_MULTI_RESP = 19,
    UWB_DISTANCE_FRAME_PASSIVE_DS_MULTI_FINAL = 20,
};

enum uwb_dw3000_runtime_mode {
    UWB_DW3000_RUNTIME_BEACON_SMOKE = 0,
    UWB_DW3000_RUNTIME_DISTANCE_TEST,
    UWB_DW3000_RUNTIME_CALIBRATION,
    UWB_DW3000_RUNTIME_ANCHOR_SURVEY,
    UWB_DW3000_RUNTIME_RANGING,
    UWB_DW3000_RUNTIME_FLEX_TDOA,
    UWB_DW3000_RUNTIME_PASSIVE_DS_TWR,
};

struct uwb_rx_diagnostics {
    bool valid;
    uint16_t rx_pacc;
    int16_t xtal_offset;
    uint32_t ipatov_peak_amp;
    uint16_t ipatov_peak_index;
    uint32_t ipatov_power;
    uint32_t ipatov_f1;
    uint32_t ipatov_f2;
    uint32_t ipatov_f3;
    uint16_t ipatov_fp_index;
    uint16_t ipatov_accum_count;
};

struct uwb_event_counters {
    uint16_t rse;
    uint16_t phe;
    uint16_t fce;
    uint16_t fcg;
    uint8_t ovr;
    uint8_t ffr;
    uint16_t pto;
    uint16_t sfdt;
    uint16_t txfs;
    uint8_t fwto;
    uint8_t swce;
    uint8_t hpw;
    uint16_t prej;
    uint8_t vwarn;
    uint8_t cpqe;
};

struct uwb_dw3000_rx_frame {
    uint8_t payload[UWB_DW3000_PAYLOAD_LEN];
    uint16_t payload_len;
    uint64_t rx_timestamp;
    int64_t rx_host_time_us;
    uint8_t rx_buffer_index;
    uint8_t rx_buffer_status;
    bool clock_offset_valid;
    bool clock_offset_from_cia;
    int32_t clock_offset_raw;
    struct uwb_rx_diagnostics diagnostics;
};

struct uwb_distance_frame {
    uint8_t type;
    uint8_t source_id;
    uint8_t destination_id;
    uint16_t sequence;
    uint64_t rx_timestamp;
    int64_t rx_host_time_us;
    uint8_t rx_buffer_index;
    uint8_t rx_buffer_status;
    bool clock_offset_valid;
    bool clock_offset_from_cia;
    int32_t clock_offset_raw;
    struct uwb_rx_diagnostics diagnostics;
    uint8_t payload[UWB_DW3000_PAYLOAD_LEN];
    uint16_t payload_len;
};

struct uwb_distance_measurement {
    uint8_t initiator_id;
    uint8_t responder_id;
    uint16_t sequence;
    double tof_dtu;
    double distance_m;
    double raw_tof_dtu;
    double raw_distance_m;
    double clock_offset_ratio;
    bool clock_offset_valid;
    int32_t clock_offset_raw;
    uint64_t poll_tx_ts;
    uint64_t poll_rx_ts;
    uint64_t resp_tx_ts;
    uint64_t resp_rx_ts;
    uint64_t final_tx_ts;
    uint64_t final_rx_ts;
    struct uwb_rx_diagnostics poll_rx_diagnostics;
    struct uwb_rx_diagnostics final_rx_diagnostics;
    struct uwb_rx_diagnostics report_rx_diagnostics;
};

struct uwb_anchor_survey_pair {
    uint8_t initiator_id;
    uint8_t responder_id;
};

struct uwb_flex_tdoa_observation {
    bool in_use;
    uint16_t sequence;
    uint32_t slot_id;
    uint8_t initiator_id;
    uint8_t responder_id;
    uint8_t responder_index;
    uint64_t request_rx_tag_ts;
    uint64_t response_rx_tag_ts;
    uint64_t responder_reply_dtu;
    int32_t anchor_distance_mm;
    uint32_t anchor_distance_slot_id;
    bool have_request;
    bool have_response;
    bool resp_clock_offset_valid;
    int32_t resp_clock_offset_raw;
    double resp_clock_offset_ratio;
    struct uwb_mobile_position initiator_position;
    struct uwb_mobile_position responder_position;
    bool dynamic_geometry;
    int32_t initiator_x_mm;
    int32_t initiator_y_mm;
    int32_t responder_x_mm;
    int32_t responder_y_mm;
    uint32_t geometry_version;
    int32_t geometry_fit_rms_mm;
    bool geometry_all_rtk_fixed;
    TickType_t updated_tick;
};

struct uwb_flex_tdoa_message_metadata {
    uint32_t slot_id;
    uint8_t destination_count;
    uint8_t destinations[UWB_ANCHOR_SURVEY_MAX_ANCHORS - 1U];
    uint32_t processing_dtu;
    uint8_t previous_responder_id;
    uint16_t previous_distance_mm;
    uint16_t previous_slot_id;
    struct uwb_mobile_position sender_position;
};

struct uwb_flex_tdoa_local_request {
    bool active;
    uint16_t sequence;
    uint32_t slot_id;
    uint8_t initiator_id;
    uint8_t responder_count;
    uint8_t responses_seen;
    uint8_t responders[UWB_ANCHOR_SURVEY_MAX_ANCHORS - 1U];
    uint64_t tx_timestamp;
    TickType_t updated_tick;
};

struct uwb_flex_tdoa_schedule {
    bool synced;
    bool reference_from_request;
    uint8_t own_slot_index;
    uint32_t reference_slot_id;
    uint32_t next_slot_id;
    uint64_t next_request_radio_ts;
    int64_t next_request_host_us;
    int64_t last_sync_host_us;
    uint32_t sync_count;
    uint32_t missed_slots;
};

struct uwb_flex_tdoa_geometry_staging {
    uint32_t generation;
    uint8_t anchor_count;
    uint16_t received_mask;
    int32_t anchor_x_mm[APP_RUNTIME_CONFIG_MAX_ANCHORS];
    int32_t anchor_y_mm[APP_RUNTIME_CONFIG_MAX_ANCHORS];
};

#if 0 /* Passive DS-TWR v1 types: retired by the PDS3 clean runtime below. */
struct uwb_passive_ds_schedule {
    bool synced;
    uint32_t next_owned_slot_id;
    uint64_t next_owned_poll_radio_ts;
    int64_t next_owned_poll_host_us;
    int64_t last_poll_host_us;
    uint32_t bootstrap_count;
    uint32_t late_count;
};

struct uwb_passive_ds_multi_schedule {
    bool synced;
    uint32_t next_frame_id;
    uint64_t next_poll_radio_ts;
    int64_t next_poll_host_us;
    int64_t last_poll_host_us;
    uint32_t bootstrap_count;
    uint32_t late_count;
};

struct uwb_passive_ds_multi_tag_stats {
    uint32_t poll_rx;
    uint32_t response_rx[UWB_PASSIVE_DS_MULTI_MAX_RESPONDERS];
    uint32_t final_rx;
    uint32_t final_entries;
    uint32_t ready[UWB_PASSIVE_DS_MULTI_MAX_ANCHORS];
    uint32_t rejected[UWB_PASSIVE_DS_MULTI_MAX_ANCHORS];
    uint32_t piggyback_lag[8];
    uint32_t previous_ready_count;
    uint32_t previous_calculation_rejected_count;
    uint32_t previous_missing_final_context_count;
    uint32_t previous_missing_exchange_context_count;
    uint32_t previous_pending_replacement_count;
    int64_t summary_started_us;
};

static void uwb_passive_ds_multi_tag_record_piggyback_lag(
    struct uwb_passive_ds_multi_tag_stats *stats,
    uint32_t current_frame_id, uint8_t piggyback_initiator_id,
    uint32_t piggyback_frame_id)
{
    if (stats == NULL || piggyback_initiator_id == 0U) {
        return;
    }
    const uint32_t lag = current_frame_id - piggyback_frame_id;
    stats->piggyback_lag[lag < 7U ? lag : 7U]++;
}

enum uwb_passive_ds_exchange_state {
    UWB_PASSIVE_DS_EXCHANGE_IDLE = 0,
    UWB_PASSIVE_DS_EXCHANGE_WAIT_RESPONSE,
    UWB_PASSIVE_DS_EXCHANGE_WAIT_FINAL,
};

struct uwb_passive_ds_exchange {
    enum uwb_passive_ds_exchange_state state;
    uint16_t sequence;
    uint32_t slot_id;
    uint8_t peer_id;
    int64_t started_host_us;
    int64_t deadline_host_us;
    uint64_t poll_tx_ts;
    uint64_t poll_rx_ts;
    uint64_t response_tx_ts;
    struct uwb_rx_diagnostics poll_rx_diagnostics;
};

enum uwb_passive_ds_range_source {
    UWB_PASSIVE_DS_RANGE_NONE = 0,
    UWB_PASSIVE_DS_RANGE_PIGGYBACK_DS = 1,
};
#endif

static struct uwb_flex_tdoa_geometry_staging s_flex_tdoa_geometry_staging;

enum uwb_flex_tdoa_config_result {
    UWB_FLEX_TDOA_CONFIG_INVALID,
    UWB_FLEX_TDOA_CONFIG_CURRENT,
    UWB_FLEX_TDOA_CONFIG_UPDATED,
};

static void uwb_distance_put_u32(uint8_t *payload, size_t offset,
                                 uint32_t value);
static uint32_t uwb_distance_get_u32(const uint8_t *payload, size_t offset);
static void uwb_distance_put_u16(uint8_t *payload, size_t offset,
                                 uint16_t value);
static uint16_t uwb_distance_get_u16(const uint8_t *payload, size_t offset);
static void uwb_distance_put_i32(uint8_t *payload, size_t offset,
                                 int32_t value);
static int32_t uwb_distance_get_i32(const uint8_t *payload, size_t offset);
static void uwb_distance_build_frame(enum uwb_distance_frame_type type,
                                     uint8_t destination_id,
                                     uint16_t sequence,
                                     uint8_t payload[UWB_DW3000_PAYLOAD_LEN]);
static bool uwb_distance_destination_matches(uint8_t destination_id);
static esp_err_t uwb_dw3000_send_payload(const uint8_t *payload,
                                         size_t payload_len,
                                         uint64_t *tx_timestamp);

static uint8_t uwb_flex_tdoa_slot_initiator(uint32_t slot_id)
{
    const app_runtime_config_t *config = app_runtime_config_get();
    return config->flex_tdoa_slot_initiator_ids[
        slot_id % config->flex_tdoa_slot_count];
}

static void uwb_flex_tdoa_build_config(
    const app_runtime_config_t *config,
    uint8_t payload[UWB_DW3000_PAYLOAD_LEN])
{
    uwb_distance_build_frame(UWB_DISTANCE_FRAME_FLEX_TDOA_CONFIG,
                             UWB_DISTANCE_FRAME_BROADCAST_ID,
                             (uint16_t)config->flex_tdoa_config_generation,
                             payload);
    uwb_distance_put_u32(payload, UWB_FLEX_TDOA_CONFIG_GENERATION_OFFSET,
                         config->flex_tdoa_config_generation);
    payload[UWB_FLEX_TDOA_CONFIG_N_OFFSET] = config->anchor_count;
    payload[UWB_FLEX_TDOA_CONFIG_K_OFFSET] =
        config->flex_tdoa_responder_count;
    payload[UWB_FLEX_TDOA_CONFIG_M_OFFSET] = config->flex_tdoa_slot_count;
    memcpy(&payload[UWB_FLEX_TDOA_CONFIG_ANCHORS_OFFSET], config->anchor_ids,
           sizeof(config->anchor_ids));
    for (size_t slot = 0; slot < config->flex_tdoa_slot_count; ++slot) {
        uint8_t initiator_index = 0;
        for (size_t anchor = 0; anchor < config->anchor_count; ++anchor) {
            if (config->anchor_ids[anchor] ==
                config->flex_tdoa_slot_initiator_ids[slot]) {
                initiator_index = (uint8_t)anchor;
                break;
            }
        }
        const size_t byte_index = UWB_FLEX_TDOA_CONFIG_SLOTS_OFFSET + slot / 2U;
        const uint8_t shift = (uint8_t)((slot % 2U) * 4U);
        payload[byte_index] |= (uint8_t)(initiator_index << shift);
        for (size_t anchor = 0; anchor < config->anchor_count; ++anchor) {
            if ((config->flex_tdoa_slot_responder_masks[slot] &
                 (uint16_t)(1U << anchor)) == 0U) {
                continue;
            }
            const size_t bit_index = slot * config->anchor_count + anchor;
            payload[UWB_FLEX_TDOA_CONFIG_MASKS_OFFSET + bit_index / 8U] |=
                (uint8_t)(1U << (bit_index % 8U));
        }
    }
    uwb_distance_put_u16(payload, UWB_FLEX_TDOA_CONFIG_GUARD_US_OFFSET,
                         (uint16_t)config->flex_tdoa_guard_us);
    uwb_distance_put_u16(payload, UWB_FLEX_TDOA_CONFIG_REQ_US_OFFSET,
                         (uint16_t)config->flex_tdoa_request_subslot_us);
    uwb_distance_put_u16(payload,
                         UWB_FLEX_TDOA_CONFIG_REQ_PROCESS_US_OFFSET,
                         (uint16_t)config->flex_tdoa_request_process_us);
    uwb_distance_put_u16(payload, UWB_FLEX_TDOA_CONFIG_RESP_US_OFFSET,
                         (uint16_t)config->flex_tdoa_response_subslot_us);
    uwb_distance_put_u16(payload,
                         UWB_FLEX_TDOA_CONFIG_RESP_PROCESS_US_OFFSET,
                         (uint16_t)config->flex_tdoa_response_process_us);
}

static bool uwb_flex_tdoa_parse_config(
    const struct uwb_distance_frame *frame, app_runtime_config_t *parsed)
{
    if (frame == NULL || parsed == NULL ||
        frame->type != UWB_DISTANCE_FRAME_FLEX_TDOA_CONFIG ||
        frame->payload_len < UWB_FLEX_TDOA_CONFIG_LEN ||
        !uwb_distance_destination_matches(frame->destination_id)) {
        return false;
    }

    const app_runtime_config_t *current = app_runtime_config_get();
    *parsed = *current;
    parsed->flex_tdoa_config_generation = uwb_distance_get_u32(
        frame->payload, UWB_FLEX_TDOA_CONFIG_GENERATION_OFFSET);
    parsed->anchor_count = frame->payload[UWB_FLEX_TDOA_CONFIG_N_OFFSET];
    parsed->flex_tdoa_responder_count =
        frame->payload[UWB_FLEX_TDOA_CONFIG_K_OFFSET];
    parsed->flex_tdoa_slot_count =
        frame->payload[UWB_FLEX_TDOA_CONFIG_M_OFFSET];
    parsed->flex_tdoa_guard_us = uwb_distance_get_u16(
        frame->payload, UWB_FLEX_TDOA_CONFIG_GUARD_US_OFFSET);
    parsed->flex_tdoa_request_subslot_us = uwb_distance_get_u16(
        frame->payload, UWB_FLEX_TDOA_CONFIG_REQ_US_OFFSET);
    parsed->flex_tdoa_request_process_us = uwb_distance_get_u16(
        frame->payload, UWB_FLEX_TDOA_CONFIG_REQ_PROCESS_US_OFFSET);
    parsed->flex_tdoa_response_subslot_us = uwb_distance_get_u16(
        frame->payload, UWB_FLEX_TDOA_CONFIG_RESP_US_OFFSET);
    parsed->flex_tdoa_response_process_us = uwb_distance_get_u16(
        frame->payload, UWB_FLEX_TDOA_CONFIG_RESP_PROCESS_US_OFFSET);
    memcpy(parsed->anchor_ids,
           &frame->payload[UWB_FLEX_TDOA_CONFIG_ANCHORS_OFFSET],
           sizeof(parsed->anchor_ids));
    if (parsed->anchor_count != current->anchor_count ||
        memcmp(parsed->anchor_ids, current->anchor_ids,
               sizeof(parsed->anchor_ids)) != 0) {
        parsed->flex_tdoa_geometry_fixed = false;
        memset(parsed->flex_tdoa_anchor_x_mm, 0,
               sizeof(parsed->flex_tdoa_anchor_x_mm));
        memset(parsed->flex_tdoa_anchor_y_mm, 0,
               sizeof(parsed->flex_tdoa_anchor_y_mm));
    }
    memset(parsed->flex_tdoa_slot_initiator_ids, 0,
           sizeof(parsed->flex_tdoa_slot_initiator_ids));
    memset(parsed->flex_tdoa_slot_responder_masks, 0,
           sizeof(parsed->flex_tdoa_slot_responder_masks));
    if (parsed->anchor_count == 0U ||
        parsed->anchor_count > APP_RUNTIME_CONFIG_MAX_ANCHORS ||
        parsed->flex_tdoa_slot_count == 0U ||
        parsed->flex_tdoa_slot_count > APP_RUNTIME_CONFIG_FLEX_MAX_SLOTS) {
        return false;
    }
    for (size_t slot = 0; slot < parsed->flex_tdoa_slot_count; ++slot) {
        const uint8_t packed = frame->payload[
            UWB_FLEX_TDOA_CONFIG_SLOTS_OFFSET + slot / 2U];
        const uint8_t initiator_index =
            (uint8_t)((packed >> ((slot % 2U) * 4U)) & 0x0FU);
        if (initiator_index >= parsed->anchor_count) {
            return false;
        }
        parsed->flex_tdoa_slot_initiator_ids[slot] =
            parsed->anchor_ids[initiator_index];
        for (size_t anchor = 0; anchor < parsed->anchor_count; ++anchor) {
            const size_t bit_index = slot * parsed->anchor_count + anchor;
            if ((frame->payload[UWB_FLEX_TDOA_CONFIG_MASKS_OFFSET +
                                bit_index / 8U] &
                 (uint8_t)(1U << (bit_index % 8U))) != 0U) {
                parsed->flex_tdoa_slot_responder_masks[slot] |=
                    (uint16_t)(1U << anchor);
            }
        }
    }
    return parsed->flex_tdoa_config_generation != 0U &&
           app_runtime_config_validate(parsed);
}

static esp_err_t uwb_flex_tdoa_send_config(void)
{
    uint8_t payload[UWB_DW3000_PAYLOAD_LEN] = {0};
    uwb_flex_tdoa_build_config(app_runtime_config_get(), payload);
    return uwb_dw3000_send_payload(payload, UWB_FLEX_TDOA_CONFIG_LEN, NULL);
}

static esp_err_t uwb_flex_tdoa_send_geometry(size_t anchor_index)
{
    const app_runtime_config_t *config = app_runtime_config_get();
    uint8_t payload[UWB_DW3000_PAYLOAD_LEN] = {0};
    uwb_distance_build_frame(UWB_DISTANCE_FRAME_FLEX_TDOA_GEOMETRY,
                             UWB_DISTANCE_FRAME_BROADCAST_ID,
                             (uint16_t)config->flex_tdoa_geometry_generation,
                             payload);
    uwb_distance_put_u32(payload,
                         UWB_FLEX_TDOA_GEOMETRY_GENERATION_OFFSET,
                         config->flex_tdoa_geometry_generation);
    payload[UWB_FLEX_TDOA_GEOMETRY_FIXED_OFFSET] =
        config->flex_tdoa_geometry_fixed ? 1U : 0U;
    if (config->flex_tdoa_geometry_fixed) {
        if (anchor_index >= config->anchor_count) {
            return ESP_ERR_INVALID_ARG;
        }
        payload[UWB_FLEX_TDOA_GEOMETRY_COUNT_OFFSET] = config->anchor_count;
        payload[UWB_FLEX_TDOA_GEOMETRY_INDEX_OFFSET] = (uint8_t)anchor_index;
        payload[UWB_FLEX_TDOA_GEOMETRY_ANCHOR_ID_OFFSET] =
            config->anchor_ids[anchor_index];
        uwb_distance_put_i32(payload, UWB_FLEX_TDOA_GEOMETRY_X_MM_OFFSET,
                             config->flex_tdoa_anchor_x_mm[anchor_index]);
        uwb_distance_put_i32(payload, UWB_FLEX_TDOA_GEOMETRY_Y_MM_OFFSET,
                             config->flex_tdoa_anchor_y_mm[anchor_index]);
    }
    return uwb_dw3000_send_payload(payload, UWB_FLEX_TDOA_GEOMETRY_LEN,
                                   NULL);
}

static enum uwb_flex_tdoa_config_result
uwb_flex_tdoa_apply_geometry_frame(const struct uwb_distance_frame *frame)
{
    if (frame == NULL ||
        frame->type != UWB_DISTANCE_FRAME_FLEX_TDOA_GEOMETRY ||
        frame->payload_len < UWB_FLEX_TDOA_GEOMETRY_LEN ||
        !uwb_distance_destination_matches(frame->destination_id)) {
        return UWB_FLEX_TDOA_CONFIG_INVALID;
    }
    const uint32_t generation = uwb_distance_get_u32(
        frame->payload, UWB_FLEX_TDOA_GEOMETRY_GENERATION_OFFSET);
    const app_runtime_config_t *current = app_runtime_config_get();
    if (generation == 0U ||
        generation <= current->flex_tdoa_geometry_generation) {
        return UWB_FLEX_TDOA_CONFIG_CURRENT;
    }

    const bool fixed =
        frame->payload[UWB_FLEX_TDOA_GEOMETRY_FIXED_OFFSET] != 0U;
    app_runtime_config_t updated = *current;
    if (!fixed) {
        updated.flex_tdoa_geometry_fixed = false;
        updated.flex_tdoa_geometry_generation = generation;
        memset(updated.flex_tdoa_anchor_x_mm, 0,
               sizeof(updated.flex_tdoa_anchor_x_mm));
        memset(updated.flex_tdoa_anchor_y_mm, 0,
               sizeof(updated.flex_tdoa_anchor_y_mm));
    } else {
        const uint8_t count =
            frame->payload[UWB_FLEX_TDOA_GEOMETRY_COUNT_OFFSET];
        const uint8_t index =
            frame->payload[UWB_FLEX_TDOA_GEOMETRY_INDEX_OFFSET];
        const uint8_t anchor_id =
            frame->payload[UWB_FLEX_TDOA_GEOMETRY_ANCHOR_ID_OFFSET];
        if (count != current->anchor_count || index >= count ||
            anchor_id != current->anchor_ids[index]) {
            return UWB_FLEX_TDOA_CONFIG_INVALID;
        }
        if (s_flex_tdoa_geometry_staging.generation != generation ||
            s_flex_tdoa_geometry_staging.anchor_count != count) {
            memset(&s_flex_tdoa_geometry_staging, 0,
                   sizeof(s_flex_tdoa_geometry_staging));
            s_flex_tdoa_geometry_staging.generation = generation;
            s_flex_tdoa_geometry_staging.anchor_count = count;
        }
        s_flex_tdoa_geometry_staging.anchor_x_mm[index] =
            uwb_distance_get_i32(frame->payload,
                                 UWB_FLEX_TDOA_GEOMETRY_X_MM_OFFSET);
        s_flex_tdoa_geometry_staging.anchor_y_mm[index] =
            uwb_distance_get_i32(frame->payload,
                                 UWB_FLEX_TDOA_GEOMETRY_Y_MM_OFFSET);
        s_flex_tdoa_geometry_staging.received_mask |=
            (uint16_t)(1U << index);
        const uint16_t complete_mask = (uint16_t)((1U << count) - 1U);
        if (s_flex_tdoa_geometry_staging.received_mask != complete_mask) {
            return UWB_FLEX_TDOA_CONFIG_CURRENT;
        }
        updated.flex_tdoa_geometry_fixed = true;
        updated.flex_tdoa_geometry_generation = generation;
        memcpy(updated.flex_tdoa_anchor_x_mm,
               s_flex_tdoa_geometry_staging.anchor_x_mm,
               sizeof(updated.flex_tdoa_anchor_x_mm));
        memcpy(updated.flex_tdoa_anchor_y_mm,
               s_flex_tdoa_geometry_staging.anchor_y_mm,
               sizeof(updated.flex_tdoa_anchor_y_mm));
    }

    const esp_err_t err = app_runtime_config_save(&updated);
    if (err != ESP_OK) {
        ESP_LOGW(TAG, "FlexTDOA geometry save failed generation=%lu: %s",
                 (unsigned long)generation, esp_err_to_name(err));
        return UWB_FLEX_TDOA_CONFIG_INVALID;
    }
    (void)uwb_flex_tdoa_runtime_reload_geometry();
    ESP_LOGI(TAG,
             "FlexTDOA geometry applied source=%u generation=%lu fixed=%u",
             (unsigned)frame->source_id, (unsigned long)generation,
             fixed ? 1U : 0U);
    return UWB_FLEX_TDOA_CONFIG_UPDATED;
}

static enum uwb_flex_tdoa_config_result uwb_flex_tdoa_apply_config_frame(
    const struct uwb_distance_frame *frame)
{
    app_runtime_config_t received = {0};
    if (!uwb_flex_tdoa_parse_config(frame, &received)) {
        return UWB_FLEX_TDOA_CONFIG_INVALID;
    }

    const app_runtime_config_t *current = app_runtime_config_get();
    if (received.flex_tdoa_config_generation <=
        current->flex_tdoa_config_generation) {
        return UWB_FLEX_TDOA_CONFIG_CURRENT;
    }
    const esp_err_t err = app_runtime_config_save(&received);
    if (err != ESP_OK) {
        ESP_LOGW(TAG, "FlexTDOA radio config save failed generation=%lu: %s",
                 (unsigned long)received.flex_tdoa_config_generation,
                 esp_err_to_name(err));
        return UWB_FLEX_TDOA_CONFIG_INVALID;
    }
    ESP_LOGI(TAG,
             "FlexTDOA radio config applied source=%u generation=%lu N=%u K=%u M=%u",
             (unsigned)frame->source_id,
             (unsigned long)received.flex_tdoa_config_generation,
             (unsigned)received.anchor_count,
             (unsigned)received.flex_tdoa_responder_count,
             (unsigned)received.flex_tdoa_slot_count);
    return UWB_FLEX_TDOA_CONFIG_UPDATED;
}

static bool uwb_flex_tdoa_handle_runtime_config(
    const struct uwb_distance_frame *frame)
{
    if (frame == NULL) {
        return false;
    }

    if (frame->type == UWB_DISTANCE_FRAME_FLEX_TDOA_GEOMETRY) {
        return uwb_flex_tdoa_apply_geometry_frame(frame) !=
               UWB_FLEX_TDOA_CONFIG_INVALID;
    }
    if (frame->type != UWB_DISTANCE_FRAME_FLEX_TDOA_CONFIG) {
        return false;
    }

    const enum uwb_flex_tdoa_config_result result =
        uwb_flex_tdoa_apply_config_frame(frame);
    if (result == UWB_FLEX_TDOA_CONFIG_UPDATED) {
        ESP_LOGW(TAG,
                 "FlexTDOA schedule changed over UWB; restarting to rebuild local state");
        vTaskDelay(pdMS_TO_TICKS(50));
        esp_restart();
    }
    return result != UWB_FLEX_TDOA_CONFIG_INVALID;
}

static uint32_t uwb_dw3000_remaining_ms(int64_t start_us,
                                        uint32_t timeout_ms);
static esp_err_t uwb_dw3000_send_payload(const uint8_t *payload,
                                         size_t payload_len,
                                         uint64_t *tx_timestamp);
static esp_err_t uwb_dw3000_send_payload_expect_rx(
    const uint8_t *payload, size_t payload_len, uint32_t rx_after_tx_delay_uus,
    uint32_t rx_timeout_ms, uint64_t *tx_timestamp);
static esp_err_t uwb_dw3000_send_payload_delayed(
    const uint8_t *payload, size_t payload_len, uint64_t tx_timestamp,
    uint64_t *programmed_tx_timestamp, uint64_t *actual_tx_timestamp);
static esp_err_t uwb_dw3000_send_payload_delayed_timeout(
    const uint8_t *payload, size_t payload_len, uint64_t tx_timestamp,
    uint32_t tx_timeout_ms, uint64_t *programmed_tx_timestamp,
    uint64_t *actual_tx_timestamp);
static esp_err_t uwb_dw3000_send_payload_delayed_expect_rx(
    const uint8_t *payload, size_t payload_len, uint64_t tx_timestamp,
    uint32_t rx_after_tx_delay_uus, uint32_t rx_timeout_ms,
    uint64_t *programmed_tx_timestamp, uint64_t *actual_tx_timestamp);
static esp_err_t uwb_dw3000_update_u32(uint8_t base, uint8_t sub,
                                       uint32_t clear_mask,
                                       uint32_t set_mask);
static esp_err_t uwb_dw3000_fast_command(uint8_t command);
static esp_err_t uwb_dw3000_clear_status(void);
static esp_err_t uwb_flex_tdoa_extend_rx_timestamp32(
    uint32_t low32, uint64_t *timestamp);
static void uwb_flex_tdoa_log_anchor_result(
    uint8_t initiator_id, uint8_t responder_id, uint16_t sequence,
    uint32_t slot_id, double distance_m, double raw_distance_m);
static void uwb_distance_fill_tag_measurement(
    uint8_t peer_id, uint16_t sequence, uint64_t poll_tx_ts,
    const struct uwb_distance_frame *response, uint64_t final_tx_ts,
    const struct uwb_distance_frame *report2,
    struct uwb_distance_measurement *measurement);
static void
uwb_distance_log_tag_verification(const struct uwb_distance_measurement *measurement,
                                  const struct uwb_distance_frame *report2);

#define DW3000_PMSC_STATE_IDLE 0x03

static spi_device_handle_t s_spi;
static uint32_t s_spi_clock_hz;
static uint32_t s_tx_fctrl_base;
static bool s_tx_fctrl_base_valid;
static size_t s_tx_fctrl_payload_len = SIZE_MAX;
static bool s_rx_double_buffer_enabled;
static uint8_t s_rx_double_buffer_index;
static bool s_flex_tdoa_anchor_request_buffer_pending;
static uint32_t s_rx_double_buffer_resync_count;
static bool s_flex_tdoa_rx_timestamp_reference_valid;
static uint64_t s_flex_tdoa_rx_timestamp_reference;
static int64_t s_flex_tdoa_rx_timestamp_reference_host_us;
static bool s_started;
static bool s_rx_armed;
static bool s_irq_enabled;
static TaskHandle_t s_task_handle;
static uint8_t s_source_id;
static uint32_t s_device_id;
static enum uwb_dw3000_runtime_mode s_runtime_mode =
    UWB_DW3000_RUNTIME_BEACON_SMOKE;
static volatile enum uwb_dw3000_runtime_mode s_requested_runtime_mode =
    UWB_DW3000_RUNTIME_BEACON_SMOKE;
static volatile uint32_t s_runtime_switch_request_generation;
static volatile uint32_t s_runtime_switch_applied_generation;
static volatile bool s_runtime_switch_active;
static volatile bool s_runtime_hot_entry;
static volatile uint32_t s_runtime_switch_count;
static volatile uint32_t s_last_runtime_switch_ms;
static volatile enum uwb_dw3000_status s_status = UWB_DW3000_STATUS_IDLE;
static volatile uint32_t s_tx_count;
static volatile uint32_t s_tx_error_count;
static volatile uint32_t s_rx_count;
static volatile uint32_t s_rx_error_count;
static volatile uint32_t s_rx_ignored_count;
static volatile uint32_t s_native_ds_rx_timestamp_cia_invalid_count;
static volatile uint32_t s_native_ds_rx_phy_error_count;
static volatile uint32_t s_native_ds_rx_frame_sync_loss_count;
static volatile uint32_t s_native_ds_rx_phr_error_count;
static volatile uint32_t s_native_ds_rx_fcs_error_count;
static volatile uint32_t s_native_ds_rx_overrun_count;
static volatile uint32_t s_native_ds_rx_cia_error_count;
static volatile uint32_t s_native_ds_rx_filter_rejection_count;
static uint32_t s_passive_ds_rx_errors_since_summary;
static uint32_t s_passive_ds_rx_error_status_since_summary;
static volatile uint32_t s_native_ds_rx_cp_error_count;
static volatile uint8_t s_last_rx_source_id;
static volatile uint32_t s_last_rx_sequence;
static uint16_t s_antenna_delay = APP_UWB_ANTENNA_DELAY_DEFAULT;
static gptimer_handle_t s_calibration_timer;
static volatile bool s_calibration_timer_running;
static volatile bool s_calibration_timer_irq_armed;
static volatile bool s_calibration_timer_irq_started;
static volatile bool s_calibration_timer_start_on_tx_done;
static volatile TaskHandle_t s_calibration_timer_wait_task;
// These buffers live for the complete FlexTDOA runtime. Keeping them out of
// the UWB task stack avoids making the maximum N configuration consume nearly
// the entire 8 KiB real-time stack on entry to the tag/anchor loops.
static struct uwb_flex_tdoa_observation
    s_flex_tdoa_tag_observations[UWB_FLEX_TDOA_MAX_OBSERVATIONS];
static struct flextdoa_cfo_estimator s_flex_tdoa_cfo_estimator;
static struct flextdoa_slot_collection s_flex_tdoa_tag_collection;
static struct uwb_flex_tdoa_local_request s_flex_tdoa_local_request;
static struct uwb_mobile_geometry s_flex_tdoa_mobile_geometry;
static esp_timer_handle_t s_flex_tdoa_schedule_timer;
static volatile bool s_flex_tdoa_schedule_alarm_fired;
static esp_timer_handle_t s_passive_ds_schedule_timer;
static volatile bool s_passive_ds_schedule_alarm_fired;
static uint32_t s_flex_tdoa_observations_since_summary;
static uint32_t s_flex_tdoa_observation_drops_since_summary;
static uint32_t s_flex_tdoa_observation_invalid_since_summary;
static uint32_t s_flex_tdoa_observation_invalid_age_since_summary;
static uint32_t s_flex_tdoa_observation_invalid_cfo_since_summary;
static uint32_t s_flex_tdoa_observation_invalid_order_since_summary;
static uint32_t s_flex_tdoa_complete_slots_since_summary;
static uint32_t s_flex_tdoa_incomplete_slots_since_summary;
static bool s_flex_tdoa_tag_request_slot_valid;
static uint32_t s_flex_tdoa_tag_last_request_slot_id;
static uint32_t s_flex_tdoa_missed_requests_since_summary;
static uint32_t s_flex_tdoa_observation_invalid_age_index_since_summary[
    UWB_ANCHOR_SURVEY_MAX_ANCHORS - 1U];
static TickType_t s_flex_tdoa_observation_summary_tick;
static uint32_t s_flex_tdoa_anchor_results_since_summary;
static uint32_t s_flex_tdoa_anchor_drops_since_summary;
static uint32_t s_flex_tdoa_anchor_incoherent_since_summary;
static uint32_t s_flex_tdoa_anchor_index_since_summary[
    UWB_ANCHOR_SURVEY_MAX_ANCHORS - 1U];
static uint32_t s_flex_tdoa_tag_requests_by_anchor[
    UWB_ANCHOR_SURVEY_MAX_ANCHORS];
static uint32_t s_flex_tdoa_tag_responses_by_anchor[
    UWB_ANCHOR_SURVEY_MAX_ANCHORS];
static uint32_t s_flex_tdoa_response_tx_by_initiator[
    UWB_ANCHOR_SURVEY_MAX_ANCHORS];
static TickType_t s_flex_tdoa_anchor_summary_tick;
static uint32_t s_flex_tdoa_rx_errors_since_summary;
static uint32_t s_flex_tdoa_rx_error_status_since_summary;
static uint32_t s_last_delayed_arm_us;

static bool uwb_dw3000_runtime_from_app_mode(
    uint8_t app_runtime_mode, enum uwb_dw3000_runtime_mode *runtime_mode)
{
    if (runtime_mode == NULL) {
        return false;
    }
    switch (app_runtime_mode) {
    case APP_RUNTIME_MODE_UWB_RANGING:
        *runtime_mode = UWB_DW3000_RUNTIME_RANGING;
        return true;
    case APP_RUNTIME_MODE_UWB_FLEX_TDOA:
        *runtime_mode = UWB_DW3000_RUNTIME_FLEX_TDOA;
        return true;
    case APP_RUNTIME_MODE_UWB_PASSIVE_DS_TWR:
        *runtime_mode = UWB_DW3000_RUNTIME_PASSIVE_DS_TWR;
        return true;
    default:
        return false;
    }
}

static bool uwb_dw3000_runtime_mode_hot_switchable(
    enum uwb_dw3000_runtime_mode runtime_mode)
{
    return runtime_mode == UWB_DW3000_RUNTIME_RANGING ||
           runtime_mode == UWB_DW3000_RUNTIME_FLEX_TDOA ||
           runtime_mode == UWB_DW3000_RUNTIME_PASSIVE_DS_TWR;
}

static bool uwb_dw3000_runtime_switch_pending(void)
{
    return s_runtime_switch_request_generation !=
           s_runtime_switch_applied_generation;
}

static bool uwb_local_is_configured_anchor(void)
{
    const app_runtime_config_t *config = app_runtime_config_get();
    for (size_t i = 0; i < config->anchor_count; ++i) {
        if (config->anchor_ids[i] == s_source_id) {
            return true;
        }
    }
    return false;
}

static bool uwb_passive_ds_multi_local_is_receive_only_tag(void)
{
    const app_runtime_config_t *config = app_runtime_config_get();
    return s_runtime_mode == UWB_DW3000_RUNTIME_PASSIVE_DS_TWR &&
           config != NULL &&
           !uwb_local_is_configured_anchor();
}

static bool uwb_dw3000_runtime_uses_high_rate_rx_buffer(
    enum uwb_dw3000_runtime_mode runtime_mode)
{
    if (runtime_mode == UWB_DW3000_RUNTIME_FLEX_TDOA) {
        return true;
    }
    return runtime_mode == UWB_DW3000_RUNTIME_PASSIVE_DS_TWR &&
           uwb_passive_ds_multi_local_is_receive_only_tag();
}

static void uwb_flex_tdoa_schedule_alarm_callback(void *arg)
{
    (void)arg;
    s_flex_tdoa_schedule_alarm_fired = true;
    if (s_task_handle != NULL) {
        xTaskNotifyGive(s_task_handle);
    }
}

static void uwb_passive_ds_schedule_alarm_callback(void *arg)
{
    (void)arg;
    s_passive_ds_schedule_alarm_fired = true;
    if (s_task_handle != NULL) {
        xTaskNotifyGive(s_task_handle);
    }
}

static void uwb_passive_ds_record_stage(
    enum uwb_passive_ds_runtime_stage stage, int64_t start_host_us,
    bool success)
{
    uwb_passive_ds_runtime_record_stage(
        stage, start_host_us, esp_timer_get_time(), success);
}

static bool IRAM_ATTR uwb_calibration_timer_alarm_callback(
    gptimer_handle_t timer, const gptimer_alarm_event_data_t *edata,
    void *user_ctx)
{
    (void)timer;
    (void)edata;
    (void)user_ctx;

    BaseType_t higher_priority_task_woken = pdFALSE;
    TaskHandle_t task = s_calibration_timer_wait_task;
    if (task != NULL) {
        vTaskNotifyGiveFromISR(task, &higher_priority_task_woken);
    }
    return higher_priority_task_woken == pdTRUE;
}

static int gpio_level_active(int active_high)
{
    return active_high ? 1 : 0;
}

static int gpio_level_inactive(int active_high)
{
    return active_high ? 0 : 1;
}

static uint8_t uwb_dw3000_runtime_radio_channel(void)
{
    const app_runtime_config_t *config = app_runtime_config_get();
    return config->radio_channel == 9U ? 9U : 5U;
}

static uint8_t uwb_dw3000_runtime_radio_rf_channel_bit(void)
{
    return uwb_dw3000_runtime_radio_channel() == 9U ? 1U : 0U;
}

static uint8_t uwb_dw3000_runtime_radio_phy_mode(void)
{
    const app_runtime_config_t *config = app_runtime_config_get();
    switch (config->radio_phy_mode) {
    case APP_UWB_RADIO_PHY_LONG_RANGE:
    case APP_UWB_RADIO_PHY_FAST_PLEN256:
    case APP_UWB_RADIO_PHY_FAST_PLEN512:
    case APP_UWB_RADIO_PHY_850K_PLEN512:
    case APP_UWB_RADIO_PHY_850K_PLEN512_STD_SFD:
        return config->radio_phy_mode;
    default:
        return APP_UWB_RADIO_PHY_FAST;
    }
}

static bool uwb_dw3000_runtime_radio_is_850k(void)
{
    const uint8_t mode = uwb_dw3000_runtime_radio_phy_mode();
    return mode == APP_UWB_RADIO_PHY_LONG_RANGE ||
           mode == APP_UWB_RADIO_PHY_850K_PLEN512 ||
           mode == APP_UWB_RADIO_PHY_850K_PLEN512_STD_SFD;
}

static uint8_t uwb_dw3000_runtime_radio_profile(void)
{
    const uint8_t mode = uwb_dw3000_runtime_radio_phy_mode();
    if (mode == APP_UWB_RADIO_PHY_LONG_RANGE) {
        return uwb_dw3000_runtime_radio_channel() == 9U
                   ? APP_UWB_RADIO_PROFILE_LONG_RANGE_CH9_850K_PLEN1024
                   : APP_UWB_RADIO_PROFILE_LONG_RANGE_CH5_850K_PLEN1024;
    }
    if (mode == APP_UWB_RADIO_PHY_FAST_PLEN256) {
        return uwb_dw3000_runtime_radio_channel() == 9U
                   ? APP_UWB_RADIO_PROFILE_CH9_6M8_PLEN256
                   : APP_UWB_RADIO_PROFILE_CH5_6M8_PLEN256;
    }
    if (mode == APP_UWB_RADIO_PHY_FAST_PLEN512) {
        return uwb_dw3000_runtime_radio_channel() == 9U
                   ? APP_UWB_RADIO_PROFILE_CH9_6M8_PLEN512
                   : APP_UWB_RADIO_PROFILE_CH5_6M8_PLEN512;
    }
    if (mode == APP_UWB_RADIO_PHY_850K_PLEN512) {
        return uwb_dw3000_runtime_radio_channel() == 9U
                   ? APP_UWB_RADIO_PROFILE_CH9_850K_PLEN512
                   : APP_UWB_RADIO_PROFILE_CH5_850K_PLEN512;
    }
    if (mode == APP_UWB_RADIO_PHY_850K_PLEN512_STD_SFD) {
        return uwb_dw3000_runtime_radio_channel() == 9U
                   ? APP_UWB_RADIO_PROFILE_CH9_850K_PLEN512_STD_SFD
                   : APP_UWB_RADIO_PROFILE_CH5_850K_PLEN512_STD_SFD;
    }
    return uwb_dw3000_runtime_radio_channel() == 9U
               ? APP_UWB_RADIO_PROFILE_LEGACY_CH9_6M8_PLEN128
               : APP_UWB_RADIO_PROFILE_LEGACY_CH5_6M8_PLEN128;
}

static uint8_t uwb_dw3000_runtime_radio_preamble_len_code(void)
{
    switch (uwb_dw3000_runtime_radio_phy_mode()) {
    case APP_UWB_RADIO_PHY_LONG_RANGE:
        return APP_UWB_RADIO_PLEN_1024;
    case APP_UWB_RADIO_PHY_FAST_PLEN256:
        return APP_UWB_RADIO_PLEN_256;
    case APP_UWB_RADIO_PHY_FAST_PLEN512:
    case APP_UWB_RADIO_PHY_850K_PLEN512:
    case APP_UWB_RADIO_PHY_850K_PLEN512_STD_SFD:
        return APP_UWB_RADIO_PLEN_512;
    default:
        return APP_UWB_RADIO_PREAMBLE_LEN_CODE;
    }
}

static uint8_t uwb_dw3000_runtime_radio_preamble_code(void)
{
    return uwb_dw3000_runtime_radio_phy_mode() ==
                   APP_UWB_RADIO_PHY_850K_PLEN512_STD_SFD
               ? 9U
               : APP_UWB_RADIO_PREAMBLE_CODE;
}

static uint8_t uwb_dw3000_runtime_radio_pac(void)
{
    const uint8_t mode = uwb_dw3000_runtime_radio_phy_mode();
    if (mode == APP_UWB_RADIO_PHY_FAST_PLEN256) {
        return 1U; /* DWT_PAC16 */
    }
    if (mode == APP_UWB_RADIO_PHY_LONG_RANGE ||
        mode == APP_UWB_RADIO_PHY_FAST_PLEN512 ||
        mode == APP_UWB_RADIO_PHY_850K_PLEN512 ||
        mode == APP_UWB_RADIO_PHY_850K_PLEN512_STD_SFD) {
        return 2U; /* DWT_PAC32 */
    }
    return APP_UWB_RADIO_PAC;
}

static uint8_t uwb_dw3000_runtime_radio_data_rate(void)
{
    return uwb_dw3000_runtime_radio_is_850k()
               ? APP_UWB_RADIO_BR_850K
               : APP_UWB_RADIO_DATA_RATE;
}

static uint8_t uwb_dw3000_runtime_radio_phr_rate(void)
{
    return uwb_dw3000_runtime_radio_is_850k()
               ? 0U
               : APP_UWB_RADIO_PHR_RATE;
}

static uint16_t uwb_dw3000_runtime_radio_sfd_timeout(void)
{
    /* plen + 1 + 8-symbol Qorvo SFD - PAC. */
    switch (uwb_dw3000_runtime_radio_phy_mode()) {
    case APP_UWB_RADIO_PHY_LONG_RANGE:
        return 1001U;
    case APP_UWB_RADIO_PHY_FAST_PLEN256:
        return 249U;
    case APP_UWB_RADIO_PHY_FAST_PLEN512:
    case APP_UWB_RADIO_PHY_850K_PLEN512:
    case APP_UWB_RADIO_PHY_850K_PLEN512_STD_SFD:
        return 489U;
    default:
        return 129U;
    }
}

static uint8_t uwb_dw3000_runtime_radio_sfd_type(void)
{
    return uwb_dw3000_runtime_radio_phy_mode() ==
                   APP_UWB_RADIO_PHY_850K_PLEN512_STD_SFD
               ? 0U
               : APP_UWB_RADIO_SFD_TYPE;
}

static uint32_t uwb_dw3000_runtime_rf_tx_ctrl_2(void)
{
    return uwb_dw3000_runtime_radio_channel() == 9U
               ? APP_UWB_RADIO_RF_TX_CTRL_2_CH9
               : APP_UWB_RADIO_RF_TX_CTRL_2_CH5;
}

static uint32_t uwb_dw3000_runtime_pll_cfg_final(void)
{
    return uwb_dw3000_runtime_radio_channel() == 9U
               ? APP_UWB_RADIO_PLL_CFG_FINAL_CH9
               : APP_UWB_RADIO_PLL_CFG_FINAL_CH5;
}

static uint32_t uwb_dw3000_runtime_dgc_lut(size_t index)
{
    static const uint32_t ch5[] = {
        APP_UWB_DGC_LUT_CH5_0, APP_UWB_DGC_LUT_CH5_1,
        APP_UWB_DGC_LUT_CH5_2, APP_UWB_DGC_LUT_CH5_3,
        APP_UWB_DGC_LUT_CH5_4, APP_UWB_DGC_LUT_CH5_5,
        APP_UWB_DGC_LUT_CH5_6,
    };
    static const uint32_t ch9[] = {
        APP_UWB_DGC_LUT_CH9_0, APP_UWB_DGC_LUT_CH9_1,
        APP_UWB_DGC_LUT_CH9_2, APP_UWB_DGC_LUT_CH9_3,
        APP_UWB_DGC_LUT_CH9_4, APP_UWB_DGC_LUT_CH9_5,
        APP_UWB_DGC_LUT_CH9_6,
    };
    const uint32_t *lut =
        uwb_dw3000_runtime_radio_channel() == 9U ? ch9 : ch5;
    return index < 7U ? lut[index] : lut[0];
}

static void uwb_dw3000_delay_ms(uint32_t delay_ms)
{
    TickType_t ticks = pdMS_TO_TICKS(delay_ms);
    if (ticks == 0) {
        ticks = 1;
    }
    vTaskDelay(ticks);
}

static esp_err_t uwb_calibration_timer_init(void)
{
    if (s_calibration_timer != NULL) {
        return ESP_OK;
    }

    const gptimer_config_t timer_config = {
        .clk_src = GPTIMER_CLK_SRC_DEFAULT,
        .direction = GPTIMER_COUNT_UP,
        .resolution_hz = 1000000U,
    };

    esp_err_t err = gptimer_new_timer(&timer_config,
                                      &s_calibration_timer);
    if (err != ESP_OK) {
        ESP_LOGE(TAG, "calibration timer create failed: %s",
                 esp_err_to_name(err));
        return err;
    }
    const gptimer_event_callbacks_t callbacks = {
        .on_alarm = uwb_calibration_timer_alarm_callback,
    };
    err = gptimer_register_event_callbacks(
        s_calibration_timer, &callbacks, NULL);
    if (err != ESP_OK) {
        ESP_LOGE(TAG, "calibration timer callback register failed: %s",
                 esp_err_to_name(err));
        goto fail_delete;
    }
    err = gptimer_enable(s_calibration_timer);
    if (err != ESP_OK) {
        ESP_LOGE(TAG, "calibration timer enable failed: %s",
                 esp_err_to_name(err));
        goto fail_delete;
    }
    err = gptimer_set_raw_count(s_calibration_timer, 0);
    if (err != ESP_OK) {
        ESP_LOGE(TAG, "calibration timer initial clear failed: %s",
                 esp_err_to_name(err));
        (void)gptimer_disable(s_calibration_timer);
        goto fail_delete;
    }

    s_calibration_timer_running = false;
    s_calibration_timer_irq_armed = false;
    s_calibration_timer_irq_started = false;
    s_calibration_timer_start_on_tx_done = false;
    s_calibration_timer_wait_task = NULL;
    ESP_LOGI(TAG, "UWB calibration timer ready at 1 MHz");
    return ESP_OK;

fail_delete:
    (void)gptimer_del_timer(s_calibration_timer);
    s_calibration_timer = NULL;
    s_calibration_timer_running = false;
    s_calibration_timer_irq_armed = false;
    s_calibration_timer_irq_started = false;
    s_calibration_timer_start_on_tx_done = false;
    s_calibration_timer_wait_task = NULL;
    return err;
}

static esp_err_t uwb_calibration_timer_stop_if_running(void)
{
    if (s_calibration_timer == NULL || !s_calibration_timer_running) {
        return ESP_OK;
    }

    const esp_err_t err = gptimer_stop(s_calibration_timer);
    if (err != ESP_OK && err != ESP_ERR_INVALID_STATE) {
        return err;
    }
    s_calibration_timer_running = false;
    return ESP_OK;
}

static esp_err_t uwb_calibration_timer_reset(void)
{
    ESP_RETURN_ON_ERROR(uwb_calibration_timer_init(), TAG,
                        "calibration timer init failed");
    ESP_RETURN_ON_ERROR(uwb_calibration_timer_stop_if_running(), TAG,
                        "calibration timer stop failed");

    s_calibration_timer_irq_armed = false;
    s_calibration_timer_irq_started = false;
    s_calibration_timer_start_on_tx_done = false;
    s_calibration_timer_wait_task = NULL;
    ESP_RETURN_ON_ERROR(gptimer_set_alarm_action(s_calibration_timer, NULL),
                        TAG, "calibration timer alarm disable failed");
    ESP_RETURN_ON_ERROR(gptimer_set_raw_count(s_calibration_timer, 0), TAG,
                        "calibration timer count clear failed");
    return ESP_OK;
}

static esp_err_t uwb_calibration_timer_start(void)
{
    ESP_RETURN_ON_ERROR(uwb_calibration_timer_init(), TAG,
                        "calibration timer init failed");
    if (s_calibration_timer_running) {
        return ESP_OK;
    }

    const esp_err_t err = gptimer_start(s_calibration_timer);
    if (err != ESP_OK) {
        return err;
    }
    s_calibration_timer_running = true;
    return ESP_OK;
}

static void IRAM_ATTR uwb_calibration_timer_start_from_isr(void)
{
    if (!s_calibration_timer_irq_armed || s_calibration_timer_irq_started ||
        s_calibration_timer == NULL) {
        return;
    }

    if (gptimer_start(s_calibration_timer) == ESP_OK) {
        s_calibration_timer_running = true;
        s_calibration_timer_irq_started = true;
        s_calibration_timer_irq_armed = false;
    }
}

static esp_err_t uwb_calibration_timer_arm_rx_irq_start(void)
{
    ESP_RETURN_ON_ERROR(uwb_calibration_timer_reset(), TAG,
                        "calibration timer reset before RX sync failed");
    s_calibration_timer_irq_armed = s_irq_enabled;
    return ESP_OK;
}

static esp_err_t uwb_calibration_timer_arm_tx_irq_start(void)
{
    ESP_RETURN_ON_ERROR(uwb_calibration_timer_reset(), TAG,
                        "calibration timer reset before TX sync failed");
    s_calibration_timer_start_on_tx_done = true;
    s_calibration_timer_irq_armed = s_irq_enabled;
    return ESP_OK;
}

static esp_err_t uwb_calibration_timer_accept_rx_sync(void)
{
    s_calibration_timer_irq_armed = false;
    if (!s_calibration_timer_irq_started) {
        ESP_RETURN_ON_ERROR(uwb_calibration_timer_start(), TAG,
                            "calibration timer RX fallback start failed");
    }
    return ESP_OK;
}

static esp_err_t uwb_calibration_timer_accept_tx_sync(void)
{
    if (!s_calibration_timer_start_on_tx_done) {
        return ESP_OK;
    }

    s_calibration_timer_start_on_tx_done = false;
    s_calibration_timer_irq_armed = false;
    if (!s_calibration_timer_irq_started) {
        ESP_RETURN_ON_ERROR(uwb_calibration_timer_start(), TAG,
                            "calibration timer TX fallback start failed");
    }
    return ESP_OK;
}

static esp_err_t uwb_calibration_timer_get_us(uint64_t *time_us)
{
    if (time_us == NULL) {
        return ESP_ERR_INVALID_ARG;
    }
    ESP_RETURN_ON_ERROR(uwb_calibration_timer_init(), TAG,
                        "calibration timer init failed");
    return gptimer_get_raw_count(s_calibration_timer, time_us);
}

static void uwb_calibration_timer_wait_until_us(uint32_t target_us)
{
    while (true) {
        uint64_t now_us = 0;
        if (uwb_calibration_timer_get_us(&now_us) != ESP_OK ||
            now_us >= target_us) {
            s_calibration_timer_wait_task = NULL;
            return;
        }

        const uint32_t remaining_us = target_us - (uint32_t)now_us;
        if (!s_calibration_timer_running) {
            ESP_LOGW(TAG,
                     "calibration timer wait requested while timer is stopped");
            return;
        }

        const gptimer_alarm_config_t alarm_config = {
            .alarm_count = target_us,
            .reload_count = 0,
            .flags = {
                .auto_reload_on_alarm = false,
            },
        };
        s_calibration_timer_wait_task = xTaskGetCurrentTaskHandle();
        if (gptimer_set_alarm_action(s_calibration_timer, &alarm_config) !=
            ESP_OK) {
            s_calibration_timer_wait_task = NULL;
            vTaskDelay(1);
            continue;
        }

        if (uwb_calibration_timer_get_us(&now_us) != ESP_OK ||
            now_us >= target_us) {
            (void)gptimer_set_alarm_action(s_calibration_timer, NULL);
            s_calibration_timer_wait_task = NULL;
            return;
        }

        TickType_t ticks =
            pdMS_TO_TICKS((remaining_us + 999U) / 1000U);
        if (ticks == 0) {
            ticks = 1;
        }
        (void)ulTaskNotifyTake(pdTRUE, ticks);
        (void)gptimer_set_alarm_action(s_calibration_timer, NULL);
        s_calibration_timer_wait_task = NULL;
    }
}

static void IRAM_ATTR uwb_dw3000_irq_isr_handler(void *arg)
{
    (void)arg;
    uwb_calibration_timer_start_from_isr();
    BaseType_t higher_priority_task_woken = pdFALSE;
    if (s_task_handle != NULL) {
        vTaskNotifyGiveFromISR(s_task_handle, &higher_priority_task_woken);
    }
    if (higher_priority_task_woken == pdTRUE) {
        portYIELD_FROM_ISR();
    }
}

static void uwb_dw3000_wait_for_event_or_delay(int64_t start_us,
                                               uint32_t timeout_ms,
                                               uint32_t fallback_delay_ms)
{
#if APP_UWB_IRQ_ENABLED
    if (s_irq_enabled) {
        const uint32_t remaining_ms =
            uwb_dw3000_remaining_ms(start_us, timeout_ms);
        if (remaining_ms == 0) {
            return;
        }

        TickType_t ticks = pdMS_TO_TICKS(remaining_ms);
        if (ticks == 0) {
            ticks = 1;
        }
        (void)ulTaskNotifyTake(pdTRUE, ticks);
        return;
    }
#else
    (void)start_tick;
    (void)timeout_ms;
#endif

    uwb_dw3000_delay_ms(fallback_delay_ms);
}

static bool uwb_dw3000_device_id_valid(uint32_t device_id)
{
    return device_id == DW3000_DEV_ID_DW3000 ||
           device_id == DW3000_DEV_ID_DW3120;
}

static uint8_t uwb_dw3000_pick_source_id(void)
{
    if (APP_UWB_SOURCE_ID > 0 && APP_UWB_SOURCE_ID <= 255) {
        return (uint8_t)APP_UWB_SOURCE_ID;
    }

    if (app_identity_init() == ESP_OK) {
        const uint8_t module_id = app_identity_get_module_id();
        if (module_id != 0) {
            return module_id;
        }
    }

    uint8_t mac[6] = {0};
    if (esp_read_mac(mac, ESP_MAC_WIFI_STA) == ESP_OK && mac[5] != 0) {
        return mac[5];
    }

    const uint8_t random_id = (uint8_t)(esp_random() & 0xFFU);
    return random_id != 0 ? random_id : 1;
}

static esp_err_t uwb_dw3000_configure_gpio(void)
{
    const uint64_t output_pin_mask =
        (1ULL << BOARD_CONFIG_UWB_CS_GPIO) |
        (1ULL << BOARD_CONFIG_UWB_WAKEUP_GPIO) |
        (1ULL << BOARD_CONFIG_UWB_RST_GPIO);

    const gpio_config_t output_config = {
        .pin_bit_mask = output_pin_mask,
        .mode = GPIO_MODE_OUTPUT,
        .pull_up_en = GPIO_PULLUP_DISABLE,
        .pull_down_en = GPIO_PULLDOWN_DISABLE,
        .intr_type = GPIO_INTR_DISABLE,
    };
    ESP_RETURN_ON_ERROR(gpio_config(&output_config), TAG,
                        "configure UWB output GPIOs failed");

    const gpio_config_t irq_config = {
        .pin_bit_mask = 1ULL << BOARD_CONFIG_UWB_IRQ_GPIO,
        .mode = GPIO_MODE_INPUT,
        .pull_up_en = GPIO_PULLUP_DISABLE,
        .pull_down_en = GPIO_PULLDOWN_DISABLE,
        .intr_type = GPIO_INTR_DISABLE,
    };
    ESP_RETURN_ON_ERROR(gpio_config(&irq_config), TAG,
                        "configure UWB IRQ GPIO failed");

    ESP_RETURN_ON_ERROR(gpio_set_level(BOARD_CONFIG_UWB_CS_GPIO, 1), TAG,
                        "set UWB CS high failed");
    ESP_RETURN_ON_ERROR(
        gpio_set_level(BOARD_CONFIG_UWB_WAKEUP_GPIO,
                       gpio_level_active(BOARD_CONFIG_UWB_WAKEUP_ACTIVE_HIGH)),
        TAG, "set UWB WAKEUP active failed");
    ESP_RETURN_ON_ERROR(
        gpio_set_level(BOARD_CONFIG_UWB_RST_GPIO,
                       gpio_level_inactive(BOARD_CONFIG_UWB_RST_ACTIVE_HIGH)),
        TAG, "set UWB RST inactive failed");

    return ESP_OK;
}

static esp_err_t uwb_dw3000_configure_host_irq(void)
{
#if APP_UWB_IRQ_ENABLED
    esp_err_t err = gpio_install_isr_service(0);
    if (err != ESP_OK && err != ESP_ERR_INVALID_STATE) {
        ESP_LOGW(TAG, "DW3000 host IRQ service unavailable: %s",
                 esp_err_to_name(err));
        return err;
    }

    err = gpio_isr_handler_add(BOARD_CONFIG_UWB_IRQ_GPIO,
                               uwb_dw3000_irq_isr_handler, NULL);
    if (err != ESP_OK) {
        ESP_LOGW(TAG, "DW3000 host IRQ handler unavailable: %s",
                 esp_err_to_name(err));
        return err;
    }

    ESP_RETURN_ON_ERROR(gpio_set_intr_type(BOARD_CONFIG_UWB_IRQ_GPIO,
                                           GPIO_INTR_POSEDGE),
                        TAG, "set UWB IRQ edge failed");
    ESP_RETURN_ON_ERROR(gpio_intr_enable(BOARD_CONFIG_UWB_IRQ_GPIO), TAG,
                        "enable UWB IRQ GPIO failed");

    s_irq_enabled = true;
    ESP_LOGI(TAG, "DW3000 host IRQ enabled on GPIO%d",
             BOARD_CONFIG_UWB_IRQ_GPIO);
    return ESP_OK;
#else
    s_irq_enabled = false;
    ESP_LOGI(TAG, "DW3000 host IRQ disabled by config");
    return ESP_OK;
#endif
}

esp_err_t uwb_dw3000_hold_in_reset(void)
{
    const uint64_t output_pin_mask =
        (1ULL << BOARD_CONFIG_UWB_CS_GPIO) |
        (1ULL << BOARD_CONFIG_UWB_WAKEUP_GPIO) |
        (1ULL << BOARD_CONFIG_UWB_RST_GPIO);

    const gpio_config_t output_config = {
        .pin_bit_mask = output_pin_mask,
        .mode = GPIO_MODE_OUTPUT,
        .pull_up_en = GPIO_PULLUP_DISABLE,
        .pull_down_en = GPIO_PULLDOWN_DISABLE,
        .intr_type = GPIO_INTR_DISABLE,
    };
    ESP_RETURN_ON_ERROR(gpio_config(&output_config), TAG,
                        "configure UWB reset GPIOs failed");
    ESP_RETURN_ON_ERROR(gpio_set_level(BOARD_CONFIG_UWB_CS_GPIO, 1), TAG,
                        "set UWB CS high failed");
    ESP_RETURN_ON_ERROR(
        gpio_set_level(BOARD_CONFIG_UWB_WAKEUP_GPIO,
                       gpio_level_inactive(BOARD_CONFIG_UWB_WAKEUP_ACTIVE_HIGH)),
        TAG, "set UWB WAKEUP inactive failed");
    ESP_RETURN_ON_ERROR(
        gpio_set_level(BOARD_CONFIG_UWB_RST_GPIO,
                       gpio_level_active(BOARD_CONFIG_UWB_RST_ACTIVE_HIGH)),
        TAG, "hold UWB RST active failed");

    s_status = UWB_DW3000_STATUS_IDLE;
    ESP_LOGW(TAG, "DW3000 held in reset for low-power/component-disable mode");
    return ESP_OK;
}

static esp_err_t uwb_dw3000_hardware_reset(void)
{
    ESP_RETURN_ON_ERROR(
        gpio_set_level(BOARD_CONFIG_UWB_RST_GPIO,
                       gpio_level_inactive(BOARD_CONFIG_UWB_RST_ACTIVE_HIGH)),
        TAG, "set UWB RST inactive failed");
    uwb_dw3000_delay_ms(UWB_DW3000_RESET_SETTLE_MS);

    ESP_RETURN_ON_ERROR(
        gpio_set_level(BOARD_CONFIG_UWB_RST_GPIO,
                       gpio_level_active(BOARD_CONFIG_UWB_RST_ACTIVE_HIGH)),
        TAG, "set UWB RST active failed");
    uwb_dw3000_delay_ms(UWB_DW3000_RESET_PULSE_MS);

    ESP_RETURN_ON_ERROR(
        gpio_set_level(BOARD_CONFIG_UWB_RST_GPIO,
                       gpio_level_inactive(BOARD_CONFIG_UWB_RST_ACTIVE_HIGH)),
        TAG, "release UWB RST failed");
    return ESP_OK;
}

static esp_err_t uwb_dw3000_add_spi_device(uint32_t requested_clock_hz)
{
    spi_device_interface_config_t device_config = {
        .clock_speed_hz = (int)requested_clock_hz,
        .mode = 0,
        .spics_io_num = BOARD_CONFIG_UWB_CS_GPIO,
        .queue_size = 1,
    };

    ESP_RETURN_ON_ERROR(
        spi_bus_add_device(UWB_DW3000_SPI_HOST, &device_config, &s_spi), TAG,
        "spi_bus_add_device failed");

    int actual_clock_khz = 0;
    esp_err_t err = spi_device_get_actual_freq(s_spi, &actual_clock_khz);
    if (err != ESP_OK || actual_clock_khz <= 0) {
        (void)spi_bus_remove_device(s_spi);
        s_spi = NULL;
        return err == ESP_OK ? ESP_FAIL : err;
    }

    s_spi_clock_hz = (uint32_t)actual_clock_khz * 1000U;
    if (s_spi_clock_hz > UWB_DW3000_SPI_DATASHEET_MAX_HZ) {
        ESP_LOGW(TAG,
                 "DW3000 SPI actual clock %lu Hz exceeds datasheet maximum %u Hz",
                 (unsigned long)s_spi_clock_hz,
                 (unsigned)UWB_DW3000_SPI_DATASHEET_MAX_HZ);
    }
    if (s_spi_clock_hz > UWB_DW3000_SPI_VALIDATED_MAX_HZ) {
        ESP_LOGE(TAG,
                 "DW3000 SPI actual clock %lu Hz exceeds validated maximum %u Hz",
                 (unsigned long)s_spi_clock_hz,
                 (unsigned)UWB_DW3000_SPI_VALIDATED_MAX_HZ);
        (void)spi_bus_remove_device(s_spi);
        s_spi = NULL;
        s_spi_clock_hz = 0;
        return ESP_ERR_INVALID_ARG;
    }

    ESP_LOGI(TAG, "DW3000 SPI clock: requested=%lu Hz actual=%lu Hz",
             (unsigned long)requested_clock_hz,
             (unsigned long)s_spi_clock_hz);
    return ESP_OK;
}

static esp_err_t uwb_dw3000_init_spi(void)
{
    spi_bus_config_t bus_config = {
        .mosi_io_num = BOARD_CONFIG_SPI_MOSI_GPIO,
        .miso_io_num = BOARD_CONFIG_SPI_MISO_GPIO,
        .sclk_io_num = BOARD_CONFIG_SPI_SCK_GPIO,
        .quadwp_io_num = -1,
        .quadhd_io_num = -1,
        .max_transfer_sz = UWB_DW3000_SPI_MAX_TRANSFER_BYTES,
    };

    esp_err_t err =
        spi_bus_initialize(UWB_DW3000_SPI_HOST, &bus_config, SPI_DMA_DISABLED);
    if (err != ESP_OK && err != ESP_ERR_INVALID_STATE) {
        ESP_LOGE(TAG, "spi_bus_initialize failed: %s", esp_err_to_name(err));
        return err;
    }

    return uwb_dw3000_add_spi_device(UWB_DW3000_SPI_BOOT_CLOCK_HZ);
}

static size_t uwb_dw3000_build_header(uint8_t *header, size_t header_size,
                                      uint8_t base, uint8_t sub,
                                      bool write)
{
    if (header_size < 1) {
        return 0;
    }

    const uint32_t reg_file_id =
        ((uint32_t)(base & 0x1FU) << 16) | (uint32_t)sub;
    const uint16_t reg_file =
        (uint16_t)(0x1FU & (reg_file_id >> 16));
    const uint16_t reg_offset = (uint16_t)(0x7FU & reg_file_id);
    const uint16_t address =
        (uint16_t)((reg_file << 9) | (reg_offset << 2));
    const uint16_t mode = write ? 0x8000U : 0x0000U;

    header[0] = (uint8_t)((mode | address) >> 8);
    if (reg_offset == 0) {
        return 1;
    }

    if (header_size < 2) {
        return 0;
    }

    header[0] |= 0x40U;
    header[1] = (uint8_t)address;
    return 2;
}

static esp_err_t uwb_dw3000_read_bytes(uint8_t base, uint8_t sub, uint8_t *data,
                                       size_t len)
{
    uint8_t tx[UWB_DW3000_SPI_MAX_TRANSFER_BYTES];
    uint8_t rx[UWB_DW3000_SPI_MAX_TRANSFER_BYTES];
    if (data == NULL || len == 0U ||
        (size_t)sub + len > 128U) {
        return ESP_ERR_INVALID_ARG;
    }

    size_t offset = 0U;
    while (offset < len) {
        const uint8_t chunk_sub = (uint8_t)((size_t)sub + offset);
        const size_t header_len = uwb_dw3000_build_header(
            tx, sizeof(tx), base, chunk_sub, false);
        if (header_len == 0U ||
            header_len >= UWB_DW3000_SPI_POLLING_TRANSFER_BYTES) {
            return ESP_ERR_INVALID_ARG;
        }
        const size_t capacity =
            UWB_DW3000_SPI_POLLING_TRANSFER_BYTES - header_len;
        const size_t remaining = len - offset;
        const size_t chunk_len = remaining < capacity ? remaining : capacity;
        const size_t total_len = header_len + chunk_len;

        memset(tx + header_len, 0, chunk_len);
        spi_transaction_t transaction = {
            .length = total_len * 8U,
            .tx_buffer = tx,
            .rx_buffer = rx,
        };
        ESP_RETURN_ON_ERROR(spi_device_polling_transmit(s_spi, &transaction),
                            TAG, "SPI read failed");
        memcpy(data + offset, rx + header_len, chunk_len);
        offset += chunk_len;
    }
    return ESP_OK;
}

static esp_err_t uwb_dw3000_write_bytes(uint8_t base, uint8_t sub,
                                        const uint8_t *data, size_t len)
{
    uint8_t tx[UWB_DW3000_SPI_MAX_TRANSFER_BYTES];
    if (data == NULL || len == 0U ||
        (size_t)sub + len > 128U) {
        return ESP_ERR_INVALID_ARG;
    }

    size_t offset = 0U;
    while (offset < len) {
        const uint8_t chunk_sub = (uint8_t)((size_t)sub + offset);
        const size_t header_len = uwb_dw3000_build_header(
            tx, sizeof(tx), base, chunk_sub, true);
        if (header_len == 0U ||
            header_len >= UWB_DW3000_SPI_POLLING_TRANSFER_BYTES) {
            return ESP_ERR_INVALID_ARG;
        }
        const size_t capacity =
            UWB_DW3000_SPI_POLLING_TRANSFER_BYTES - header_len;
        const size_t remaining = len - offset;
        const size_t chunk_len = remaining < capacity ? remaining : capacity;
        const size_t total_len = header_len + chunk_len;

        memcpy(tx + header_len, data + offset, chunk_len);
        spi_transaction_t transaction = {
            .length = total_len * 8U,
            .tx_buffer = tx,
        };
        ESP_RETURN_ON_ERROR(spi_device_polling_transmit(s_spi, &transaction),
                            TAG, "SPI write failed");
        offset += chunk_len;
    }
    return ESP_OK;
}

static size_t uwb_dw3000_auto_len(uint32_t value)
{
    size_t len = 1;
    while (len < sizeof(uint32_t) && (value >> (len * 8U)) != 0U) {
        len++;
    }
    return len;
}

static esp_err_t uwb_dw3000_write_u32_len(uint8_t base, uint8_t sub,
                                          uint32_t value, size_t len)
{
    uint8_t tx[2U + sizeof(uint32_t)];
    const size_t header_len =
        uwb_dw3000_build_header(tx, sizeof(tx), base, sub, true);
    if (len == 0 || len > sizeof(uint32_t) || header_len == 0) {
        return ESP_ERR_INVALID_ARG;
    }

    for (size_t i = 0; i < len; ++i) {
        tx[header_len + i] = (uint8_t)((value >> (8U * i)) & 0xFFU);
    }

    spi_transaction_t transaction = {
        .length = (header_len + len) * 8U,
        .tx_buffer = tx,
    };
    return spi_device_polling_transmit(s_spi, &transaction);
}

static esp_err_t uwb_dw3000_write_u32_auto(uint8_t base, uint8_t sub,
                                           uint32_t value)
{
    return uwb_dw3000_write_u32_len(base, sub, value,
                                    uwb_dw3000_auto_len(value));
}

static esp_err_t uwb_dw3000_read32(uint8_t base, uint8_t sub, uint32_t *value)
{
    uint8_t tx[2U + sizeof(uint32_t)];
    uint8_t rx[2U + sizeof(uint32_t)];
    const size_t header_len =
        uwb_dw3000_build_header(tx, sizeof(tx), base, sub, false);
    if (value == NULL || header_len == 0) {
        return ESP_ERR_INVALID_ARG;
    }
    memset(tx + header_len, 0, sizeof(uint32_t));
    spi_transaction_t transaction = {
        .length = (header_len + sizeof(uint32_t)) * 8U,
        .tx_buffer = tx,
        .rx_buffer = rx,
    };
    ESP_RETURN_ON_ERROR(spi_device_polling_transmit(s_spi, &transaction), TAG,
                        "read32 failed");

    const uint8_t *bytes = rx + header_len;
    *value = ((uint32_t)bytes[0]) | ((uint32_t)bytes[1] << 8) |
             ((uint32_t)bytes[2] << 16) | ((uint32_t)bytes[3] << 24);
    return ESP_OK;
}

static esp_err_t uwb_dw3000_verify_spi_link(uint32_t expected_device_id,
                                            uint32_t read_count)
{
    for (uint32_t read_index = 0; read_index < read_count; ++read_index) {
        uint32_t device_id = 0;
        const esp_err_t err = uwb_dw3000_read32(
            DW3000_REG_GEN_CFG_AES_LOW, DW3000_SUB_NONE, &device_id);
        if (err != ESP_OK || device_id != expected_device_id) {
            ESP_LOGE(TAG,
                     "DW3000 SPI verify %lu/%lu failed: err=%s dev_id=0x%08lx expected=0x%08lx",
                     (unsigned long)(read_index + 1U),
                     (unsigned long)read_count, esp_err_to_name(err),
                     (unsigned long)device_id,
                     (unsigned long)expected_device_id);
            return err == ESP_OK ? ESP_ERR_INVALID_RESPONSE : err;
        }
    }

    return ESP_OK;
}

static esp_err_t uwb_dw3000_restore_boot_spi(uint32_t expected_device_id)
{
    if (s_spi != NULL) {
        ESP_RETURN_ON_ERROR(spi_bus_remove_device(s_spi), TAG,
                            "remove operational SPI device failed");
        s_spi = NULL;
        s_spi_clock_hz = 0;
    }

    ESP_RETURN_ON_ERROR(
        uwb_dw3000_add_spi_device(UWB_DW3000_SPI_BOOT_CLOCK_HZ), TAG,
        "restore boot SPI clock failed");
    ESP_RETURN_ON_ERROR(
        uwb_dw3000_verify_spi_link(expected_device_id, 1), TAG,
        "boot SPI fallback verification failed");
    ESP_LOGW(TAG, "DW3000 continues with boot SPI clock %lu Hz",
             (unsigned long)s_spi_clock_hz);
    return ESP_OK;
}

static esp_err_t uwb_dw3000_enable_operational_spi(uint32_t expected_device_id)
{
    ESP_RETURN_ON_ERROR(spi_bus_remove_device(s_spi), TAG,
                        "remove boot SPI device failed");
    s_spi = NULL;
    s_spi_clock_hz = 0;

    esp_err_t err =
        uwb_dw3000_add_spi_device(UWB_DW3000_SPI_OPERATION_REQUEST_HZ);
    if (err == ESP_OK) {
        err = uwb_dw3000_verify_spi_link(expected_device_id,
                                         UWB_DW3000_SPI_VERIFY_READS);
    }
    if (err == ESP_OK) {
        ESP_LOGI(TAG,
                 "DW3000 operational SPI verified: %lu DEV_ID reads at %lu Hz",
                 (unsigned long)UWB_DW3000_SPI_VERIFY_READS,
                 (unsigned long)s_spi_clock_hz);
        return ESP_OK;
    }

    ESP_LOGW(TAG, "DW3000 operational SPI rejected, restoring boot clock");
    return uwb_dw3000_restore_boot_spi(expected_device_id);
}

static esp_err_t uwb_dw3000_read_timestamp40(uint8_t base, uint8_t sub,
                                             uint64_t *timestamp)
{
    uint8_t bytes[5] = {0};
    if (timestamp == NULL) {
        return ESP_ERR_INVALID_ARG;
    }

    ESP_RETURN_ON_ERROR(uwb_dw3000_read_bytes(base, sub, bytes, sizeof(bytes)),
                        TAG, "timestamp read failed");
    *timestamp = ((uint64_t)bytes[0]) | ((uint64_t)bytes[1] << 8) |
                 ((uint64_t)bytes[2] << 16) |
                 ((uint64_t)bytes[3] << 24) |
                 ((uint64_t)bytes[4] << 32);
    *timestamp &= UWB_DW3000_TIMESTAMP_MASK;
    return ESP_OK;
}

static esp_err_t uwb_dw3000_read_rx_timestamp(uint64_t *timestamp)
{
    if (s_rx_double_buffer_enabled) {
        if (timestamp == NULL) {
            return ESP_ERR_INVALID_ARG;
        }

        const uint8_t base = s_rx_double_buffer_index == 0U
                                 ? DW3000_REG_DOUBLE_BUFFER_DIAG
                                 : DW3000_REG_INDIRECT_POINTER_B;
        const uint8_t time_sub = s_rx_double_buffer_index == 0U
                                     ? DW3000_DOUBLE_BUFFER_0_RX_TIME_SUB
                                     : DW3000_DOUBLE_BUFFER_1_RX_TIME_OFFSET;
        uint8_t low[4] = {0};
        ESP_RETURN_ON_ERROR(
            uwb_dw3000_read_bytes(base, time_sub, low, sizeof(low)), TAG,
            "buffered RX timestamp low read failed");

        const uint32_t low32 = ((uint32_t)low[0]) |
                               ((uint32_t)low[1] << 8U) |
                               ((uint32_t)low[2] << 16U) |
                               ((uint32_t)low[3] << 24U);
        if (s_runtime_mode == UWB_DW3000_RUNTIME_FLEX_TDOA) {
            return uwb_flex_tdoa_extend_rx_timestamp32(low32, timestamp);
        }

        uint32_t system_time_word = 0;
        ESP_RETURN_ON_ERROR(
            uwb_dw3000_read32(DW3000_REG_GEN_CFG_AES_LOW,
                              DW3000_SYS_TIME_SUB, &system_time_word),
            TAG, "RX timestamp reference read failed");
        const uint64_t reference = (uint64_t)system_time_word << 8U;

        const int32_t delta = (int32_t)(low32 - (uint32_t)reference);
        *timestamp = (reference + (int64_t)delta) &
                     UWB_DW3000_TIMESTAMP_MASK;
        return ESP_OK;
    }

    return uwb_dw3000_read_timestamp40(DW3000_REG_CIA_1, DW3000_RX_TIME_SUB,
                                       timestamp);
}

static esp_err_t uwb_dw3000_read_tx_timestamp(uint64_t *timestamp)
{
    return uwb_dw3000_read_timestamp40(DW3000_REG_GEN_CFG_AES_LOW,
                                       DW3000_TX_TIME_SUB, timestamp);
}

static int32_t uwb_dw3000_sign_extend(uint32_t value, uint8_t bits)
{
    const uint32_t sign_bit = 1UL << (bits - 1U);
    const uint32_t mask = (1UL << bits) - 1UL;
    value &= mask;
    return (int32_t)((value ^ sign_bit) - sign_bit);
}

static esp_err_t uwb_dw3000_read_clock_offset_raw(int32_t *clock_offset_raw,
                                                   bool *from_cia)
{
    if (clock_offset_raw == NULL || from_cia == NULL) {
        return ESP_ERR_INVALID_ARG;
    }

    if (s_rx_double_buffer_enabled) {
        const uint8_t base = s_rx_double_buffer_index == 0U
                                 ? DW3000_REG_DOUBLE_BUFFER_DIAG
                                 : DW3000_REG_INDIRECT_POINTER_B;
        const uint8_t sub =
            s_rx_double_buffer_index == 0U
                ? DW3000_DOUBLE_BUFFER_0_CIA_DIAG_0_SUB
                : DW3000_DOUBLE_BUFFER_1_CIA_DIAG_0_OFFSET;
        uint8_t bytes[2] = {0};
        ESP_RETURN_ON_ERROR(uwb_dw3000_read_bytes(base, sub, bytes,
                                                   sizeof(bytes)),
                            TAG, "buffered clock offset read failed");
        const uint16_t raw =
            (uint16_t)(((uint16_t)bytes[0]) | ((uint16_t)bytes[1] << 8U));
        *clock_offset_raw = uwb_dw3000_sign_extend(raw & 0x1FFFU, 13U);
        *from_cia = true;
        return ESP_OK;
    }

    uint32_t raw = 0;
    ESP_RETURN_ON_ERROR(
        uwb_dw3000_read32(DW3000_REG_DRX, DW3000_DRX_CAR_INT_SUB, &raw), TAG,
        "clock offset read failed");
    *clock_offset_raw = uwb_dw3000_sign_extend(
        raw & DW3000_CLOCK_OFFSET_RAW_MASK, DW3000_CLOCK_OFFSET_RAW_BITS);
    *from_cia = false;
    return ESP_OK;
}

static double uwb_dw3000_clock_offset_ratio(int32_t clock_offset_raw)
{
    const double factor = uwb_dw3000_runtime_radio_rf_channel_bit() == 0
                              ? DW3000_CLOCK_OFFSET_CH5_FACTOR
                              : DW3000_CLOCK_OFFSET_CH9_FACTOR;
    return (double)clock_offset_raw * factor;
}

static double uwb_dw3000_cia_clock_offset_ratio(int32_t clock_offset_raw)
{
    return flextdoa_dw3000_cia_scale_delta((int16_t)clock_offset_raw);
}

static double uwb_dw3000_remote_interval_in_local_dtu(
    double remote_interval_dtu, double clock_offset_ratio)
{
    // uwb_dw3000_clock_offset_ratio() already applies the channel-specific
    // negative DRX_CAR_INT scale. Reciprocal anchor measurements on hardware
    // converge only when that converted value is applied with (1 + ratio);
    // applying the API-guide sign a second time makes the two directions
    // diverge symmetrically by metres for a 5 ms reply interval.
    return remote_interval_dtu * (1.0 + clock_offset_ratio);
}

static uint64_t uwb_dw3000_add_timestamp_delta(uint64_t timestamp,
                                               uint64_t delta)
{
    return (timestamp + delta) & UWB_DW3000_TIMESTAMP_MASK;
}

static uint64_t uwb_dw3000_sub_timestamp_delta(uint64_t timestamp,
                                               uint64_t delta)
{
    return (timestamp - delta) & UWB_DW3000_TIMESTAMP_MASK;
}

static uint64_t uwb_dw3000_ms_to_dtu(uint32_t delay_ms)
{
    const double delay_seconds = (double)delay_ms / 1000.0;
    return (uint64_t)((delay_seconds / UWB_DW3000_TIME_UNIT_SECONDS) + 0.5);
}

static uint64_t uwb_dw3000_us_to_dtu(uint32_t delay_us)
{
    const double delay_seconds = (double)delay_us / 1000000.0;
    return (uint64_t)((delay_seconds / UWB_DW3000_TIME_UNIT_SECONDS) + 0.5);
}

static int64_t uwb_dw3000_dtu_to_us(uint64_t interval_dtu)
{
    return (int64_t)(((double)interval_dtu *
                      UWB_DW3000_TIME_UNIT_SECONDS * 1000000.0) +
                     0.5);
}

static uint32_t uwb_dw3000_delayed_time_word(uint64_t tx_timestamp)
{
    return (uint32_t)(tx_timestamp >> 8U);
}

static uint64_t uwb_dw3000_programmed_tx_timestamp(uint32_t delayed_time_word)
{
    return ((((uint64_t)(delayed_time_word & UWB_DW3000_DELAYED_TIME_MASK))
             << 8U) +
            s_antenna_delay) &
           UWB_DW3000_TIMESTAMP_MASK;
}

static esp_err_t uwb_dw3000_set_delayed_trx_time(uint32_t delayed_time_word)
{
    return uwb_dw3000_write_u32_len(DW3000_REG_GEN_CFG_AES_LOW,
                                    DW3000_DX_TIME_SUB, delayed_time_word, 4);
}

static esp_err_t
uwb_dw3000_configure_cia_diagnostics(bool enable_all_registers)
{
    if (!enable_all_registers) {
        ESP_RETURN_ON_ERROR(
            uwb_dw3000_update_u32(DW3000_REG_CIA_3, DW3000_SUB_NONE, 0,
                                  DW3000_CIA_CONF_DIAGNOSTIC_OFF_MASK),
            TAG, "CIA diagnostics disable failed");
        ESP_LOGI(TAG, "DW3000 CIA diagnostics disabled");
        return ESP_OK;
    }

    ESP_RETURN_ON_ERROR(
        uwb_dw3000_update_u32(DW3000_REG_CIA_3, DW3000_SUB_NONE,
                              DW3000_CIA_CONF_DIAGNOSTIC_OFF_MASK, 0),
        TAG, "CIA diagnostics enable failed");
    ESP_RETURN_ON_ERROR(
        uwb_dw3000_write_u32_len(DW3000_REG_RDB_STATUS,
                                 DW3000_RDB_DIAG_MODE_SUB,
                                 DW3000_CIA_DIAG_LOG_ALL >> 1U, 1),
        TAG, "RDB_DIAG_MODE write failed");
    ESP_LOGI(TAG, "DW3000 CIA diagnostics enabled");
    return ESP_OK;
}

static esp_err_t
uwb_dw3000_read_rx_diagnostics(struct uwb_rx_diagnostics *diagnostics)
{
    if (diagnostics == NULL) {
        return ESP_ERR_INVALID_ARG;
    }

    memset(diagnostics, 0, sizeof(*diagnostics));

#if APP_UWB_DIAGNOSTICS_ENABLED
    uint32_t rx_finfo = 0;
    uint32_t cia_diag0 = 0;
    uint32_t ip_diag0 = 0;
    uint32_t ip_diag1 = 0;
    uint32_t ip_diag2 = 0;
    uint32_t ip_diag3 = 0;
    uint32_t ip_diag4 = 0;
    uint32_t ip_diag8 = 0;
    uint32_t ip_diag12 = 0;

    ESP_RETURN_ON_ERROR(
        uwb_dw3000_read32(DW3000_REG_GEN_CFG_AES_LOW, DW3000_RX_FINFO_SUB,
                          &rx_finfo),
        TAG,
        "RX diagnostics RX_FINFO read failed");
    ESP_RETURN_ON_ERROR(
        uwb_dw3000_read32(DW3000_REG_CIA_1, DW3000_CIA_DIAG_0_SUB,
                          &cia_diag0),
        TAG, "RX diagnostics CIA_DIAG_0 read failed");
    ESP_RETURN_ON_ERROR(
        uwb_dw3000_read32(DW3000_REG_CIA_1, DW3000_IP_DIAG_0_SUB, &ip_diag0),
        TAG, "RX diagnostics IP_DIAG_0 read failed");
    ESP_RETURN_ON_ERROR(
        uwb_dw3000_read32(DW3000_REG_CIA_1, DW3000_IP_DIAG_1_SUB, &ip_diag1),
        TAG, "RX diagnostics IP_DIAG_1 read failed");
    ESP_RETURN_ON_ERROR(
        uwb_dw3000_read32(DW3000_REG_CIA_1, DW3000_IP_DIAG_2_SUB, &ip_diag2),
        TAG, "RX diagnostics IP_DIAG_2 read failed");
    ESP_RETURN_ON_ERROR(
        uwb_dw3000_read32(DW3000_REG_CIA_1, DW3000_IP_DIAG_3_SUB, &ip_diag3),
        TAG, "RX diagnostics IP_DIAG_3 read failed");
    ESP_RETURN_ON_ERROR(
        uwb_dw3000_read32(DW3000_REG_CIA_1, DW3000_IP_DIAG_4_SUB, &ip_diag4),
        TAG, "RX diagnostics IP_DIAG_4 read failed");
    ESP_RETURN_ON_ERROR(
        uwb_dw3000_read32(DW3000_REG_CIA_1, DW3000_IP_DIAG_8_SUB, &ip_diag8),
        TAG, "RX diagnostics IP_DIAG_8 read failed");
    ESP_RETURN_ON_ERROR(
        uwb_dw3000_read32(DW3000_REG_CIA_1, DW3000_IP_DIAG_12_SUB,
                          &ip_diag12),
        TAG, "RX diagnostics IP_DIAG_12 read failed");

    diagnostics->valid = true;
    diagnostics->rx_pacc =
        (uint16_t)((rx_finfo & DW3000_RX_FINFO_RXPACC_MASK) >>
                   DW3000_RX_FINFO_RXPACC_SHIFT);
    diagnostics->xtal_offset = (int16_t)uwb_dw3000_sign_extend(
        cia_diag0 & DW3000_CIA_XTAL_OFFSET_MASK, 13);
    ip_diag0 &= DW3000_IPATOV_PEAK_MASK;
    diagnostics->ipatov_peak_amp =
        ip_diag0 & DW3000_IPATOV_PEAK_AMP_MASK;
    diagnostics->ipatov_peak_index =
        (uint16_t)(ip_diag0 >> DW3000_IPATOV_PEAK_INDEX_SHIFT);
    diagnostics->ipatov_power = ip_diag1 & DW3000_IPATOV_POWER_MASK;
    diagnostics->ipatov_f1 = ip_diag2 & DW3000_IPATOV_F_MASK;
    diagnostics->ipatov_f2 = ip_diag3 & DW3000_IPATOV_F_MASK;
    diagnostics->ipatov_f3 = ip_diag4 & DW3000_IPATOV_F_MASK;
    diagnostics->ipatov_fp_index =
        (uint16_t)(ip_diag8 & DW3000_IPATOV_FP_INDEX_MASK);
    diagnostics->ipatov_accum_count =
        (uint16_t)(ip_diag12 & DW3000_IPATOV_ACCUM_COUNT_MASK);
#endif

    return ESP_OK;
}

static bool uwb_dw3000_payload_is_distance_frame(const uint8_t *payload,
                                                 size_t payload_len)
{
    return payload != NULL && payload_len >= UWB_DISTANCE_FRAME_HEADER_LEN &&
           payload[0] == UWB_DISTANCE_FRAME_MAGIC_0 &&
           payload[1] == UWB_DISTANCE_FRAME_MAGIC_1 &&
           payload[2] == UWB_DISTANCE_FRAME_MAGIC_2 &&
           payload[3] == UWB_DISTANCE_FRAME_MAGIC_3 &&
           payload[4] == UWB_DISTANCE_FRAME_VERSION;
}

static bool uwb_dw3000_payload_is_flextdoa_localization(
    const uint8_t *payload, size_t payload_len,
    enum flextdoa_message_type expected_type)
{
    if (payload == NULL || payload_len < FLEXTDOA_PACKET_FIXED_SIZE ||
        (expected_type != FLEXTDOA_MESSAGE_REQUEST &&
         expected_type != FLEXTDOA_MESSAGE_RESPONSE)) {
        return false;
    }
    struct flextdoa_packet packet = {0};
    return flextdoa_decode_packet(payload, payload_len, &packet) &&
           packet.type == expected_type;
}

static bool uwb_dw3000_should_capture_rx_diagnostics(const uint8_t *payload,
                                                     size_t payload_len)
{
#if APP_UWB_DIAGNOSTICS_ENABLED
    const app_runtime_config_t *config = app_runtime_config_get();
    if (config != NULL &&
        config->runtime_mode == APP_RUNTIME_MODE_UWB_RANGING) {
        /*
         * Native DS-TWR has a delayed TX deadline immediately after every
         * useful RX frame. Reading the full CIA diagnostic register set and
         * forwarding an ESP_LOG line here consumed several milliseconds on
         * the field modules, enough to make an otherwise valid 2-5 ms reply
         * late. Keep RF diagnostics for the dedicated distance-test modes;
         * Native DS exposes its timestamps, range and pipeline counters after
         * the exchange has completed instead.
         */
        return false;
    }

    if (!uwb_dw3000_payload_is_distance_frame(payload, payload_len) ||
        APP_UWB_DIAGNOSTICS_LOG_EVERY == 0) {
        return false;
    }

    const uint8_t frame_type = payload[5];
    if (frame_type == UWB_DISTANCE_FRAME_FLEX_TDOA_REQ ||
        frame_type == UWB_DISTANCE_FRAME_FLEX_TDOA_RESP ||
        frame_type == UWB_DISTANCE_FRAME_PASSIVE_DS_MULTI_POLL ||
        frame_type == UWB_DISTANCE_FRAME_PASSIVE_DS_MULTI_RESP ||
        frame_type == UWB_DISTANCE_FRAME_PASSIVE_DS_MULTI_FINAL) {
        return false;
    }

    const uint16_t sequence =
        (uint16_t)(((uint16_t)payload[8]) | ((uint16_t)payload[9] << 8));
    return (sequence % APP_UWB_DIAGNOSTICS_LOG_EVERY) == 0;
#else
    (void)payload;
    (void)payload_len;
    return false;
#endif
}

static esp_err_t uwb_dw3000_update_u32(uint8_t base, uint8_t sub,
                                       uint32_t clear_mask,
                                       uint32_t set_mask)
{
    uint32_t value = 0;
    ESP_RETURN_ON_ERROR(uwb_dw3000_read32(base, sub, &value), TAG,
                        "read before register update failed");
    value &= ~clear_mask;
    value |= set_mask;
    return uwb_dw3000_write_u32_len(base, sub, value, sizeof(value));
}

static esp_err_t uwb_dw3000_read_rdb_status(uint8_t *status)
{
    if (status == NULL) {
        return ESP_ERR_INVALID_ARG;
    }
    return uwb_dw3000_read_bytes(DW3000_REG_RDB_STATUS,
                                 DW3000_RDB_STATUS_SUB, status, 1);
}

static uint8_t uwb_dw3000_current_rdb_good_mask(void)
{
    return s_rx_double_buffer_index == 0U
               ? DW3000_RDB_BUFFER_0_GOOD_MASK
               : DW3000_RDB_BUFFER_1_GOOD_MASK;
}

static uint8_t uwb_dw3000_current_rdb_cia_done_mask(void)
{
    return s_rx_double_buffer_index == 0U
               ? DW3000_RDB_BUFFER_0_CIA_DONE_MASK
               : DW3000_RDB_BUFFER_1_CIA_DONE_MASK;
}

static uint8_t uwb_dw3000_current_rdb_clear_mask(void)
{
    return s_rx_double_buffer_index == 0U
               ? DW3000_RDB_BUFFER_0_CLEAR_MASK
               : DW3000_RDB_BUFFER_1_CLEAR_MASK;
}

static esp_err_t uwb_dw3000_release_rx_double_buffer(void)
{
    // Qorvo's double-buffer sequence is read data, clear the processed RDB
    // status and the corresponding RX-good events, then toggle the host
    // buffer pointer. A global CMD_CLR_IRQS here can erase unrelated TX state.
    ESP_RETURN_ON_ERROR(
        uwb_dw3000_write_u32_len(DW3000_REG_RDB_STATUS,
                                 DW3000_RDB_STATUS_SUB,
                                 uwb_dw3000_current_rdb_clear_mask(), 1),
        TAG, "double-buffer RDB_STATUS clear failed");
    ESP_RETURN_ON_ERROR(
        uwb_dw3000_write_u32_len(DW3000_REG_GEN_CFG_AES_LOW,
                                 DW3000_SYS_STATUS_SUB,
                                 DW3000_STATUS_RX_GOOD_CLEAR_MASK, 4),
        TAG, "double-buffer RX-good status clear failed");
    ESP_RETURN_ON_ERROR(uwb_dw3000_fast_command(DW3000_CMD_DB_TOGGLE), TAG,
                        "double-buffer release failed");
    s_rx_double_buffer_index ^= 1U;
    return ESP_OK;
}

static esp_err_t uwb_dw3000_release_pending_flex_request(void)
{
    if (!s_flex_tdoa_anchor_request_buffer_pending) {
        return ESP_OK;
    }
    const esp_err_t err = uwb_dw3000_release_rx_double_buffer();
    if (err == ESP_OK) {
        s_flex_tdoa_anchor_request_buffer_pending = false;
    }
    return err;
}

static esp_err_t uwb_dw3000_configure_high_rate_rx_double_buffer(void)
{
    ESP_RETURN_ON_ERROR(uwb_dw3000_fast_command(DW3000_CMD_TXRXOFF), TAG,
                        "stop RX before double-buffer setup failed");
    s_rx_armed = false;

    // Seed on the first received frame, not here: the distributed bootstrap
    // listen interval is longer than the low-32 timestamp wrap.
    s_flex_tdoa_rx_timestamp_reference_valid = false;
    s_flex_tdoa_rx_timestamp_reference = 0;
    s_flex_tdoa_rx_timestamp_reference_host_us = 0;

    ESP_RETURN_ON_ERROR(
        uwb_dw3000_write_u32_len(DW3000_REG_INDIRECT_CTRL,
                                 DW3000_INDIRECT_ADDR_B_SUB,
                                 DW3000_DOUBLE_BUFFER_1_DIAG_BASE, 4),
        TAG, "double-buffer indirect base setup failed");
    ESP_RETURN_ON_ERROR(
        uwb_dw3000_write_u32_len(DW3000_REG_INDIRECT_CTRL,
                                 DW3000_ADDR_OFFSET_B_SUB,
                                 DW3000_DOUBLE_BUFFER_1_DIAG_OFFSET, 4),
        TAG, "double-buffer indirect offset setup failed");
    ESP_RETURN_ON_ERROR(
        uwb_dw3000_update_u32(DW3000_REG_CIA_3, DW3000_SUB_NONE, 0,
                              DW3000_CIA_CONF_DIAGNOSTIC_OFF_MASK),
        TAG, "double-buffer full CIA diagnostics disable failed");
    ESP_RETURN_ON_ERROR(
        uwb_dw3000_write_u32_len(DW3000_REG_RDB_STATUS,
                                 DW3000_RDB_DIAG_MODE_SUB,
                                 DW3000_CIA_DIAG_LOG_MIN >> 1U, 1),
        TAG, "double-buffer diagnostic set setup failed");
    ESP_RETURN_ON_ERROR(
        uwb_dw3000_update_u32(
            DW3000_REG_GEN_CFG_AES_LOW, DW3000_SYS_CFG_SUB,
            DW3000_SYS_CFG_DIS_DRXB_BIT_MASK |
                DW3000_SYS_CFG_RXAUTR_BIT_MASK,
            0),
        TAG, "double-buffer SYS_CFG setup failed");
    ESP_RETURN_ON_ERROR(
        uwb_dw3000_write_u32_len(DW3000_REG_RDB_STATUS,
                                 DW3000_RDB_STATUS_SUB, 0xFFU, 1),
        TAG, "double-buffer status reset failed");
    ESP_RETURN_ON_ERROR(uwb_dw3000_clear_status(), TAG,
                        "double-buffer initial SYS_STATUS clear failed");

    uint32_t sys_cfg = 0;
    ESP_RETURN_ON_ERROR(
        uwb_dw3000_read32(DW3000_REG_GEN_CFG_AES_LOW, DW3000_SYS_CFG_SUB,
                          &sys_cfg),
        TAG, "double-buffer SYS_CFG verification read failed");
    if ((sys_cfg & DW3000_SYS_CFG_DIS_DRXB_BIT_MASK) != 0U ||
        (sys_cfg & DW3000_SYS_CFG_RXAUTR_BIT_MASK) != 0U) {
        ESP_LOGE(TAG, "DW3000 double-buffer verification failed SYS_CFG=0x%08lx",
                 (unsigned long)sys_cfg);
        return ESP_ERR_INVALID_STATE;
    }

    s_rx_double_buffer_index = 0;
    s_flex_tdoa_anchor_request_buffer_pending = false;
    s_rx_double_buffer_resync_count = 0;
    s_rx_double_buffer_enabled = true;
    ESP_LOGI(TAG,
             "DW3000 high-rate RX double buffer enabled with manual early re-arm mode=%u",
             (unsigned)s_runtime_mode);
    return ESP_OK;
}

static esp_err_t uwb_dw3000_configure_device_interrupts(void)
{
#if APP_UWB_IRQ_ENABLED
    if (!s_irq_enabled) {
        ESP_LOGW(TAG, "DW3000 IRQ fallback: host IRQ is unavailable");
        return ESP_OK;
    }

    ESP_RETURN_ON_ERROR(
        uwb_dw3000_write_u32_len(DW3000_REG_GEN_CFG_AES_LOW,
                                 DW3000_SYS_ENABLE_LO_SUB, 0, 4),
        TAG, "SYS_ENABLE low clear failed");
    ESP_RETURN_ON_ERROR(
        uwb_dw3000_write_u32_len(DW3000_REG_GEN_CFG_AES_LOW,
                                 DW3000_SYS_ENABLE_HI_SUB, 0, 2),
        TAG, "SYS_ENABLE high clear failed");
    ESP_RETURN_ON_ERROR(
        uwb_dw3000_write_u32_len(DW3000_REG_GEN_CFG_AES_LOW,
                                 DW3000_SYS_ENABLE_LO_SUB,
                                 DW3000_IRQ_STATUS_MASK, 4),
        TAG, "SYS_ENABLE low write failed");

    ESP_LOGI(TAG, "DW3000 device IRQ mask enabled: 0x%08lx",
             (unsigned long)DW3000_IRQ_STATUS_MASK);
#else
    ESP_RETURN_ON_ERROR(
        uwb_dw3000_write_u32_len(DW3000_REG_GEN_CFG_AES_LOW,
                                 DW3000_SYS_ENABLE_LO_SUB, 0, 4),
        TAG, "SYS_ENABLE low disable failed");
    ESP_RETURN_ON_ERROR(
        uwb_dw3000_write_u32_len(DW3000_REG_GEN_CFG_AES_LOW,
                                 DW3000_SYS_ENABLE_HI_SUB, 0, 2),
        TAG, "SYS_ENABLE high disable failed");
    ESP_LOGI(TAG, "DW3000 device IRQ mask disabled by config");
#endif
    return ESP_OK;
}

static esp_err_t
uwb_dw3000_set_rx_after_tx_delay(uint32_t rx_after_tx_delay_uus)
{
    if ((rx_after_tx_delay_uus & ~DW3000_ACK_RESP_W4R_TIM_BIT_MASK) != 0) {
        return ESP_ERR_INVALID_ARG;
    }

    return uwb_dw3000_update_u32(DW3000_REG_GEN_CFG_AES_HIGH,
                                 DW3000_ACK_RESP_SUB,
                                 DW3000_ACK_RESP_W4R_TIM_BIT_MASK,
                                 rx_after_tx_delay_uus);
}

static esp_err_t uwb_dw3000_set_rx_timeout(uint32_t timeout_ms)
{
    if (timeout_ms == 0) {
        return uwb_dw3000_update_u32(DW3000_REG_GEN_CFG_AES_LOW,
                                     DW3000_SYS_CFG_SUB,
                                     DW3000_SYS_CFG_RXWTOE_BIT_MASK, 0);
    }

    const uint32_t timeout_units = timeout_ms * 1000UL;
    ESP_RETURN_ON_ERROR(
        uwb_dw3000_write_u32_len(DW3000_REG_GEN_CFG_AES_LOW,
                                 DW3000_RX_FWTO_SUB, timeout_units, 4),
        TAG, "RX_FWTO write failed");
    return uwb_dw3000_update_u32(DW3000_REG_GEN_CFG_AES_LOW,
                                 DW3000_SYS_CFG_SUB, 0,
                                 DW3000_SYS_CFG_RXWTOE_BIT_MASK);
}

static esp_err_t uwb_dw3000_prepare_rx_after_tx(uint32_t delay_uus,
                                                uint32_t timeout_ms)
{
    ESP_RETURN_ON_ERROR(uwb_dw3000_set_rx_after_tx_delay(delay_uus), TAG,
                        "RX-after-TX delay config failed");
    ESP_RETURN_ON_ERROR(uwb_dw3000_set_rx_timeout(timeout_ms), TAG,
                        "RX timeout config failed");
    return ESP_OK;
}

static bool uwb_dw3000_sts_mode_supported(uint32_t sts_mode)
{
    const uint32_t protocol = sts_mode & 0x3UL;
    const uint32_t allowed_bits = 0xBUL;

    if ((sts_mode & ~allowed_bits) != 0) {
        return false;
    }

    if (sts_mode == APP_UWB_STS_MODE_OFF) {
        return true;
    }

    return protocol == APP_UWB_STS_MODE_1 ||
           protocol == APP_UWB_STS_MODE_2;
}

static esp_err_t uwb_dw3000_sts_length_reg_value(uint32_t symbols,
                                                 uint8_t *reg_value)
{
    if (reg_value == NULL) {
        return ESP_ERR_INVALID_ARG;
    }

    switch (symbols) {
    case 32:
    case 64:
    case 128:
    case 256:
    case 512:
    case 1024:
    case 2048:
        *reg_value = (uint8_t)((symbols / 8U) - 1U);
        return ESP_OK;
    default:
        return ESP_ERR_INVALID_ARG;
    }
}

static const char *uwb_dw3000_sts_mode_name(uint32_t sts_mode)
{
    switch (sts_mode) {
    case APP_UWB_STS_MODE_OFF:
        return "off";
    case APP_UWB_STS_MODE_1:
        return "mode1";
    case APP_UWB_STS_MODE_2:
        return "mode2";
    case APP_UWB_STS_MODE_1 | APP_UWB_STS_MODE_SDC:
        return "mode1_sdc";
    case APP_UWB_STS_MODE_2 | APP_UWB_STS_MODE_SDC:
        return "mode2_sdc";
    default:
        return "unsupported";
    }
}

static esp_err_t uwb_dw3000_configure_sts(void)
{
    const uint32_t sts_mode = APP_UWB_STS_MODE & 0xFUL;
    uint8_t sts_len_reg = 0;

    if (!uwb_dw3000_sts_mode_supported(sts_mode)) {
        ESP_LOGE(TAG, "Unsupported STS mode 0x%lx for data frames",
                 (unsigned long)sts_mode);
        return ESP_ERR_NOT_SUPPORTED;
    }

    ESP_RETURN_ON_ERROR(
        uwb_dw3000_sts_length_reg_value(APP_UWB_STS_LENGTH_SYMBOLS,
                                        &sts_len_reg),
        TAG, "invalid STS length");

    ESP_RETURN_ON_ERROR(
        uwb_dw3000_write_u32_len(DW3000_REG_STS_CFG, DW3000_SUB_NONE,
                                 sts_len_reg, 1),
        TAG, "STS length write failed");
    ESP_RETURN_ON_ERROR(
        uwb_dw3000_update_u32(DW3000_REG_GEN_CFG_AES_LOW, DW3000_SYS_CFG_SUB,
                              DW3000_SYS_CFG_STS_MODE_MASK,
                              sts_mode << DW3000_SYS_CFG_STS_MODE_SHIFT),
        TAG, "STS mode write failed");

    if (sts_mode != APP_UWB_STS_MODE_OFF) {
        ESP_RETURN_ON_ERROR(
            uwb_dw3000_update_u32(DW3000_REG_CIA_3,
                                  DW3000_STS_CONFIG_HI_SUB,
                                  DW3000_STS_CONFIG_HI_CHECK_MASK,
                                  DW3000_STS_CONFIG_HI_RES),
            TAG, "STS quality config write failed");
    }

    ESP_LOGI(TAG, "DW3000 STS config: mode=%s(0x%lx) length=%u symbols",
             uwb_dw3000_sts_mode_name(sts_mode), (unsigned long)sts_mode,
             (unsigned)APP_UWB_STS_LENGTH_SYMBOLS);
    return ESP_OK;
}

static esp_err_t uwb_dw3000_configure_event_counters(void)
{
#if APP_UWB_EVENT_COUNTERS_ENABLED
    ESP_RETURN_ON_ERROR(
        uwb_dw3000_write_u32_len(DW3000_REG_DIG_DIAG, DW3000_EVC_CTRL_SUB,
                                 DW3000_EVC_CTRL_CLR_BIT_MASK, 1),
        TAG, "event counter clear failed");
    ESP_RETURN_ON_ERROR(
        uwb_dw3000_write_u32_len(DW3000_REG_DIG_DIAG, DW3000_EVC_CTRL_SUB,
                                 DW3000_EVC_CTRL_EN_BIT_MASK, 1),
        TAG, "event counter enable failed");
    ESP_LOGI(TAG, "DW3000 event counters enabled");
#else
    ESP_RETURN_ON_ERROR(
        uwb_dw3000_write_u32_len(DW3000_REG_DIG_DIAG, DW3000_EVC_CTRL_SUB, 0,
                                 1),
        TAG, "event counter disable failed");
    ESP_LOGI(TAG, "DW3000 event counters disabled");
#endif
    return ESP_OK;
}

static esp_err_t
uwb_dw3000_read_event_counters(struct uwb_event_counters *counters)
{
    if (counters == NULL) {
        return ESP_ERR_INVALID_ARG;
    }

    memset(counters, 0, sizeof(*counters));

#if APP_UWB_EVENT_COUNTERS_ENABLED
    /* COUNT0..COUNT7 occupy one register-file span (with reserved holes).
     * Reading the span in one SPI transaction keeps live diagnostics from
     * adding eight separate command/header latencies to the RX task. */
    uint8_t raw[(DW3000_EVC_COUNT7_SUB + sizeof(uint32_t)) -
                DW3000_EVC_COUNT0_SUB] = {0};
    ESP_RETURN_ON_ERROR(
        uwb_dw3000_read_bytes(DW3000_REG_DIG_DIAG,
                              DW3000_EVC_COUNT0_SUB, raw, sizeof(raw)),
        TAG, "EVC counter span read failed");
#define UWB_EVC_RAW32(sub)                                                \
    uwb_distance_get_u32(raw, (size_t)((sub) - DW3000_EVC_COUNT0_SUB))
    const uint32_t count0 = UWB_EVC_RAW32(DW3000_EVC_COUNT0_SUB);
    const uint32_t count1 = UWB_EVC_RAW32(DW3000_EVC_COUNT1_SUB);
    const uint32_t count2 = UWB_EVC_RAW32(DW3000_EVC_COUNT2_SUB);
    const uint32_t count3 = UWB_EVC_RAW32(DW3000_EVC_COUNT3_SUB);
    const uint32_t count4 = UWB_EVC_RAW32(DW3000_EVC_COUNT4_SUB);
    const uint32_t count5 = UWB_EVC_RAW32(DW3000_EVC_COUNT5_SUB);
    const uint32_t count6 = UWB_EVC_RAW32(DW3000_EVC_COUNT6_SUB);
    const uint32_t count7 = UWB_EVC_RAW32(DW3000_EVC_COUNT7_SUB);
#undef UWB_EVC_RAW32

    counters->phe = (uint16_t)(count0 & DW3000_EVC_12BIT_LOW_MASK);
    counters->rse = (uint16_t)((count0 & DW3000_EVC_12BIT_HIGH_MASK) >>
                               DW3000_EVC_HIGH_SHIFT);
    counters->fcg = (uint16_t)(count1 & DW3000_EVC_12BIT_LOW_MASK);
    counters->fce = (uint16_t)((count1 & DW3000_EVC_12BIT_HIGH_MASK) >>
                               DW3000_EVC_HIGH_SHIFT);
    counters->ffr = (uint8_t)(count2 & DW3000_EVC_8BIT_LOW_MASK);
    counters->ovr = (uint8_t)((count2 & DW3000_EVC_8BIT_HIGH_MASK) >>
                              DW3000_EVC_HIGH_SHIFT);
    counters->sfdt = (uint16_t)(count3 & DW3000_EVC_12BIT_LOW_MASK);
    counters->pto = (uint16_t)((count3 & DW3000_EVC_12BIT_HIGH_MASK) >>
                               DW3000_EVC_HIGH_SHIFT);
    counters->fwto = (uint8_t)(count4 & DW3000_EVC_8BIT_LOW_MASK);
    counters->txfs = (uint16_t)((count4 & DW3000_EVC_12BIT_HIGH_MASK) >>
                                DW3000_EVC_HIGH_SHIFT);
    counters->hpw = (uint8_t)(count5 & DW3000_EVC_8BIT_LOW_MASK);
    counters->swce = (uint8_t)((count5 & DW3000_EVC_8BIT_HIGH_MASK) >>
                               DW3000_EVC_HIGH_SHIFT);
    counters->prej = (uint16_t)(count6 & DW3000_EVC_12BIT_LOW_MASK);
    counters->cpqe = (uint8_t)(count7 & DW3000_EVC_8BIT_LOW_MASK);
    counters->vwarn = (uint8_t)((count7 & DW3000_EVC_8BIT_HIGH_MASK) >>
                                DW3000_EVC_HIGH_SHIFT);
#endif

    return ESP_OK;
}

static bool uwb_dw3000_should_log_event_counters(uint16_t sequence)
{
#if APP_UWB_EVENT_COUNTERS_ENABLED
    if (APP_UWB_EVENT_COUNTERS_LOG_EVERY == 0) {
        return false;
    }
    return (sequence % APP_UWB_EVENT_COUNTERS_LOG_EVERY) == 0;
#else
    (void)sequence;
    return false;
#endif
}

static void uwb_dw3000_maybe_log_event_counters(uint16_t sequence)
{
    if (!uwb_dw3000_should_log_event_counters(sequence)) {
        return;
    }

    struct uwb_event_counters counters = {0};
    const esp_err_t err = uwb_dw3000_read_event_counters(&counters);
    if (err != ESP_OK) {
        ESP_LOGW(TAG, "DW3000 event counter read failed seq=%u: %s",
                 (unsigned)sequence, esp_err_to_name(err));
        return;
    }

    ESP_LOGI(TAG,
             "DW3000 counters seq=%u fcg=%u fce=%u phe=%u rse=%u sfdt=%u pto=%u fwto=%u txfs=%u hpw=%u prej=%u cpqe=%u vwarn=%u ffr=%u ovr=%u",
             (unsigned)sequence, (unsigned)counters.fcg,
             (unsigned)counters.fce, (unsigned)counters.phe,
             (unsigned)counters.rse, (unsigned)counters.sfdt,
             (unsigned)counters.pto, (unsigned)counters.fwto,
             (unsigned)counters.txfs, (unsigned)counters.hpw,
             (unsigned)counters.prej, (unsigned)counters.cpqe,
             (unsigned)counters.vwarn, (unsigned)counters.ffr,
             (unsigned)counters.ovr);
}

static esp_err_t uwb_dw3000_read_rx_payload(
    uint8_t payload[UWB_DW3000_PAYLOAD_LEN], uint16_t *payload_len)
{
    if (payload == NULL || payload_len == NULL) {
        return ESP_ERR_INVALID_ARG;
    }

    uint8_t finfo_base = DW3000_REG_GEN_CFG_AES_LOW;
    uint8_t finfo_sub = DW3000_RX_FINFO_SUB;
    uint8_t payload_base = DW3000_REG_RX_BUFFER_0;
    if (s_rx_double_buffer_enabled) {
        if (s_rx_double_buffer_index == 0U) {
            finfo_base = DW3000_REG_DOUBLE_BUFFER_DIAG;
            finfo_sub = DW3000_DOUBLE_BUFFER_0_RX_FINFO_SUB;
        } else {
            finfo_base = DW3000_REG_INDIRECT_POINTER_B;
            finfo_sub = DW3000_DOUBLE_BUFFER_1_RX_FINFO_OFFSET;
            payload_base = DW3000_REG_RX_BUFFER_1;
        }
    }

    uint32_t rx_finfo = 0;
    ESP_RETURN_ON_ERROR(uwb_dw3000_read32(finfo_base, finfo_sub, &rx_finfo),
                        TAG, "RX_FINFO read failed");

    const uint16_t frame_len =
        (uint16_t)(rx_finfo & DW3000_RX_FINFO_RXFLEN_MASK);
    if (frame_len <= 2U) {
        *payload_len = 0;
        return ESP_OK;
    }

    uint16_t read_len = (uint16_t)(frame_len - 2U);
    if (read_len > UWB_DW3000_PAYLOAD_LEN) {
        read_len = UWB_DW3000_PAYLOAD_LEN;
    }

    memset(payload, 0, UWB_DW3000_PAYLOAD_LEN);
    ESP_RETURN_ON_ERROR(
        uwb_dw3000_read_bytes(payload_base, DW3000_SUB_NONE, payload, read_len),
        TAG, "RX buffer read failed");
    *payload_len = read_len;
    return ESP_OK;
}

// Adjacent FlexTDOA frames are separated by much less than the 67 ms wrap of
// RX_TIME's low 32 bits. Extending every timestamp from the previous one is
// therefore unambiguous and avoids the occasionally corrupt upper byte in the
// double-buffer diagnostic set.
static esp_err_t uwb_flex_tdoa_extend_rx_timestamp32(
    uint32_t low32, uint64_t *timestamp)
{
    if (timestamp == NULL) {
        return ESP_ERR_INVALID_ARG;
    }

    const int64_t now_us = esp_timer_get_time();
    if (!s_flex_tdoa_rx_timestamp_reference_valid ||
        now_us - s_flex_tdoa_rx_timestamp_reference_host_us >
            UWB_FLEX_TDOA_RX_EPOCH_MAX_GAP_US) {
        uint32_t system_time_word = 0;
        ESP_RETURN_ON_ERROR(
            uwb_dw3000_read32(DW3000_REG_GEN_CFG_AES_LOW,
                              DW3000_SYS_TIME_SUB, &system_time_word),
            TAG, "FlexTDOA radio-time recovery seed failed");
        s_flex_tdoa_rx_timestamp_reference =
            ((uint64_t)system_time_word << 8U) &
            UWB_DW3000_TIMESTAMP_MASK;
        s_flex_tdoa_rx_timestamp_reference_valid = true;
    }

    const int32_t delta =
        (int32_t)(low32 - (uint32_t)s_flex_tdoa_rx_timestamp_reference);
    s_flex_tdoa_rx_timestamp_reference =
        (s_flex_tdoa_rx_timestamp_reference + (int64_t)delta) &
        UWB_DW3000_TIMESTAMP_MASK;
    s_flex_tdoa_rx_timestamp_reference_host_us = now_us;
    *timestamp = s_flex_tdoa_rx_timestamp_reference;
    return ESP_OK;
}

// Double-buffer timing metadata is contiguous: RX_FINFO starts at byte 0 and
// RX_TIME at byte 4. FlexTDOA additionally reads CIA_DIAG_0 at byte 12; PDS3
// stops after RX_TIME because Eq19 does not use per-packet CFO. Payload and
// metadata are read in two compact SPI bursts.

static esp_err_t uwb_dw3000_read_flex_buffered_metadata(
    struct uwb_dw3000_rx_frame *frame, uint16_t *frame_len)
{
    if (frame == NULL || frame_len == NULL || !s_rx_double_buffer_enabled) {
        return ESP_ERR_INVALID_ARG;
    }

    const uint8_t diag_base = s_rx_double_buffer_index == 0U
                                  ? DW3000_REG_DOUBLE_BUFFER_DIAG
                                  : DW3000_REG_INDIRECT_POINTER_B;
    uint8_t metadata[DW3000_DOUBLE_BUFFER_FLEX_META_LEN] = {0};
    const size_t metadata_len =
        s_runtime_mode == UWB_DW3000_RUNTIME_PASSIVE_DS_TWR
            ? DW3000_DOUBLE_BUFFER_RX_META_LEN
            : sizeof(metadata);
    ESP_RETURN_ON_ERROR(
        uwb_dw3000_read_bytes(diag_base, 0, metadata, metadata_len), TAG,
        "FlexTDOA buffered metadata read failed");

    const uint32_t rx_finfo = ((uint32_t)metadata[0]) |
                              ((uint32_t)metadata[1] << 8U) |
                              ((uint32_t)metadata[2] << 16U) |
                              ((uint32_t)metadata[3] << 24U);
    *frame_len = (uint16_t)(rx_finfo & DW3000_RX_FINFO_RXFLEN_MASK);

    const uint32_t rx_time_low32 = ((uint32_t)metadata[4]) |
                                   ((uint32_t)metadata[5] << 8U) |
                                   ((uint32_t)metadata[6] << 16U) |
                                   ((uint32_t)metadata[7] << 24U);
    ESP_RETURN_ON_ERROR(
        uwb_flex_tdoa_extend_rx_timestamp32(rx_time_low32,
                                            &frame->rx_timestamp),
        TAG, "FlexTDOA buffered RX timestamp extension failed");

    if (metadata_len == sizeof(metadata)) {
        const uint16_t raw =
            (uint16_t)(((uint16_t)metadata[12]) |
                       ((uint16_t)metadata[13] << 8U));
        frame->clock_offset_raw =
            uwb_dw3000_sign_extend(raw & 0x1FFFU, 13U);
        frame->clock_offset_from_cia = true;
    } else {
        frame->clock_offset_raw = 0;
        frame->clock_offset_from_cia = false;
    }
    frame->clock_offset_valid = false;
    return ESP_OK;
}

static esp_err_t uwb_dw3000_read_flex_buffered_frame(
    struct uwb_dw3000_rx_frame *frame)
{
    if (frame == NULL || !s_rx_double_buffer_enabled) {
        return ESP_ERR_INVALID_ARG;
    }

    uint16_t frame_len = 0;
    ESP_RETURN_ON_ERROR(
        uwb_dw3000_read_flex_buffered_metadata(frame, &frame_len), TAG,
        "FlexTDOA buffered metadata unavailable");
    if (frame_len <= 2U) {
        frame->payload_len = 0;
        return ESP_OK;
    }

    uint16_t read_len = (uint16_t)(frame_len - 2U);
    if (read_len > UWB_DW3000_PAYLOAD_LEN) {
        read_len = UWB_DW3000_PAYLOAD_LEN;
    }
    const uint8_t payload_base = s_rx_double_buffer_index == 0U
                                     ? DW3000_REG_RX_BUFFER_0
                                     : DW3000_REG_RX_BUFFER_1;
    memset(frame->payload, 0, sizeof(frame->payload));
    ESP_RETURN_ON_ERROR(
        uwb_dw3000_read_bytes(payload_base, DW3000_SUB_NONE, frame->payload,
                              read_len),
        TAG, "FlexTDOA RX buffer read failed");
    frame->payload_len = read_len;
    /*
     * RX-good does not imply CIADONE. The caller validates RDB_STATUS after
     * identifying a response and re-reads CIA_DIAG_0 if CIA completed while
     * the metadata and payload were being copied.
     */
    frame->clock_offset_valid = false;
    return ESP_OK;
}

static esp_err_t uwb_dw3000_write_tx_payload(const uint8_t *payload,
                                             size_t payload_len)
{
    if (payload == NULL || payload_len == 0 ||
        payload_len > UWB_DW3000_PAYLOAD_LEN) {
        return ESP_ERR_INVALID_ARG;
    }

    return uwb_dw3000_write_bytes(DW3000_REG_TX_BUFFER, DW3000_SUB_NONE,
                                  payload, payload_len);
}

static esp_err_t uwb_dw3000_fast_command(uint8_t command)
{
    const uint8_t header = (uint8_t)(0x81U | ((command & 0x1FU) << 1));
    spi_transaction_t transaction = {
        .flags = SPI_TRANS_USE_TXDATA,
        .length = 8,
    };
    transaction.tx_data[0] = header;
    return spi_device_polling_transmit(s_spi, &transaction);
}

static esp_err_t uwb_dw3000_clear_status(void)
{
    return uwb_dw3000_write_u32_len(DW3000_REG_GEN_CFG_AES_LOW, 0x44,
                                    DW3000_STATUS_CLEAR_MASK, 4);
}
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
