victorstoica114/UWB_Module_ESP_IDF/components/uwb_dw3000/uwb_native_ds_twr.c

#include "uwb_native_ds_twr.h"

#include <math.h>
#include <string.h>

#include "esp_log.h"
#include "uwb_native_ds_protocol.h"

static const char *TAG = "native_ds_twr";

#define NATIVE_DS_SLOT_GUARD_MS 1U
#define NATIVE_DS_DIAGNOSTIC_INTERVAL_FRAMES 16U

struct native_ds_received_packet {
    struct uwb_native_ds_packet packet;
    uint64_t rx_timestamp;
};

static struct uwb_native_ds_pipeline_stats s_stats;

static uint32_t remaining_ms(const struct uwb_native_ds_radio_ops *radio,
                             int64_t started_us, uint32_t timeout_ms)
{
    const int64_t elapsed_us = radio->now_us(radio->context) - started_us;
    const int64_t timeout_us = (int64_t)timeout_ms * 1000LL;
    if (elapsed_us >= timeout_us) {
        return 0U;
    }
    return (uint32_t)((timeout_us - elapsed_us + 999LL) / 1000LL);
}

static esp_err_t receive_matching(
    const struct uwb_native_ds_config *config,
    const struct uwb_native_ds_radio_ops *radio,
    enum uwb_native_ds_message_type expected_type, uint8_t expected_source,
    uint32_t expected_session_id, uint32_t expected_frame_id,
    uint32_t timeout_ms, struct native_ds_received_packet *received_packet)
{
    const int64_t started_us = radio->now_us(radio->context);
    while (!radio->stop_requested(radio->context)) {
        const uint32_t wait_ms = remaining_ms(radio, started_us, timeout_ms);
        if (wait_ms == 0U) {
            s_stats.rx_timeout_count++;
            return ESP_ERR_TIMEOUT;
        }
        struct uwb_native_ds_rx_frame received = {0};
        const esp_err_t err =
            radio->receive(radio->context, &received, wait_ms);
        if (err != ESP_OK) {
            if (err == ESP_ERR_TIMEOUT) {
                s_stats.rx_timeout_count++;
            } else if (err == ESP_ERR_INVALID_RESPONSE) {
                /*
                 * A DW3000 PHY error can precede the expected frame in the
                 * same receive window.  The driver has already stopped RX,
                 * cleared the error status and marked the receiver for
                 * re-arm.  Keep the original absolute timeout and let the
                 * next receive call re-arm instead of discarding the whole
                 * exchange immediately.
                 */
                s_stats.recovered_rx_error_count++;
                continue;
            }
            return err;
        }
        struct uwb_native_ds_packet packet = {0};
        const enum uwb_native_ds_decode_result decode_result =
            uwb_native_ds_protocol_decode_ex(
                received.payload, received.payload_len, &packet);
        if (decode_result != UWB_NATIVE_DS_DECODE_OK) {
            if (decode_result == UWB_NATIVE_DS_DECODE_CRC_ERROR) {
                s_stats.crc_error_count++;
            }
            continue;
        }
        if (packet.type == expected_type &&
            packet.source_id == expected_source &&
            packet.destination_id == config->source_id &&
            packet.session_id == expected_session_id &&
            packet.frame_id == expected_frame_id) {
            received_packet->packet = packet;
            received_packet->rx_timestamp =
                received.rx_timestamp & UWB_NATIVE_DS_TIMESTAMP_MASK;
            return ESP_OK;
        }
        if (packet.destination_id == config->source_id) {
            s_stats.invalid_frame_count++;
        }
    }
    return ESP_ERR_INVALID_STATE;
}

static bool encode_packet(const struct uwb_native_ds_packet *packet,
                          uint8_t payload[UWB_NATIVE_DS_MAX_FRAME_LEN],
                          size_t *payload_len)
{
    return uwb_native_ds_protocol_encode(
        packet, payload, UWB_NATIVE_DS_MAX_FRAME_LEN, payload_len);
}

static bool delayed_timestamp_valid(uint64_t expected, uint64_t programmed,
                                    uint64_t actual)
{
    return (expected & UWB_NATIVE_DS_TIMESTAMP_MASK) ==
               (programmed & UWB_NATIVE_DS_TIMESTAMP_MASK) &&
           (programmed & UWB_NATIVE_DS_TIMESTAMP_MASK) ==
               (actual & UWB_NATIVE_DS_TIMESTAMP_MASK);
}

static esp_err_t tag_exchange(
    const struct uwb_native_ds_config *config,
    const struct uwb_native_ds_radio_ops *radio, size_t anchor_index,
    uint32_t session_id, uint32_t frame_id)
{
    const uint8_t anchor_id = config->anchor_ids[anchor_index];
    struct uwb_native_ds_tag_anchor_stats *anchor_stats =
        &s_stats.tag_anchors[anchor_index];
    anchor_stats->attempt_count++;

    uint8_t payload[UWB_NATIVE_DS_MAX_FRAME_LEN] = {0};
    size_t payload_len = 0U;
    struct uwb_native_ds_packet packet = {
        .type = UWB_NATIVE_DS_MESSAGE_POLL,
        .exchange_kind = UWB_NATIVE_DS_EXCHANGE_TAG_RANGE,
        .source_id = config->tag_id,
        .destination_id = anchor_id,
        .session_id = session_id,
        .frame_id = frame_id,
    };
    if (!encode_packet(&packet, payload, &payload_len)) {
        return ESP_ERR_INVALID_STATE;
    }

    uint64_t poll_tx = 0U;
    esp_err_t err = radio->send_immediate_expect_rx(
        radio->context, payload, payload_len, config->auto_rx_delay_uus,
        config->rx_timeout_ms, &poll_tx);
    if (err != ESP_OK) {
        s_stats.poll_tx_error_count++;
        anchor_stats->poll_tx_error_count++;
        return err;
    }
    s_stats.poll_tx_count++;

    struct native_ds_received_packet response = {0};
    err = receive_matching(config, radio, UWB_NATIVE_DS_MESSAGE_RESPONSE,
                           anchor_id, session_id, frame_id,
                           config->rx_timeout_ms, &response);
    if (err != ESP_OK) {
        if (err == ESP_ERR_TIMEOUT) {
            s_stats.response_timeout_count++;
            anchor_stats->response_timeout_count++;
        } else if (!radio->stop_requested(radio->context)) {
            s_stats.response_rx_error_count++;
            anchor_stats->response_rx_error_count++;
        }
        return err;
    }
    s_stats.response_rx_count++;

    const uint64_t final_due = radio->add_delay_ms(
        radio->context, response.rx_timestamp, config->final_delay_ms);
    const uint64_t expected_final_tx = radio->programmed_tx_timestamp(
        radio->context, final_due);
    packet.type = UWB_NATIVE_DS_MESSAGE_FINAL;
    packet.poll_tx_timestamp = poll_tx;
    packet.response_rx_timestamp = response.rx_timestamp;
    packet.final_tx_timestamp = expected_final_tx;
    if (!encode_packet(&packet, payload, &payload_len)) {
        return ESP_ERR_INVALID_STATE;
    }

    uint64_t programmed_final_tx = 0U;
    uint64_t actual_final_tx = 0U;
    err = radio->send_delayed_expect_rx(
        radio->context, payload, payload_len, final_due,
        config->auto_rx_delay_uus, config->rx_timeout_ms,
        &programmed_final_tx, &actual_final_tx);
    if (err != ESP_OK ||
        !delayed_timestamp_valid(expected_final_tx, programmed_final_tx,
                                 actual_final_tx)) {
        s_stats.delayed_tx_error_count++;
        s_stats.final_tx_error_count++;
        anchor_stats->final_tx_error_count++;
        return err == ESP_OK ? ESP_ERR_INVALID_STATE : err;
    }
    s_stats.final_tx_count++;

    struct native_ds_received_packet result = {0};
    err = receive_matching(config, radio, UWB_NATIVE_DS_MESSAGE_RESULT,
                           anchor_id, session_id, frame_id,
                           config->rx_timeout_ms, &result);
    if (err != ESP_OK) {
        if (err == ESP_ERR_TIMEOUT) {
            s_stats.result_timeout_count++;
            anchor_stats->result_timeout_count++;
        } else if (!radio->stop_requested(radio->context)) {
            s_stats.result_rx_error_count++;
            anchor_stats->result_rx_error_count++;
        }
        return err;
    }
    s_stats.result_rx_count++;
    const double distance_m = (double)result.packet.distance_mm / 1000.0;
    if (!isfinite(distance_m) || distance_m <= 0.0 ||
        distance_m > config->maximum_distance_m) {
        s_stats.rejected_range_count++;
        return ESP_ERR_INVALID_RESPONSE;
    }
    s_stats.completed_range_count++;
    anchor_stats->completed_range_count++;
    s_stats.last_distance_mm = (int32_t)result.packet.distance_mm;
    radio->consume_report(radio->context, true, config->tag_id, anchor_id,
                          frame_id, distance_m,
                          &result.packet.sender_position);
    return ESP_OK;
}

static bool run_tag_slot(const struct uwb_native_ds_config *config,
                         const struct uwb_native_ds_radio_ops *radio,
                         size_t anchor_index, uint32_t session_id,
                         uint32_t frame_id)
{
    const int64_t slot_started_us = radio->now_us(radio->context);
    const esp_err_t err = tag_exchange(
        config, radio, anchor_index, session_id, frame_id);
    if (err != ESP_OK && err != ESP_ERR_TIMEOUT) {
        ESP_LOGW(TAG, "tag exchange anchor=%u frame=%lu failed: %s",
                 (unsigned)config->anchor_ids[anchor_index],
                 (unsigned long)frame_id, esp_err_to_name(err));
    }
    const int64_t elapsed_us =
        radio->now_us(radio->context) - slot_started_us;
    const int64_t slot_us = (int64_t)config->slot_ms * 1000LL;
    if (elapsed_us < slot_us) {
        radio->wait_until_us(radio->context, slot_started_us + slot_us);
    } else {
        s_stats.slot_overrun_count++;
    }
    return err == ESP_OK;
}

static size_t single_missing_anchor_index(uint32_t missing_anchor_mask,
                                          size_t anchor_count)
{
    if (missing_anchor_mask == 0U ||
        (missing_anchor_mask & (missing_anchor_mask - 1U)) != 0U) {
        return anchor_count;
    }
    for (size_t index = 0U; index < anchor_count; ++index) {
        if ((missing_anchor_mask & (1UL << index)) != 0U) {
            return index;
        }
    }
    return anchor_count;
}

static void run_tag(const struct uwb_native_ds_config *config,
                    const struct uwb_native_ds_radio_ops *radio)
{
    uint32_t session_id = (uint32_t)radio->now_us(radio->context);
    if (session_id == 0U) {
        session_id = 1U;
    }
    uint32_t frame_id = 1U;
    radio->set_ready(radio->context);
    ESP_LOGI(TAG,
             "tag active id=%u session=%lu anchors=%u slot=%lu ms "
             "resp/final/result=%lu/%lu/%lu ms",
             (unsigned)config->tag_id, (unsigned long)session_id,
             (unsigned)config->anchor_count, (unsigned long)config->slot_ms,
             (unsigned long)config->response_delay_ms,
             (unsigned long)config->final_delay_ms,
             (unsigned long)config->response_delay_ms);

    while (!radio->stop_requested(radio->context)) {
        const uint32_t current_frame_id = frame_id++;
        uint32_t completed_anchor_mask = 0U;
        if (frame_id == 0U) {
            frame_id = 1U;
        }
        for (size_t slot = 0U;
             slot < config->anchor_count &&
             !radio->stop_requested(radio->context);
             ++slot) {
            /* Rotate the physical anchor order every frame.  This keeps the
             * 0..N-1 acquisition-time offsets from belonging permanently to
             * the same anchors while preserving one coherent frame ID. */
            const size_t index =
                (slot + (size_t)(current_frame_id - 1U)) %
                config->anchor_count;
            if (run_tag_slot(config, radio, index, session_id,
                             current_frame_id)) {
                completed_anchor_mask |= 1UL << index;
            }
        }
        const uint32_t expected_anchor_mask =
            (1UL << config->anchor_count) - 1UL;
        uint32_t missing_anchor_mask =
            expected_anchor_mask & ~completed_anchor_mask;
        const size_t recovery_index = single_missing_anchor_index(
            missing_anchor_mask, config->anchor_count);
        if (recovery_index < config->anchor_count &&
            !radio->stop_requested(radio->context)) {
            /* One targeted retry is still frame-local.  It converts the
             * common single-link loss into a true 4/4 solution instead of
             * asking the solver to infer an outlier from only three ranges. */
            s_stats.recovery_attempt_count++;
            s_stats.last_recovery_anchor_id =
                config->anchor_ids[recovery_index];
            if (run_tag_slot(config, radio, recovery_index, session_id,
                             current_frame_id)) {
                completed_anchor_mask |= 1UL << recovery_index;
                s_stats.recovery_success_count++;
            }
            missing_anchor_mask =
                expected_anchor_mask & ~completed_anchor_mask;
        }
        s_stats.last_frame_missing_anchor_mask =
            missing_anchor_mask;
        if (completed_anchor_mask == expected_anchor_mask) {
            s_stats.complete_frame_count++;
        } else {
            s_stats.incomplete_frame_count++;
        }
        if (config->round_gap_ms > 0U &&
            !radio->stop_requested(radio->context)) {
            const int64_t gap_started_us =
                radio->now_us(radio->context);
            radio->wait_until_us(
                radio->context,
                gap_started_us + (int64_t)config->round_gap_ms * 1000LL);
        }
    }
}
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
