victorstoica114/UWB_Module_ESP_IDF/components/gps_service/gps_ntrip_client.c

#include "gps_ntrip_client.h"
#include "gps_ntrip_stream_decoder.h"

#include <errno.h>
#include <fcntl.h>
#include <stdio.h>
#include <stdlib.h>
#include <string.h>
#include <sys/socket.h>
#include <sys/time.h>
#include <unistd.h>

#include "esp_crt_bundle.h"
#include "esp_heap_caps.h"
#include "esp_log.h"
#include "esp_tls.h"
#include "freertos/FreeRTOS.h"
#include "freertos/semphr.h"
#include "freertos/task.h"
#include "lwip/netdb.h"
#include "mbedtls/base64.h"
#include "mbedtls/ssl.h"
#include "secrets.h"
#include "wifi_service.h"

#ifndef NTRIP_ENABLED
#define NTRIP_ENABLED 0
#endif
#ifndef NTRIP_MODULE_ID
#define NTRIP_MODULE_ID 1
#endif
#ifndef NTRIP_USE_TLS
#define NTRIP_USE_TLS 1
#endif
#ifndef NTRIP_GGA_INTERVAL_MS
#define NTRIP_GGA_INTERVAL_MS 10000
#endif

static const char *TAG = "gps_ntrip";

enum {
    GPS_NTRIP_TASK_STACK_BYTES = 8192,
    GPS_NTRIP_TASK_PRIORITY = 4,
    GPS_NTRIP_CONNECT_TIMEOUT_MS = 10000,
    GPS_NTRIP_READ_TIMEOUT_MS = 1000,
    GPS_NTRIP_RECONNECT_DELAY_MS = 2000,
    GPS_NTRIP_STOP_TIMEOUT_MS = 3000,
    GPS_NTRIP_BUFFER_SIZE = 1024,
    GPS_NTRIP_HEADER_SIZE = 2048,
    GPS_NTRIP_GGA_SIZE = 192,
};

typedef struct {
    uint8_t header[3];
    uint8_t header_length;
    uint16_t remaining;
} rtcm_counter_t;

typedef struct {
    uint8_t buffer[GPS_NTRIP_BUFFER_SIZE];
    char header[GPS_NTRIP_HEADER_SIZE];
    char request[GPS_NTRIP_HEADER_SIZE];
    char credentials[768];
    char authorization[1024];
    char gga_line[GPS_NTRIP_GGA_SIZE + 2];
    gps_ntrip_chunk_decoder_t chunk_decoder;
} ntrip_workspace_t;

static SemaphoreHandle_t s_mutex;
static TaskHandle_t s_task;
static volatile bool s_stop_requested;
#if NTRIP_USE_TLS
static esp_tls_t *s_tls;
#endif
static int s_socket = -1;
static uint8_t s_module_id;
static gps_ntrip_write_fn_t s_write_fn;
static void *s_write_context;
static char s_gga[GPS_NTRIP_GGA_SIZE];
static uint32_t s_gga_updated_ms;
static uint32_t s_last_data_ms;
static gps_ntrip_snapshot_t s_snapshot;
static rtcm_counter_t s_rtcm_counter;

static uint32_t ticks_to_ms(void)
{
    return (uint32_t)(xTaskGetTickCount() * portTICK_PERIOD_MS);
}

static bool lock_state(TickType_t timeout)
{
    return s_mutex != NULL && xSemaphoreTake(s_mutex, timeout) == pdTRUE;
}

static void unlock_state(void)
{
    if (s_mutex != NULL) {
        xSemaphoreGive(s_mutex);
    }
}

static void set_state(const char *state)
{
    if (lock_state(pdMS_TO_TICKS(50))) {
        snprintf(s_snapshot.state, sizeof(s_snapshot.state), "%s", state);
        unlock_state();
    }
}

static void note_error(const char *state)
{
    if (lock_state(pdMS_TO_TICKS(50))) {
        s_snapshot.error_count++;
        snprintf(s_snapshot.state, sizeof(s_snapshot.state), "%s", state);
        unlock_state();
    }
}

static bool copy_gga(char *destination, size_t capacity)
{
    bool available = false;
    if (lock_state(pdMS_TO_TICKS(50))) {
        if (s_gga[0] != '\0') {
            snprintf(destination, capacity, "%s", s_gga);
            available = true;
        }
        unlock_state();
    }
    return available;
}
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
